skylar-slideshows/Digilog_Capstone/Hardware_Documentation/HW_design_stuff/sim/4 Design - Fader Pan/Volume Control and Digital Fader Design.docx

Volume Control and Digital Fader Design

We want a device that allows the volume of channels to be controlled with a slide potentiometer (Fader). Instead of a traditional analog design with the audio signal running through the fader’s resistance strip itself, we use a microcontroller to read the position of the fader through its resistance. That microcontroller then addresses the VCA with a control voltage that produces the specified gain/atten.

This has the benefit of being instantly recallable and able to be saved and automated digitally.

Microcontroller for each bucket of 8 faders = RP2040. $1 per bucket

The ALPS RSA0N11M9 fader was chosen. It is motorized, touch sensitive, 10kOhm linear taper. 100mm long throw length. $26x8 = $208 per bucket

THAT 2181 is chosen for VCA. $6.5*16 = $104 per bucket

For line input receiver – TI INA2134 (stereo). $6x8 = $48 per bucket

Separate analog and [digital+controllers(pots,faders)] boards. They sit on top of each other (analog bottom)

PINS: (3+32+16)

Analog GND

+18V Power

-18V Power

VCA C1L

VCA C1R

VCA C2L

…

VCA C8R

Fader1 Voltage

Fader2 Voltage

…

Fader8 Voltage

Pan1 Voltage

Pan2Voltage

…

Pan8Voltage
