skylar-slideshows/Digilog_Capstone/REPORT/report.pdf

# Analog Mixing Console with Digital Control

# and Automated Signal Path Configuration

# Capstone Project Report

## Skylar Denno

## Darya Petrova

## Evan Forcucci

## Xinhao Chen

## Luke Garrity

## Daniel Salas

Advisor: Milad Siami [Team #2]

## Northeastern University

Department of Electrical and Computer Engineering

October 9, 2026

DIGITALLY CONTROLLED ANALOG MIXER | 1

## Contents

1 Introduction | 3
2 Analog Design | 4
3 Digital Systems | 10
4 Testing and Results | 11

5 Financials | 12

## 1 Introduction

### 1.1 Background

### 1.2 Problem Statement

### 1.3 Scope and Design Goals

## 2 Analog Design

### 2.1 Analog Systems Overview

### 2.2 Voltage Controlled Amplifiers

The most fundamental part of an audio mixer is control of each individual channels’ gain before summing to the final stereo signal. To implement gain control that can be remote controlled by a voltage, voltage controlled amplifiers (VCAs) were used. Two VCAs were actually used on every channel. Since we aim to build a stereo mixer, the two VCAs feed the left and right summing channel of the mix bus, respectively. Each channel’s two VCAs may be given different gain control voltages (CVs) to pan the channel’s audio in the stereo field. For example, if a channel’s left VCA had a CV to attenuate by -90dB (basically muted) and the right VCA had the CV to add 6dB of gain, that channel’s audio would sound like it was coming from the right speaker after summing. To implement the regular fader behavior, which changes the gain of the left and right side together, both the left and right control voltages would be scaled together to change gain equally in both channels.

The specific VCA we picked for this purpose was the THAT 2180 from the Massachusetts-based THAT Corporation. It is the industry standard VCA for high fidelity audio performance. This is due to its total harmonic distortion (THD) of just 0.005% (for the ’A’ grade 2180s), which is extremely low for a VCA. Additionally, it uses a Blackmer gain cell, which has a logarithmic gain curve, allowing control voltage and decibel gain to coincide linearly. Unfortunately, in September 2026, halfway through the design of the project, THAT Corporation announced it was discontinuing its legendary 2180 series, sending shockwaves through the audio electronics community. Frantically, we bought 32 of the ’A’ grade THAT 2180s to use for this purpose, but the rest of the analog systems use clones of the THAT 2180 (Alfa RPAR AS2180, which from our tests, seems to have nearly as good performance as the genuine ’A’ grade 2180s) or the SSI2164 VCA.

Placeholder: one VCA channel — Cin, Rin, THAT2180A, I/V converter (Rf Cf ), control-port snubber, RSET

Figure 1: One channel of the pan/fader VCA stage.

Current-mode operation.

Iin = Vin

Rin

, | Iout = AI Iin, | Vout = Rf Iout | =⇒

Vout

Vin

= Rf

Rin

AI | (1)

Exponential gain control.

AI = exp

q (EC+ − EC−)

2kT

=⇒ GdB = 20 log10 AI = EC+ − EC− κ(T) ,

κ(T) = ln 10
10

kT
q

≈ 6.1 mV/dB

(2)

Temperature sensitivity.

GdB(T) = GdB(T0)

T0
T =⇒

∆GdB

GdB

≈ −∆T
T0
≈ −0.33 %/K | (3)

Operating point.

ISET = Vpin5 − VEE

RSET

= −2.85 V + 15 V
5.1 kΩ | = 2.38 mA ≥ ˆIin + ˆIout + 570 µA = 1.97 mA | (4)
Component | Value | Purpose
Rin, Rf | 20 kΩ | unity gain at 0 dB; datasheet noise/THD point
Cin | 10 µF bipolar | fc = 1/(2πRinCin) = 0.8 Hz; blocks DC
Cf | 22 pF | cancels 15 pF at pin 8 (I/V stability)
RSET | 5.1 kΩ | ISET = 2.38 mA, Eq. (4)
Port snubber 100 Ω + 2.2 nF to ground damps inductive op-amp output
Sym (pin 4) | open | keeps factory THD trim

Table 1: THAT2180A operating point.

Pan and fader law.

gL = G cos

πθ

2

, gR = G sin

πθ

2

, g²

L + g²

R = G², | θ ∈ [0, 1] | (5)

GdB,L = 20 log10 G + 20 log10 cos

πθ

2

, GdB,R = 20 log10 G + 20 log10 sin

πθ

2

| | (6)

### 2.3 Control Voltage Buffering and Temperature Drift Compensation

Placeholder: CV buffer — DAC input, Rcv + trim, Roff to −2.5 V, Rp RNTC, MFB (R2, R3, C1, C2), OPA2197, snubber at EC+

Figure 2: Control voltage buffer for one VCA.

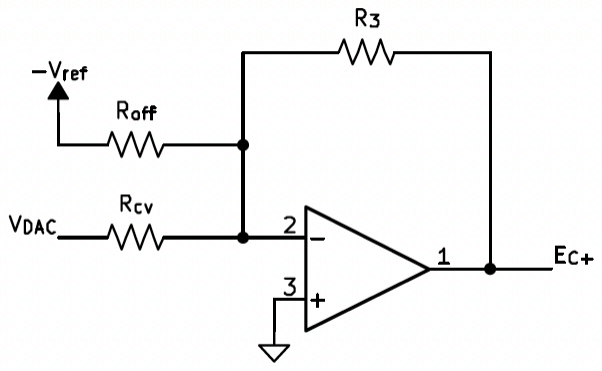
[picture p44: figure]

Figure 3: TEST

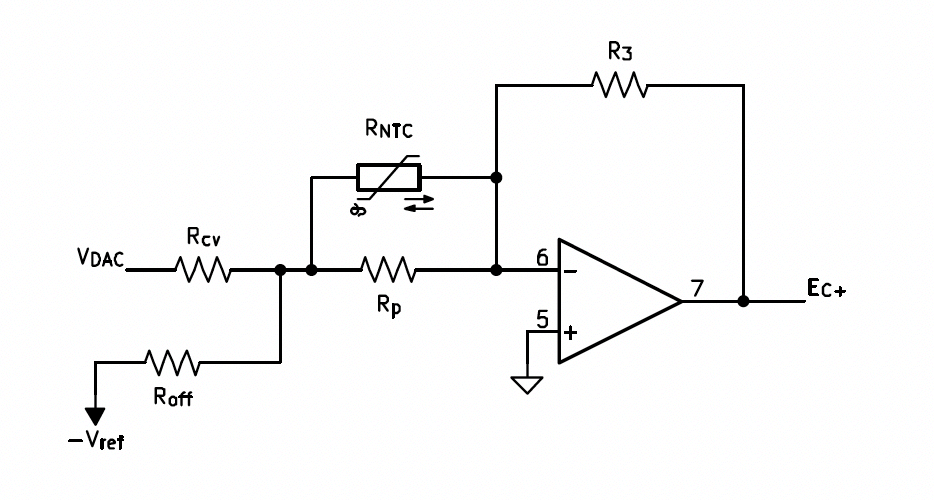
[picture p45: figure]

Figure 4: TEST

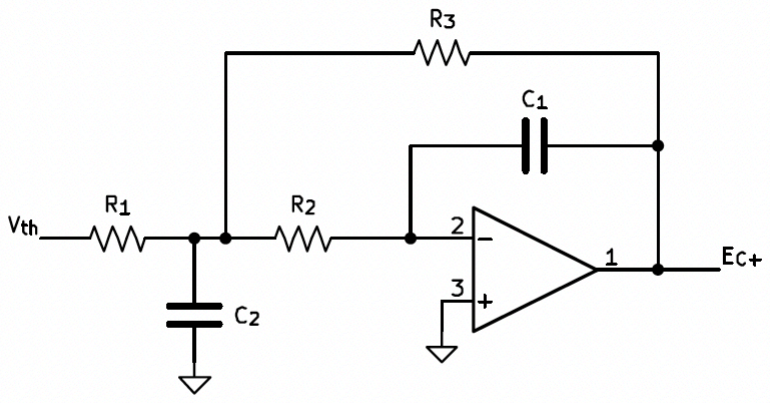
[picture p46: figure]

Figure 5: TEST

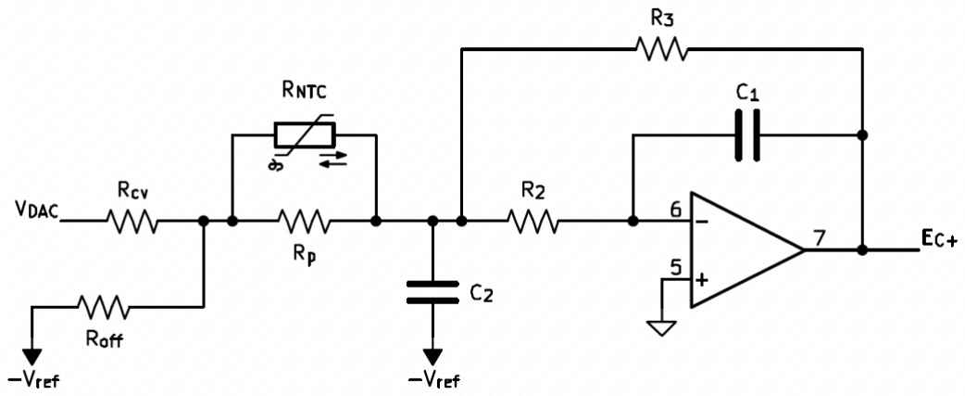
[picture p47: figure]

Figure 6: TEST

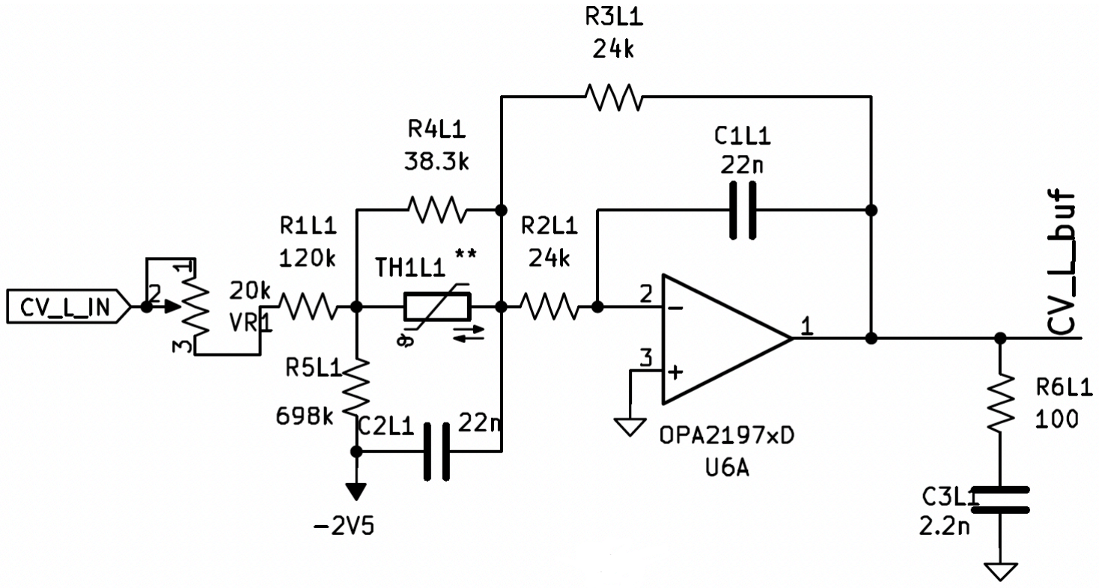
[picture p48: figure]

Figure 7: The trim potentiometer on the left is ONLY to calibrate temperature scaling during assembly, and it is not accessible to the end user.

Component Value | Role
Rcv | 120 kΩ + 20 kΩ trim (133 kΩ nom.) | DAC voltage to current; span trim
Roff | 698 kΩ | offset current
Rp RNTC | 38.3 kΩ 47 kΩ (B = 4090 K) | temperature compensation
R2 = R3 | 24 kΩ | filter and DC gain
C1 = C2 | 22 nF film | filter
Vref | 2.5 V (ADR5041 at −2.5 V, 222 µA bias) offset reference
Op-amp | OPA2197 | low offset and noise

Table 2: CV buffer component values (one channel).

DAC.
VDAC = 2VREF
4096
n = n × 1 mV, | VREF = 2.048 V, n ∈ {0, . . . , 4095} | (7)

DC transfer.

Rth = Rcv Roff, Vth = Rth

VDAC

Rcv

− Vref

Roff

, | Zt = Rp RNTC(T), | R1 = Rth + Zt

(8)
EC+ = −R3
R1

Vth = −R3 D

VDAC

Rcv

− Vref

Roff

, | D = | Rth
Rth + Zt

(9)

EC+ = 72.3 mV − 0.1518 VDAC | =⇒ GdB = 11.9 dB − 24.9 dB
V VDAC | (10)

Code mapping.
n = 72.3 mV − κ GdB
0.1518 × 1 mV | (11)
GdB | +11.9 | +6 | 0 | −3.01 | −20 | −70 | −90
n | 0 | 235 476 | 597 | 1280 3290 4095

Table 3: Example codes from Eq. (11) (nominal, before calibration).

Filtering.

EC+(s)

Vth(s) = −R3
R1

1
1 + sC1
R2 + R3 + R2R3
R1
+ s²R2R3C1C2

(12)

f0 = | 1
2π

√R2R3C1C2
= 301 Hz, Q =

√R2R3C1C2
C1 (R2 + R3 + R2R3/R1) = 0.46 | (13)

Temperature compensation.

EC+(T) = EC+(T0) T
T0

=⇒

1

EC+

dEC+

dT = 1
T0
≈ 0.33 %/K | (14)

1
D

dD

dT = −(1 − D) 1
Zt

dZt
dT | (15)

RNTC(T) = R25 e

B

1
T − 1
T25
, | dRNTC
dT | = − B
T² RNTC, | dZt
dT =

Rp

Rp + RNTC

2 dRNTC
dT (16)

(1 − D)

1
Zt

dZt
dT
T0

= 1
T0

(17)

dRNTC
dT
T0
= −2.16 kΩ/K, | 1
Zt

dZt

dT = −436 Ω/K
21.1 kΩ = −2.07 %/K,
1 − D = 0.159, | 1
D

dD
dT = 0.159 × 2.07 %/K = 0.33 %/K (18)

Calibration.
n(GdB) = na + (GdB − Ga) nb − na Gb − Ga

(19)

### 2.4 Channel Routing and Auxiliary Buses

### 2.5 Voltage Controlled State Variable Filters and EQ Circuit

### 2.6 Input Circuitry and Preamplifier

### 2.7 Hybrid Digital/Analog Dynamic Range Compressor

### 2.8 Mix Bus and Master Section

### 2.9 Channel Insert Routing Matrix

### 2.10 PCB Design Notes

## 3 Digital Systems

### 3.1 Digital Systems Overview

### 3.2 I2C Buses

### 3.2.1 I2C Communication Timings

### 3.2.2 Frames

### 3.2.3 Superframes

### 3.3 Control Panel Integration and Control Feedback

### 3.3.1 EC11 Rotary Encoders and Two-Bit Quadrature

### 3.3.2 Push-buttons and Debounce

### 3.3.3 MCP23017 GPIO Expanders

### 3.3.4 Shift-Register Based LED Scheme

### 3.4 LCD Displays

### 3.5 Saving of Console States

### 3.6 Communication Between Buckets and the Master Controller

### 3.7 USB Remote Control Computer Software

### 3.8 PCB Design Notes

## 4 Testing and Results

### 4.1 Analog Performance Metrics

### 4.1.1 Linearity / Distortion

### 4.1.2 Noise

### 4.1.3 Temperature Drift Compensation

### 4.2 Digital System Bug Testing

## 5 Financials

### 5.1 This Project’s Budget and Bill of Materials

### 5.2 Exploration of Cost Reduction for Making a Commercial Product
