skylar-slideshows/Digilog_Capstone/Written/Proposal Presentation.pdf

# Digitally Controlled Analog Music Mixing Console

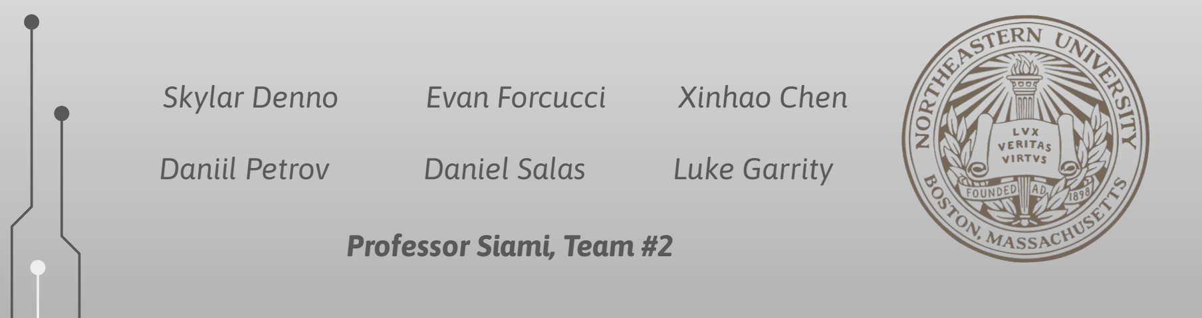
[picture p49: figure]
Skylar Denno; Evan Forcucci; Xinhao Chen; Daniil Petrov; Daniel Salas; Luke Garrity; Professor Siami, Team #2

# Mixing?

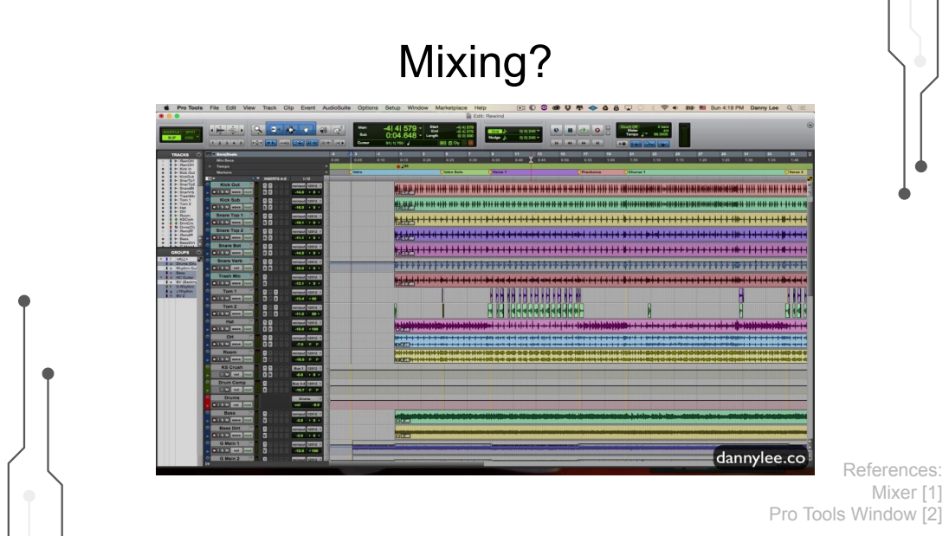
[picture p50: page 2]
References: Mixer [1]

Pro Tools Window [2]

# Traditional

x16-64

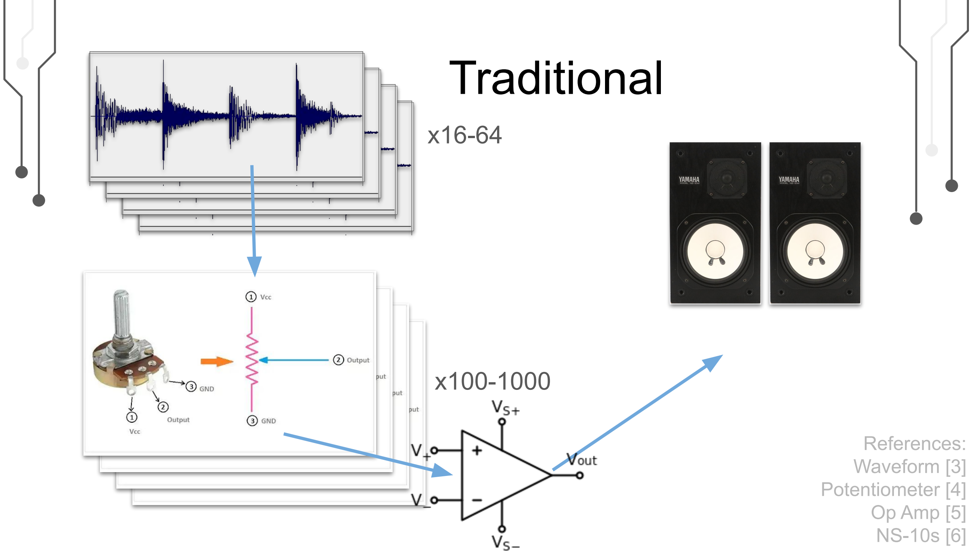
[picture p51: page 3]

x100-1000

## References: Waveform [3] Potentiometer [4] Op Amp [5] NS-10s [6]

# RECALL

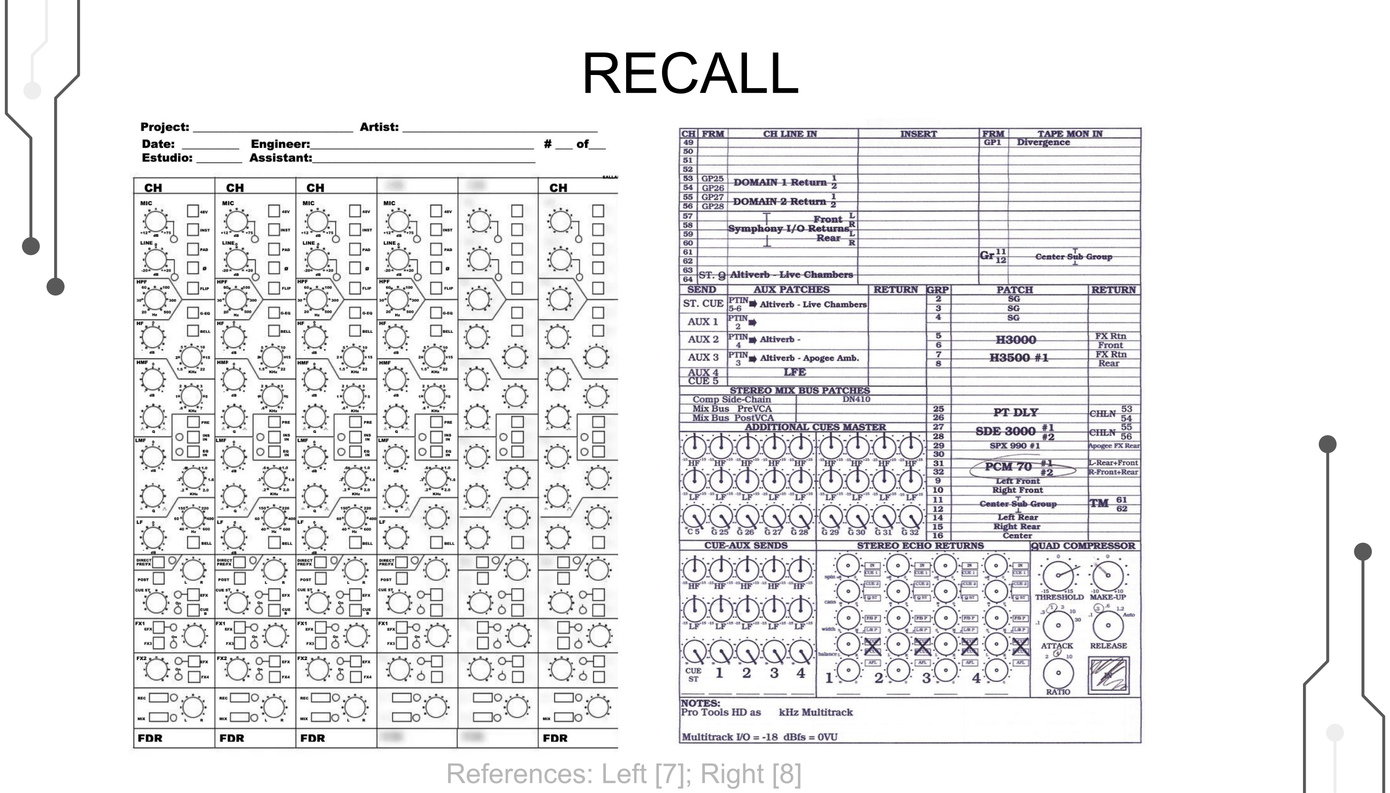
[picture p52: page 4]

## References: Left [7]; Right [8]

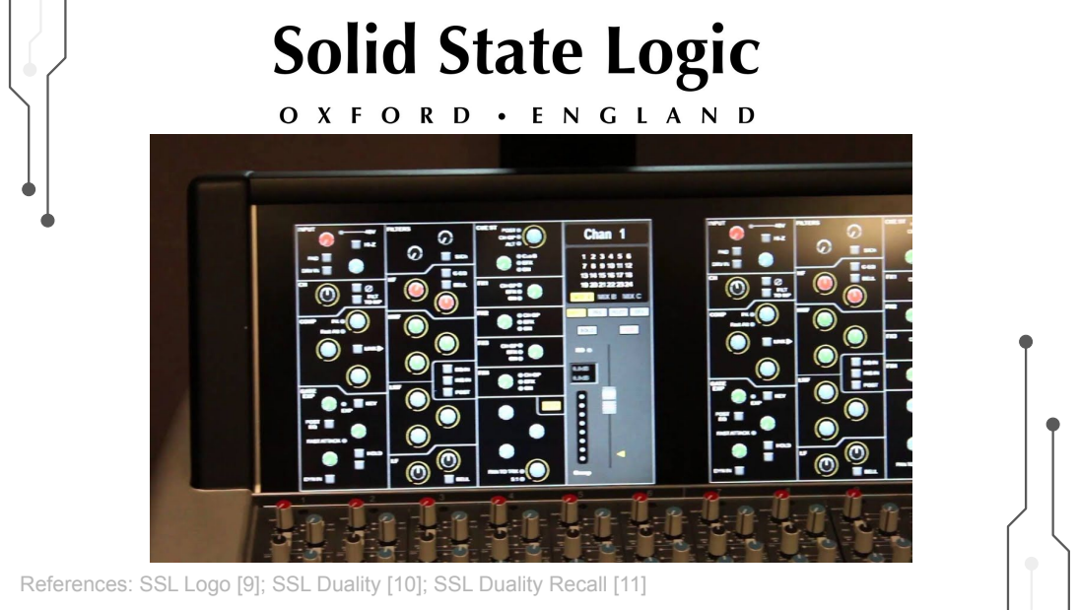
[picture p53: page 5]

References: SSL Logo [9]; SSL Duality [10]; SSL Duality Recall [11]

# OURS

## Potentiometer =

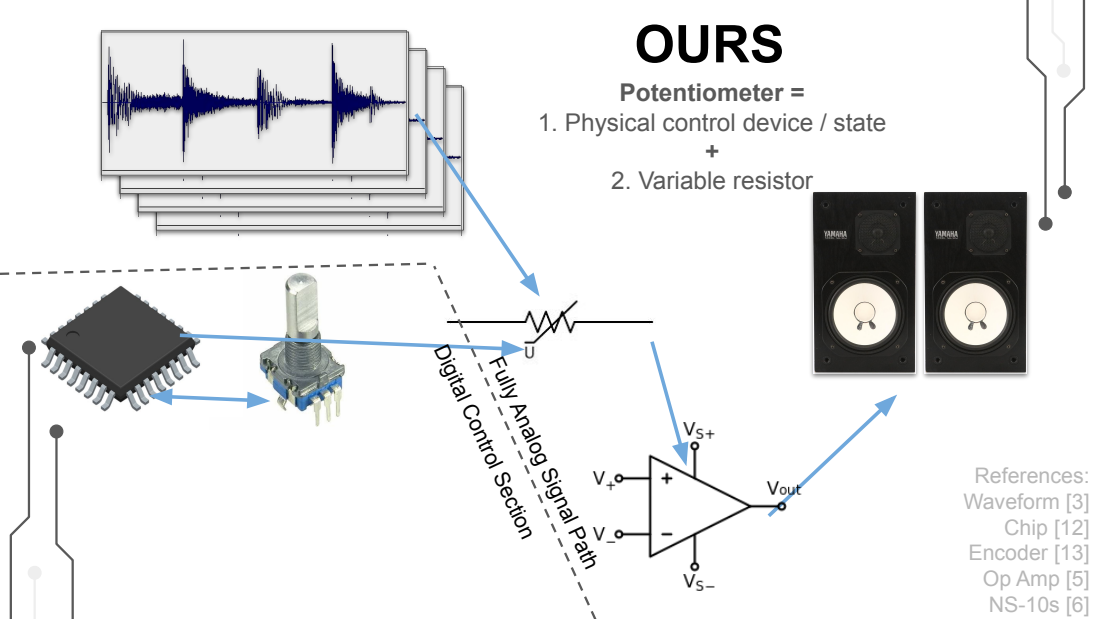
[picture p54: page 6]
+ 2. Variable resistor; References: Waveform [3] Chip [12] Encoder [13] Op Amp [5] NS-10s [6]

1. Physical control device / state

Digital Control Section

Fully Analog Signal Path

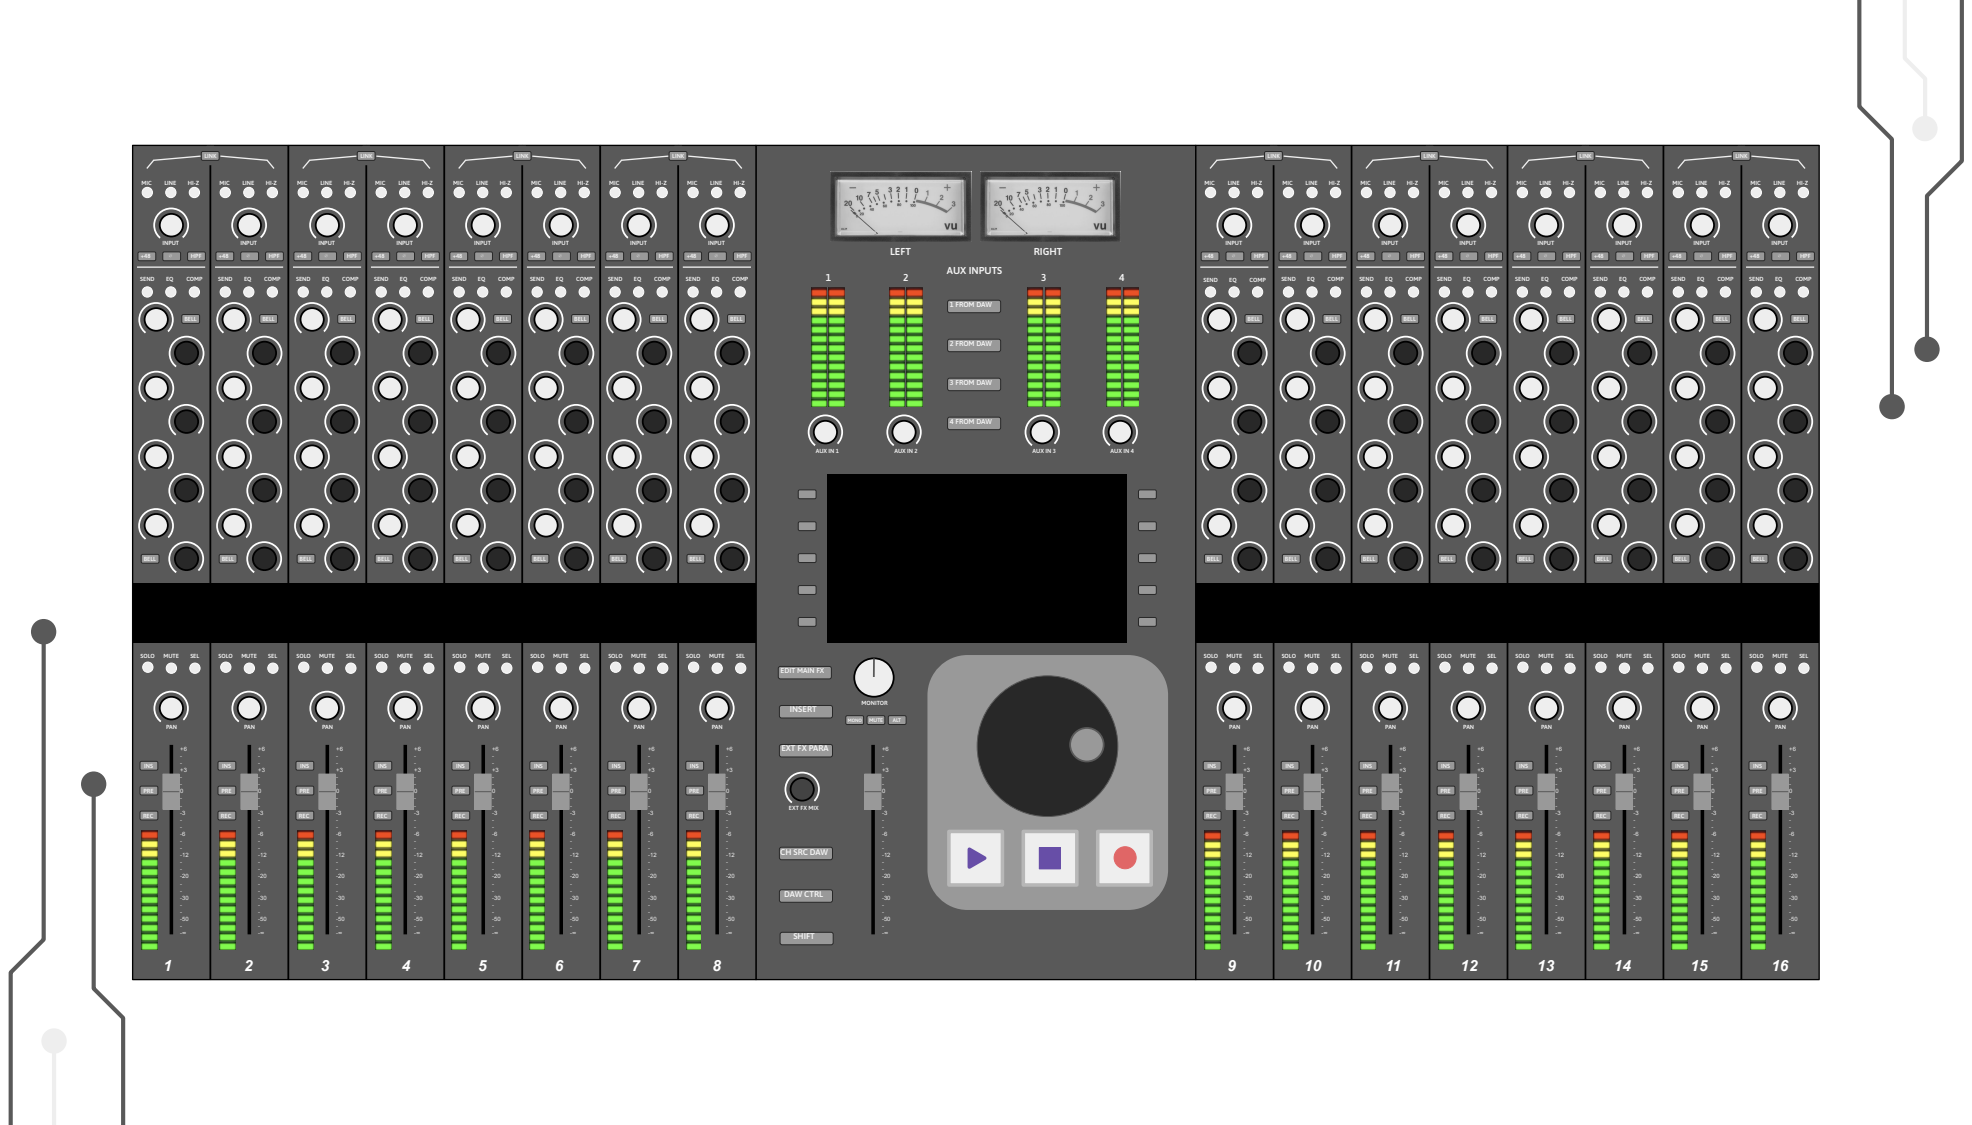
[picture p55: page 7]
SOLO; MUTE; SEL; PAN; SEND; COMP; MIC; LINE; BELL; HPF; INS; PRE; REC; LINK; INPUT; AUX IN 1; AUX IN 2; DAW CTRL; SHIFT; AUX INPUTS; 1 FROM DAW; 2 FROM DAW; 3 FROM DAW; 4 FROM DAW; AUX IN 3; AUX IN 4; LEFT; RIGHT; INSERT; MONITOR; MONO; ALT

EDIT MAIN FX

EXT FX PARA

EXT FX MIX

CH SRC DAW

# VCA

# System Diagram

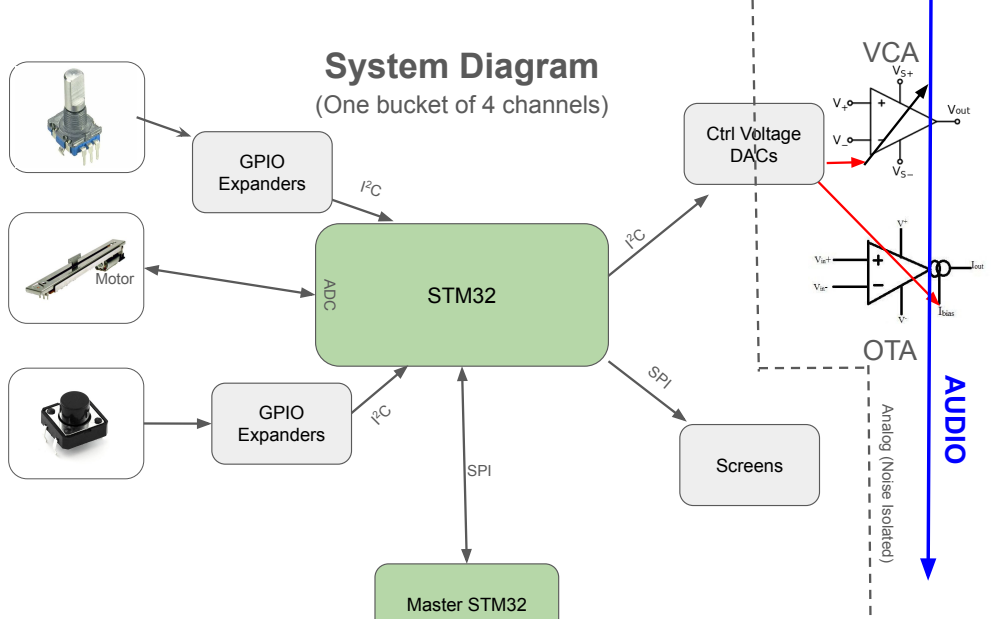
[picture p56: page 8]
STM32; GPIO Expanders; GPIO; ExpandersADC; Screens; Ctrl Voltage DACs; OTA; Master STM32; SPI; Motor; AUDIO

(One bucket of 4 channels)

Analog (Noise Isolated)

# Control Hardware Integration

### Goal: Make console easy and intuitive to use while keeping the actual

### audio path analog

### - Start with software control, then integrate physical controls

### - GPIO expansion using MCP23017 over I²C to handle a large

### number of the buttons and rotary encoders

### - Rotary encoders with LED rings for position feedback

### - Buttons, motorized faders for tactile control

### - When a saved console state is recalled, the faders can

automatically move back to the correct position.

### Overall: This part focuses on giving the user physical, tactile control

### while still allowing digital recall and automation

STM32

MCP23017 | ADC/PWM | Shift Register

Encoder
Buttons

Motorized
Faders

LED Rings

# Subteam: Xinhao & Evan

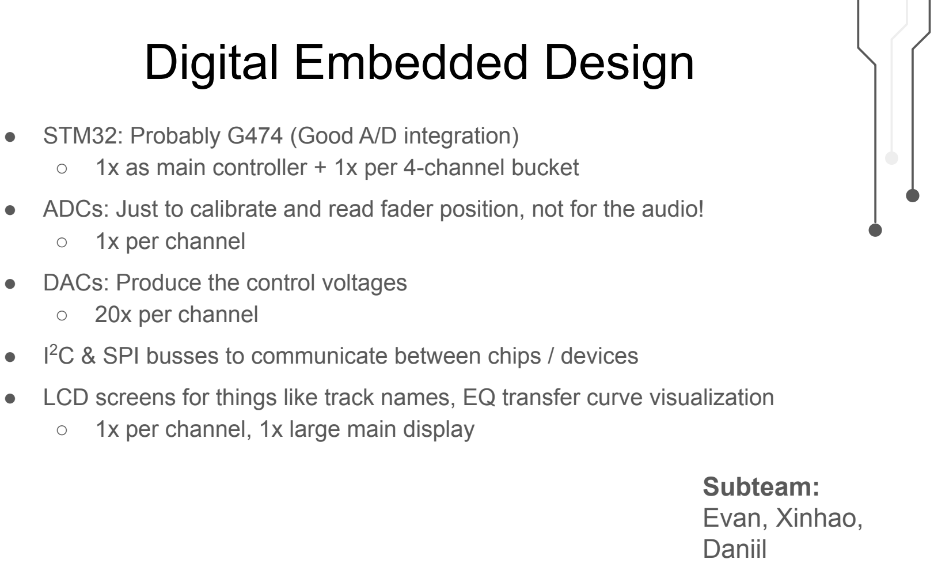
[picture p57: figure]
Digital Embedded Design; ○ 1x per channel; ● DACs: Produce the control voltages ○ 20x per channel; ○ 1x per channel, 1x large main display; Subteam: Evan, Xinhao, Daniil

## - STM32: Probably G474 (Good A/D integration) - 1x as main controller + 1x per 4-channel bucket

## - ADCs: Just to calibrate and read fader position, not for the audio!

## 2C & SPI busses to communicate between chips / devices

## - LCD screens for things like track names, EQ transfer curve visualization

# Challenge: Coordinate physical controls, analog control states, and

# user-interface feedback across the console with low latency while

# supporting state recall

# Approach: A STM32 controller manages a four-channel bucket of

# physical inputs and analog control voltage states. Another STM32 in the

# center console collects and distributes recall states. FreeRTOS is used

# to divide firmware roles into independent tasks

# Firmware

# Goals:

# - Responsive interrupt- and refresh-based interface IO

# - Full-console synchronization and instant setting recall

# Subteam: Daniil & Skylar

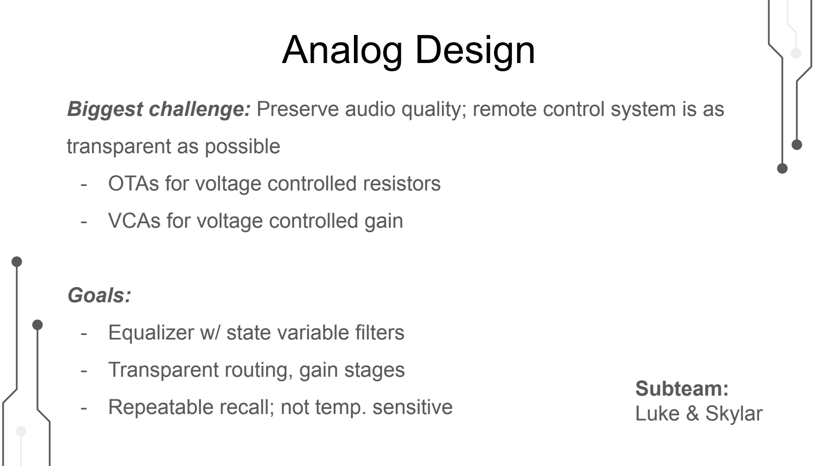
[picture p58: figure]
Analog Design; transparent as possible; - OTAs for voltage controlled resistors; - VCAs for voltage controlled gain; Goals:; - Equalizer w/ state variable filters; - Transparent routing, gain stages; Subteam: Luke & Skylar

# Biggest challenge: Preserve audio quality; remote control system is as

# - Repeatable recall; not temp. sensitive

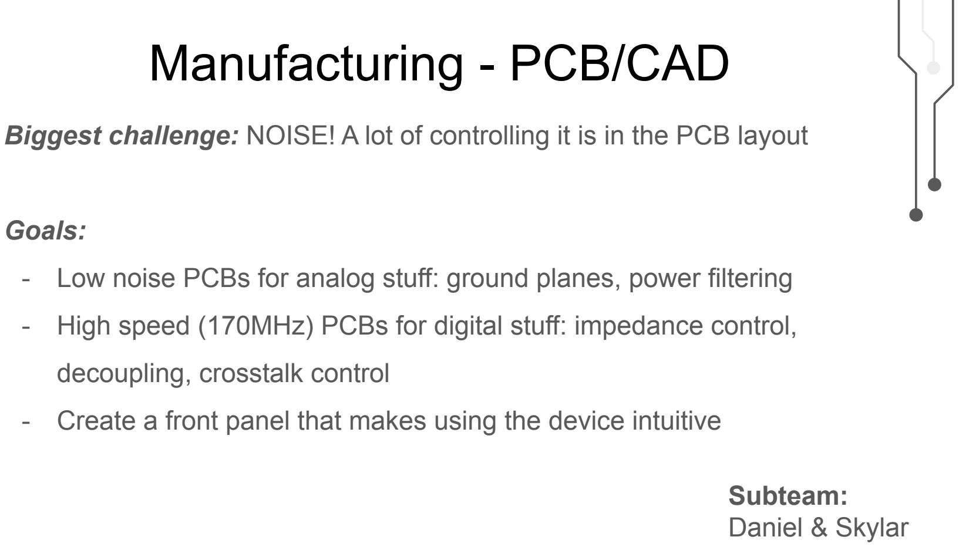
[picture p59: figure]
Manufacturing - PCB/CAD; Goals:; decoupling, crosstalk control; Subteam: Daniel & Skylar

# Biggest challenge: NOISE! A lot of controlling it is in the PCB layout

# - Low noise PCBs for analog stuff: ground planes, power filtering

- High speed (170MHz) PCBs for digital stuff: impedance control,

# - Create a front panel that makes using the device intuitive

# Timeline

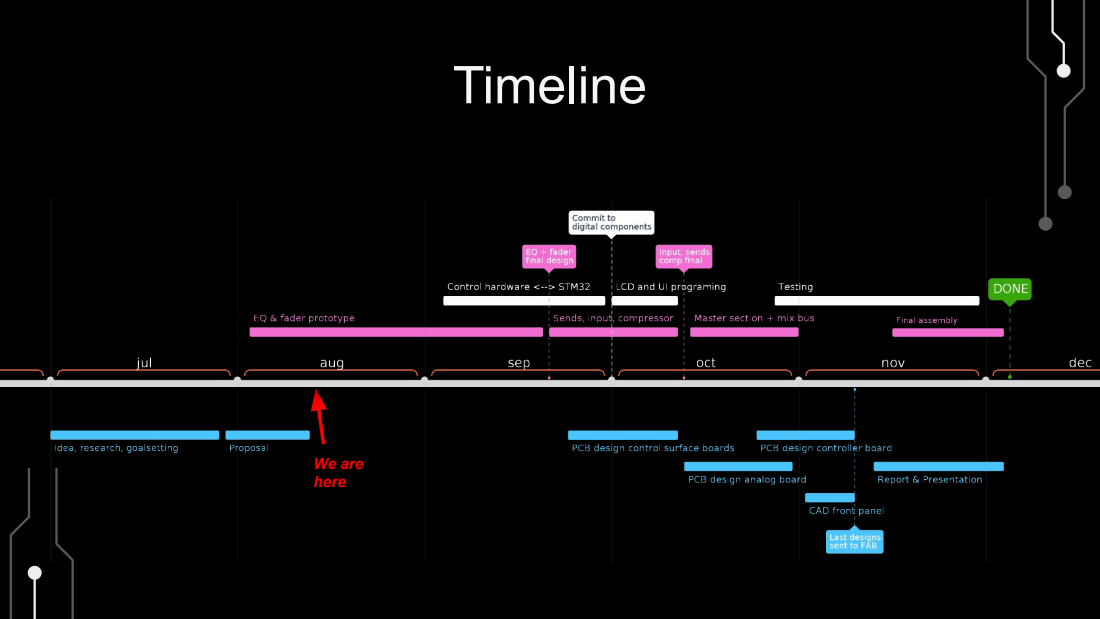
[picture p60: page 14]
We are here

# Budget - Bill of Materials

Part | Function | Qty | Unit | Total

Digital control

STM32G474 | Bucket/master MCU | 5 | $11.00 | $55.00
MCP23017 | GPIO expander | 48 | $1.71 | $82.08
MCP4728 | Control voltage DAC | 80 | $2.07 | $165.60
74HC139 | Display CS decoder | 4 | $0.21 | $0.84

User interface

05A20L22P | FFC connector | 16 | $0.07 | $1.12
TTP223-BA6 | Fader touch sensor | 17 | $0.17 | $2.89
DRV8871 | Fader H bridge | 17 | $2.15 | $36.55
74HCT595 | LED shift register | 32 | $0.14 | $4.48
AFY800480B1 | Master display | 1 | $40.86 | $40.86
Part | Function | Qty | Unit | Total

Analog signal path

NE5532 | Audio op-amp | 128 | $0.18 | $23.04
LM13700 | Transconductance | 64 | $0.75 | $48.00
OPA2134 | Summing amp | 2 | $1.74 | $3.48
SSI2164 | Quad VCA | 112 | $0.39 | $43.68
TL074 | CV amplifier | 64 | $0.21 | $13.44
INA2137 | Line receiver | 16 | $2.69 | $43.04
DG409 | Routing mux | 42 | $1.06 | $44.52
THAT1646 | Line driver | 2 | $6.02 | $12.04

Microphone input

PGA2500 | Mic preamp | 16 | $12.83 | $205.28

Fabrication

— | Front panel | 1 | $100.00 | $100.00
— | PCB fabrication | 1 | $150.00 | $150.00
— | Passives, diodes | 1 | $30.00 | $30.00
Total | | | | $1,105.94

Held by the team, not budgeted: 17 motorized faders,
160 rotary encoders, 256 illuminated buttons,
16 channel displays, LED ring boards, knob and fader caps.

Unit prices are quantity-break prices at the quantities shown. Excludes shipping, tariff, and sales tax.

# Budget - Full Build

Subsystem | Cost
Digital control | $303.52
User interface | $85.90
Analog signal path | $231.24
Microphone input stage | $205.28
PCB, panel, and passives | $280.00
Total | $1,105.94

### The microphone input stage is 16 PGA2500 preamplifiers — the single

largest line, at 19% of the build.

Excludes shipping, tariff, and sales tax.

# Budget - Scaling Down

Subsystem | 16 ch | 16 ch no mic in | 8 ch no mic in
Digital control | $303.52 | $303.52 | $151.50
User interface | $85.90 | $85.90 | $67.76
Analog signal path | $231.24 | $231.24 | $131.66
Microphone input stage | $205.28 | — | —
PCB, panel, and passives | $280.00 | $280.00 | $280.00
Total | $1,105.94 | $900.66 | $630.92
With 10% contingency | $1,216.53 | $990.73 | $694.01

Cost does not scale linearly due to bulk component pricing. PCB and panel costs are uncertain.
We will continue to explore alternatives to decrease component costs.

Excludes shipping, tariff, and sales tax.

# References

[1] "KitchenAid 3 Speed Hand Mixer, Empire Red, KHM312," Walmart. Accessed: Aug. 13, 2026. [Online image]. Available: https://www.walmart.com/ip/KitchenAid-3-Speed-Hand-Mixer-Empire-Red-KHM312/367339369
[2] Danny Danymal Lee, " Creating A Timeline Selection Marker in ProTools," YouTube, Feb. 20, 2017. Accessed: Aug. 13, 2026. [Online image]. Available: https://www.youtube.com/watch?v=GcEqr9A02ac
[3] "PIC MCU: reliably capture and measure drum transients with ADC," Electronics Stack Exchange. Accessed: Aug. 13, 2026. [Online]. Available: https://electronics.stackexchange.com/questions/506704/pic-mcu-reliably-capture-and-measure-drum-transients-with-adc
[4] "Different types of potentiometer," Onzuu. Accessed: Aug. 13, 2026. [Online]. Available: https://www.onzuu.com/blog/different-types-of-potentiometer
[5] "Operational amplifiers," Electronics-Course.com. Accessed: Aug. 13, 2026. [Online]. Available: https://electronics-course.com/opamp
[6] "A history of Yamaha studio reference monitors," Yamaha Music Hub. Accessed: Aug. 13, 2026. [Online]. Available: https://hub.yamaha.com/proaudio/recording/a-history-of-yamaha-studio-reference-monitors/
[7] "SSL AWS 900 channel strip recall sheet," Course Hero. Accessed: Aug. 13, 2026. [Online]. Available: https://www.coursehero.com/file/119674766/SSL-AWS-900-Channel-Strip-Recall-Sheet-3pdf/
[8] "Recall sheets," Wolff Audio. Accessed: Aug. 13, 2026. [Online]. Available: https://www.wolffaudio.com/support/recall-sheets
[9] Solid State Logic, "Solid State Logic company logo," Solid State Logic. Accessed: Aug. 13, 2026. [Online image]. Available: https://solidstatelogic.com/
[10] "SSL Duality Delta 24 channel studio mixing console with DAW control," Studiocare. Accessed: Aug. 13, 2026. [Online image]. Available: https://studiocare.com/products/ssl-duality-delta-24-channel-studio-mixing-console-with-daw-control-poa
[11] Joe Gill, " SSL Duality Total Recall - Tutorial," YouTube, Dec. 12, 2013. Accessed: Aug. 13, 2026. [Online video]. Available: https://www.youtube.com/watch?v=Bu9bETpqT60
[12] E. Odunlade, "Top 10 popular microcontrollers among makers," Electronics-Lab, June 19, 2020. Accessed: Aug. 13, 2026. [Online]. Available: https://www.electronics-lab.com/top-10-popular-microcontrollers-among-makers/
[13] "Rotary encoder on a single MCU pin," Elektor Magazine. Accessed: Aug. 13, 2026. [Online]. Available: https://www.elektormagazine.com/labs/rotary-encoder-on-a-single-mcu-pin

# What are your questions?

# Github Repository

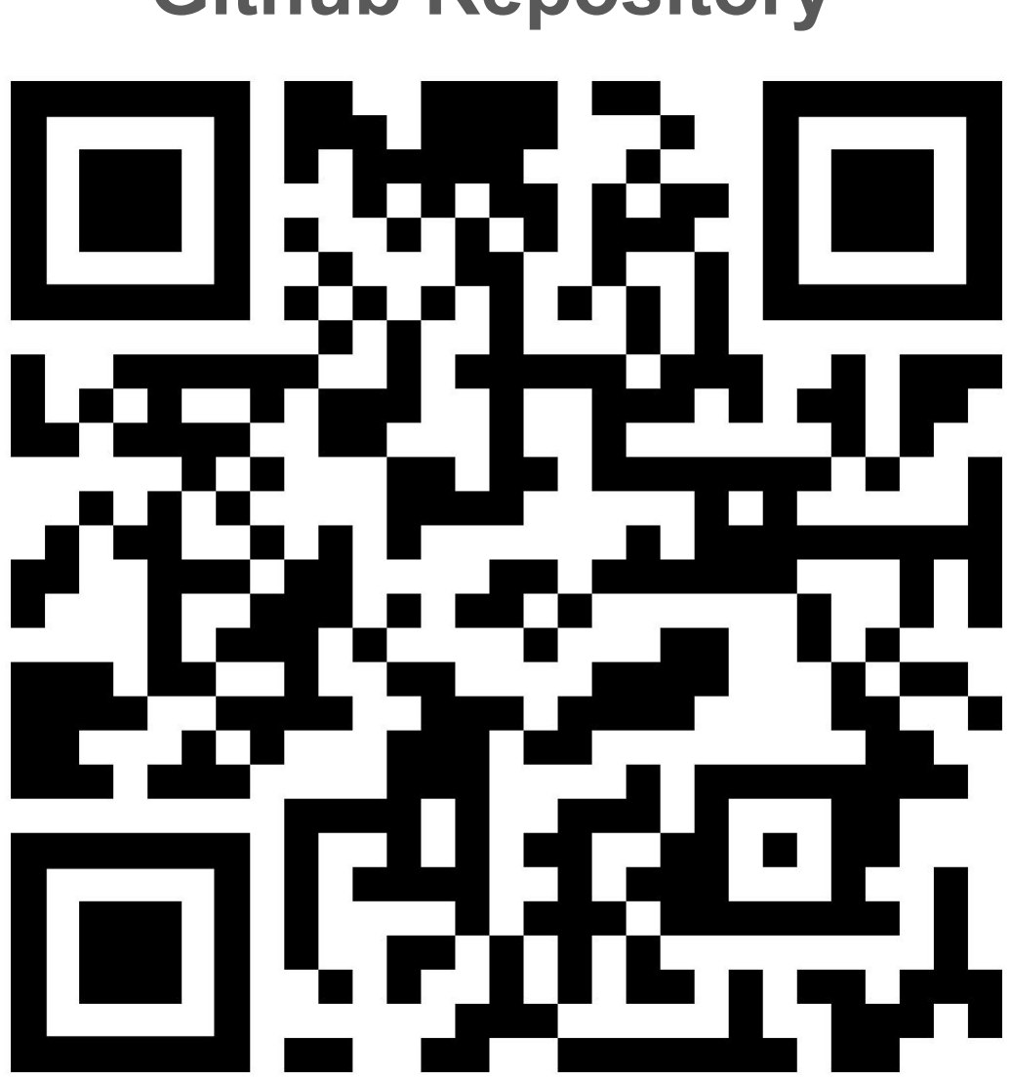
[picture p61: figure]

# https://github.com/skylar-slideshows/Digilog_Capstone
