skylar-slideshows/Digilog_Capstone/Hardware_Documentation/Reference_Schematics/DEVBOARD_MCP4728.pdf

# Schematic

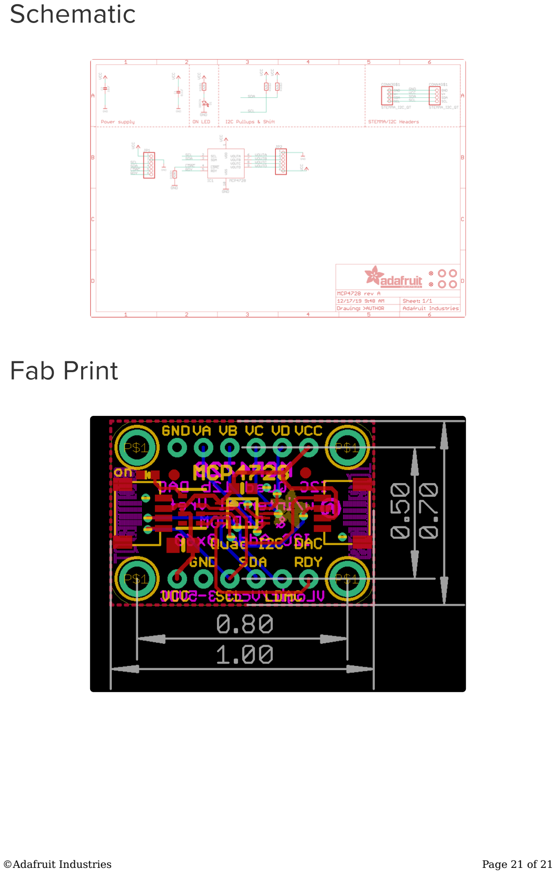
[picture p62: page 1]

# Fab Print

©Adafruit Industries | Page 21 of 21
