skylar-slideshows/Digilog_Capstone/Written/pitch deck.pdf

# Digitally Controlled Analog Mixing Console

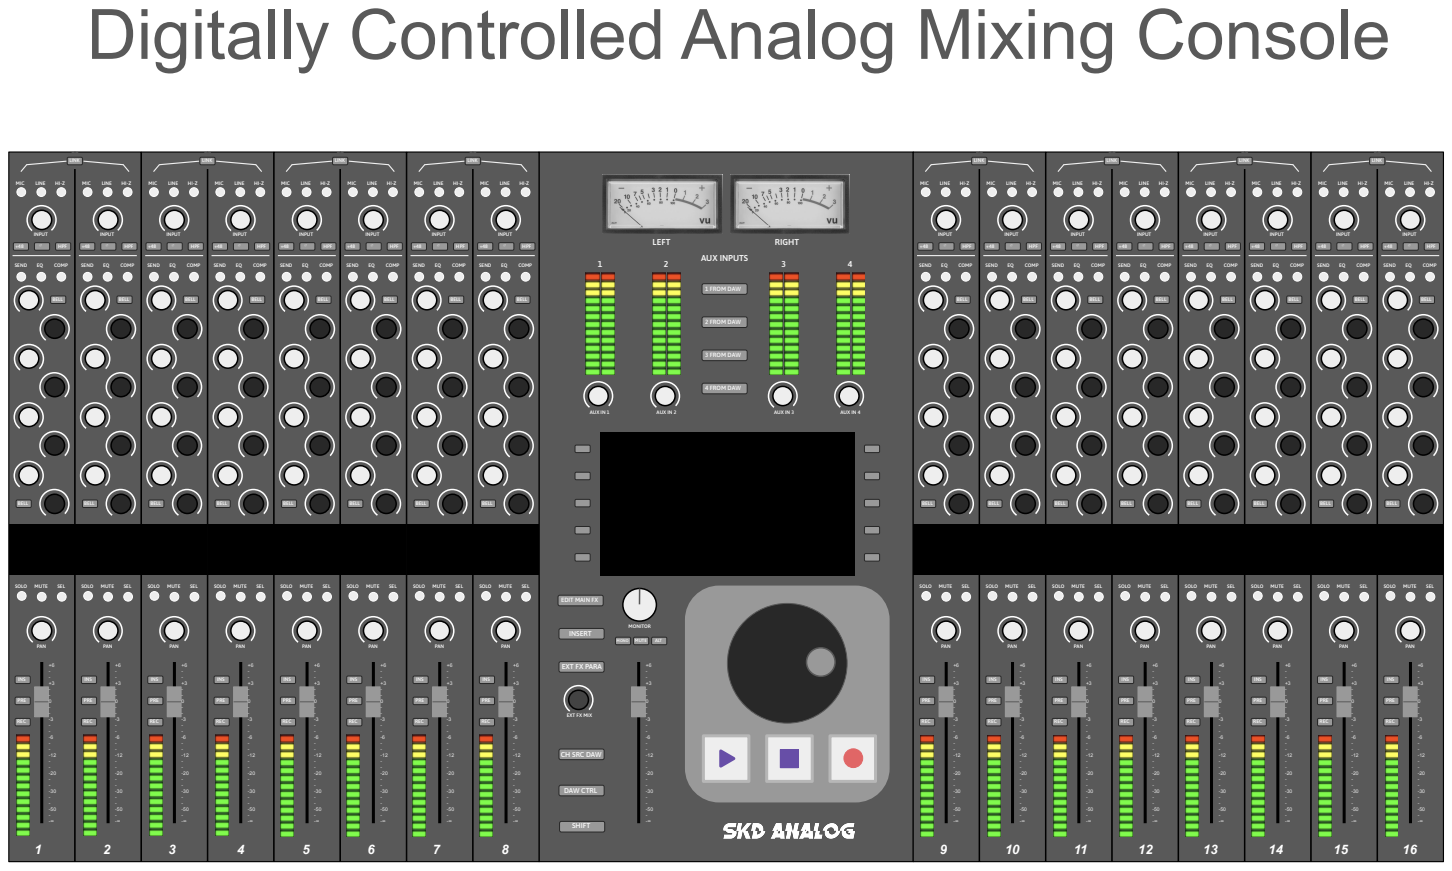
[picture p63: page 1]
SOLO; MUTE; SEL; PAN; SEND; COMP; MIC; LINE; BELL; HPF; INS; PRE; REC; LINK; INPUT; AUX IN 1; AUX IN 2; DAW CTRL; SHIFT; AUX INPUTS; 1 FROM DAW; 2 FROM DAW; 3 FROM DAW; 4 FROM DAW; AUX IN 3; AUX IN 4; LEFT; RIGHT; INSERT; MONITOR; MONO; ALT

EDIT MAIN FX

EXT FX PARA

EXT FX MIX

CH SRC DAW

# Mixing?

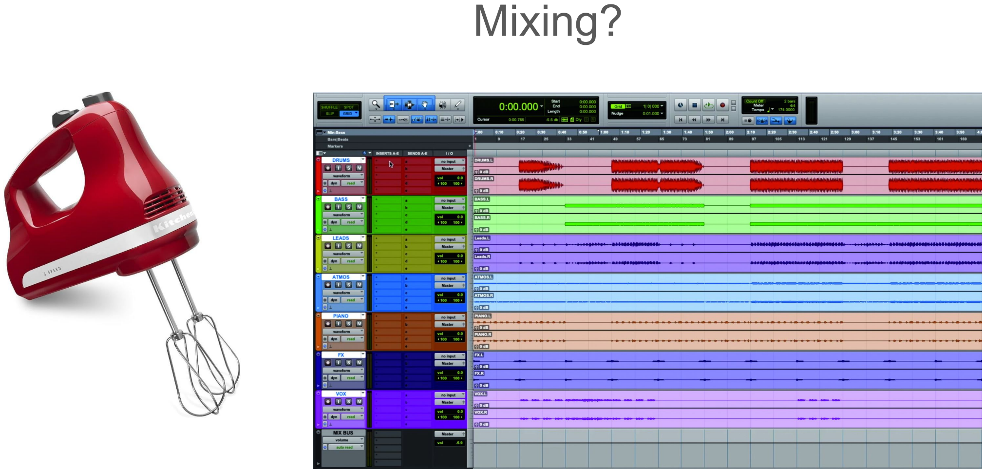
[picture p64: page 2]

# Traditional

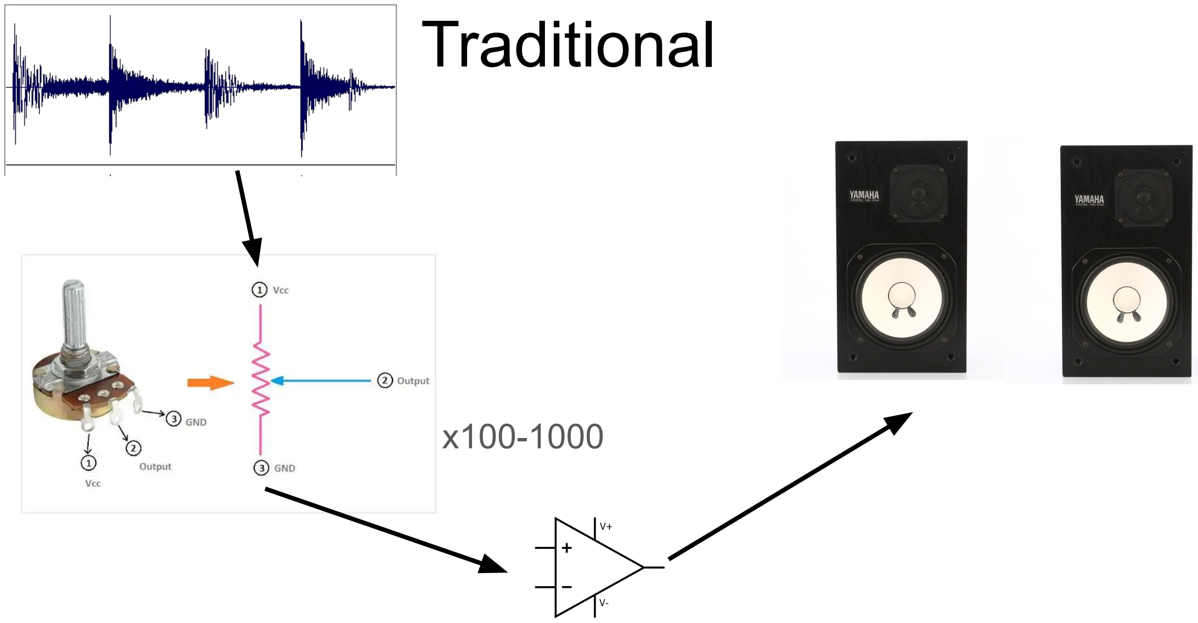
[picture p65: page 3]

x100-1000

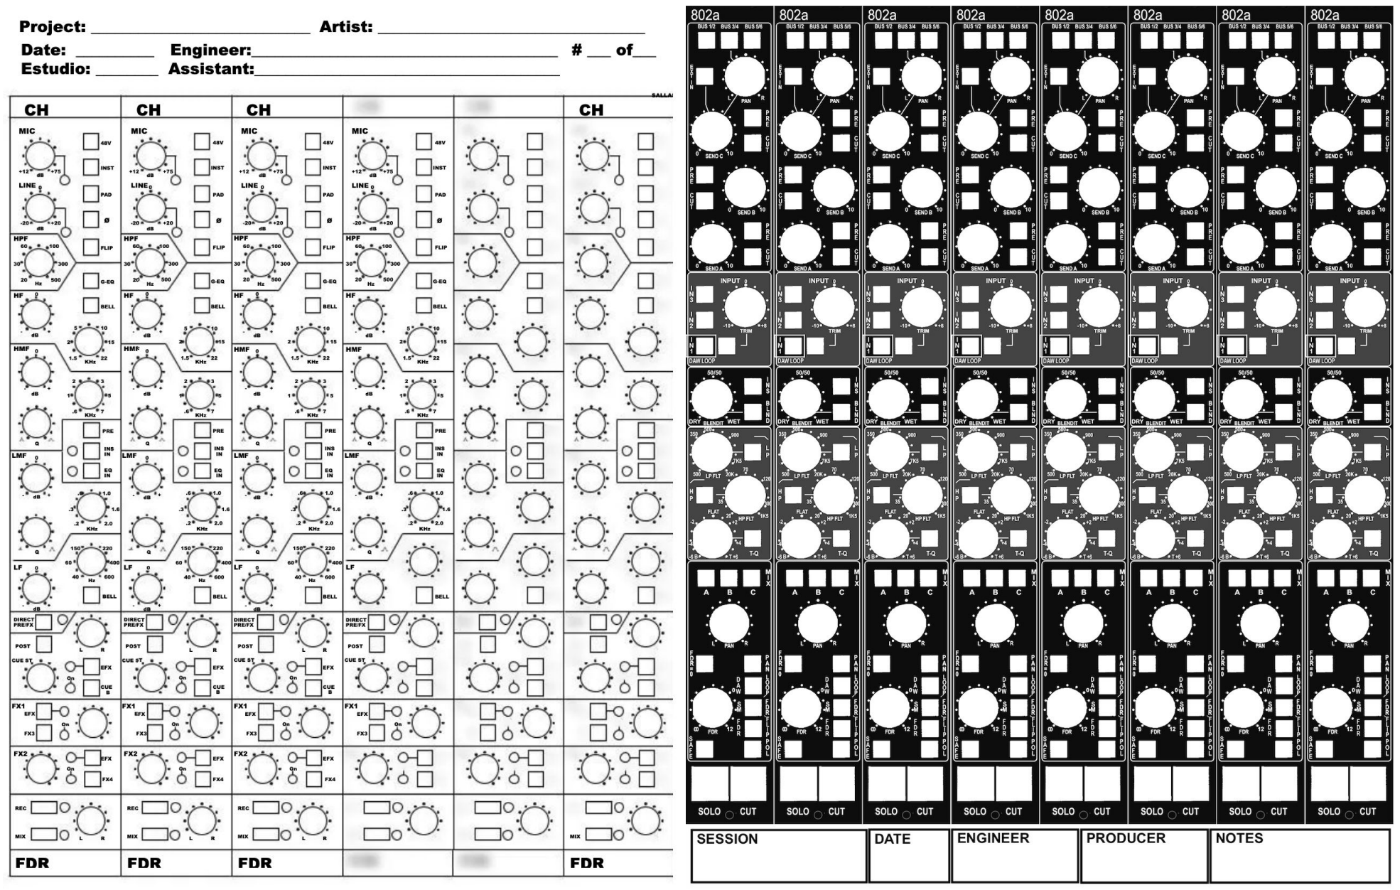
[picture p66: page 4]

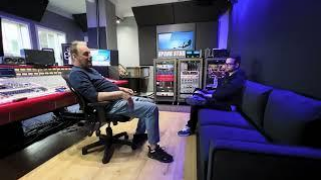
[picture p67: figure]

# SSL “Total Recall”

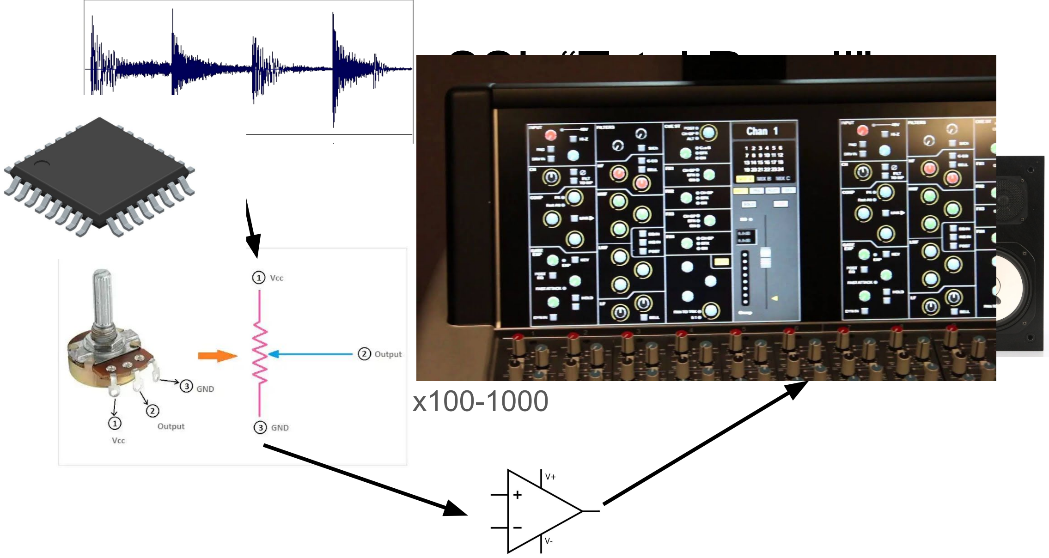
[picture p68: page 6]

x100-1000

# OURS

# Potentiometer =

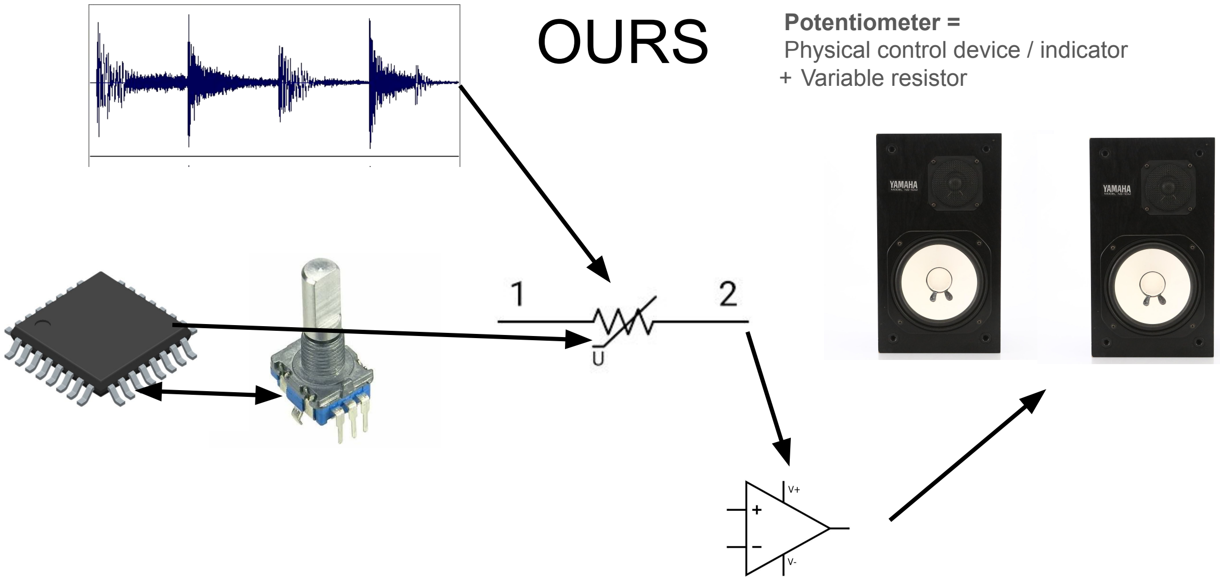
[picture p69: page 7]

# Physical control device / indicator + Variable resistor

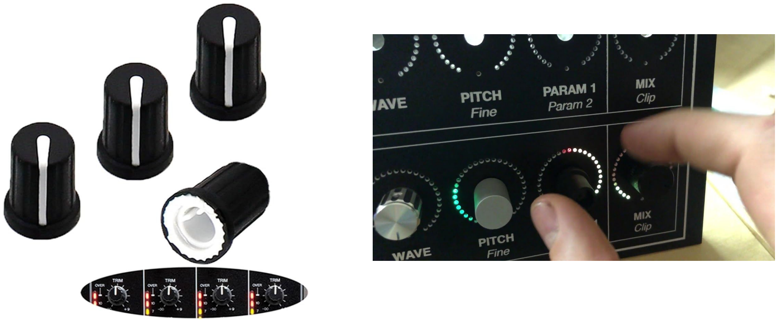
[picture p70: page 8]
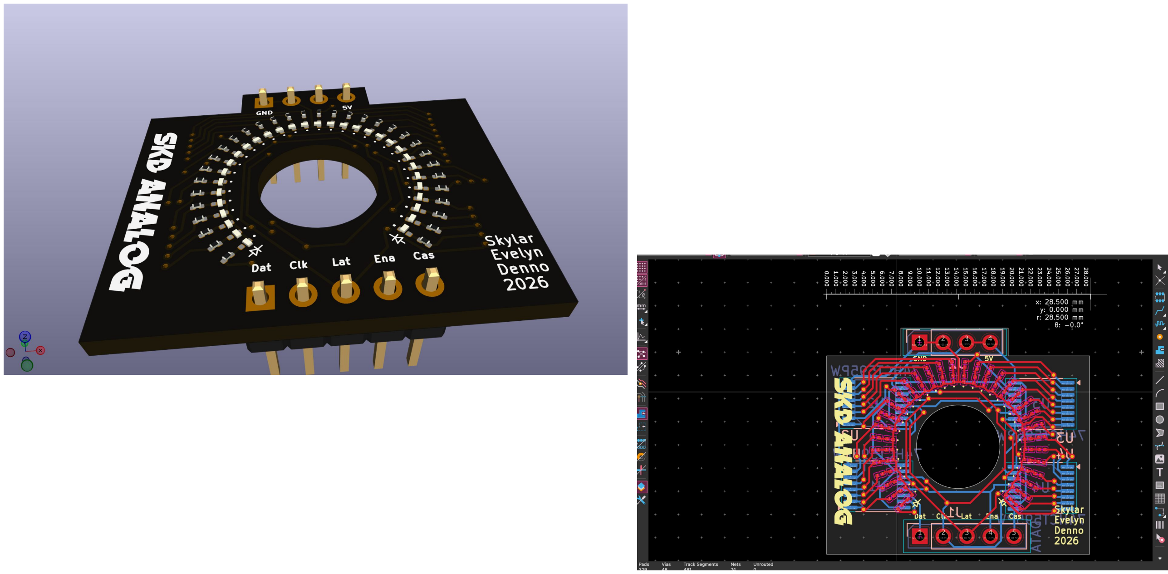
[picture p71: page 9]

# Voltage Controlled Resistors??

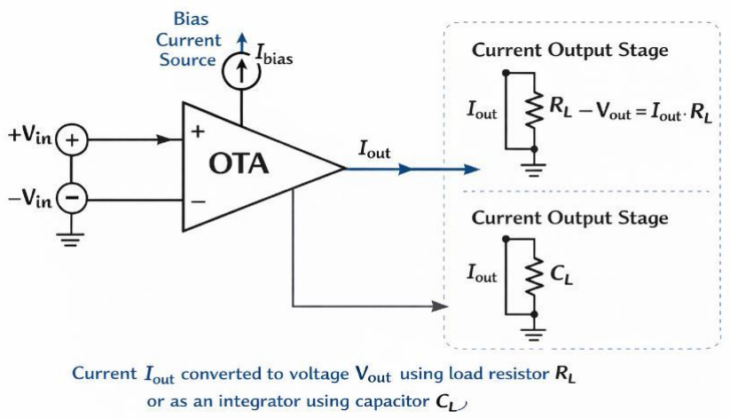
[picture p72: figure]

# Voltage Controlled Amplifiers

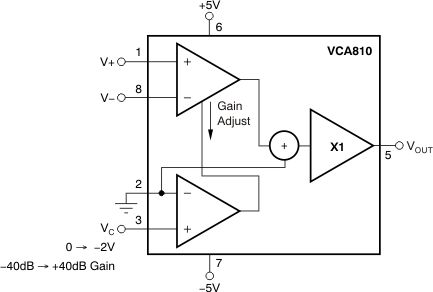
[picture p73: figure]

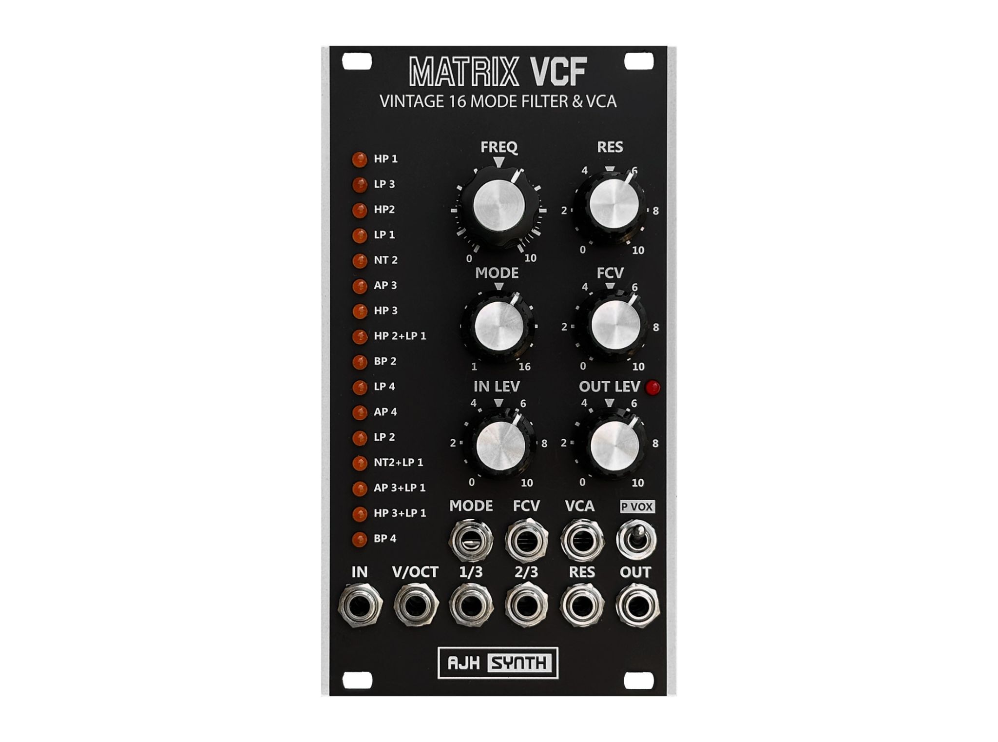
[picture p74: figure]

# Benefits

# - Instant recall and saving of progress

# - High recall consistency / accuracy

# - Multiple versions of mixes

# - Easy automation of multiple parameters

# - Smaller (one knob control be multiple things

# LTSPICE

## AUX INPUTS

1 2

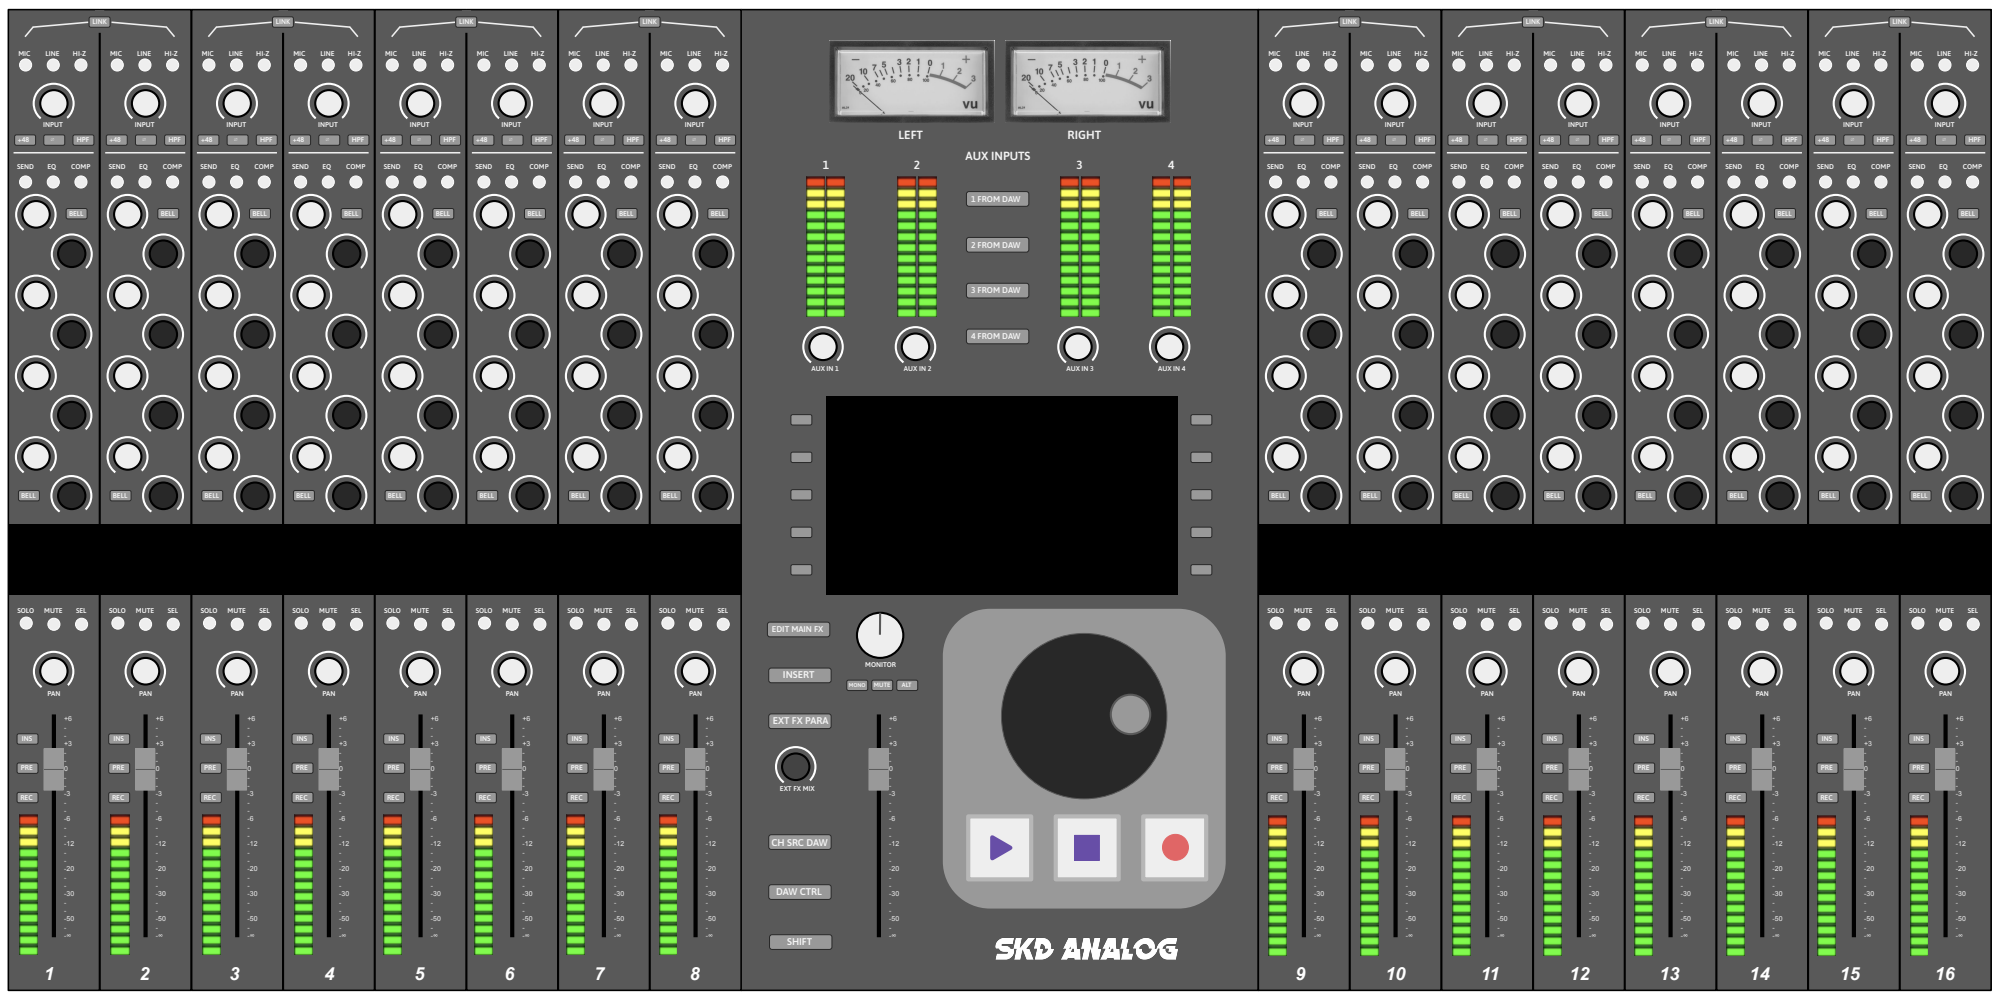
[picture p75: page 15]
SOLO; MUTE; SEL; PAN; SEND; COMP; MIC; LINE; BELL; HPF; INS; PRE; REC; LINK; INPUT; AUX IN 1; AUX IN 2; DAW CTRL; SHIFT; 1 FROM DAW; 2 FROM DAW; 3 FROM DAW; 4 FROM DAW; AUX IN 3; AUX IN 4; LEFT; RIGHT; INSERT; MONITOR; MONO; ALT

EDIT MAIN FX

EXT FX PARA

EXT FX MIX

CH SRC DAW

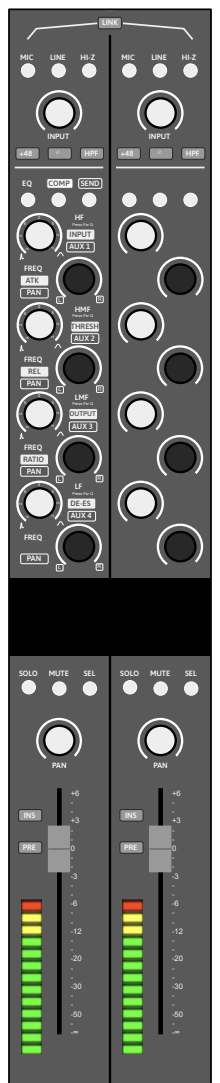
[picture p76: page 16]
SOLO; MUTE; SEL; PAN; COMP; SEND; MIC; LINE; HPF; INS; PRE; LINK; INPUT; FREQ; Press For Q; HMF; LMF; ATK; THRESH; REL; OUTPUT; RATIO; AUX 1; AUX 2; AUX 3; AUX 4

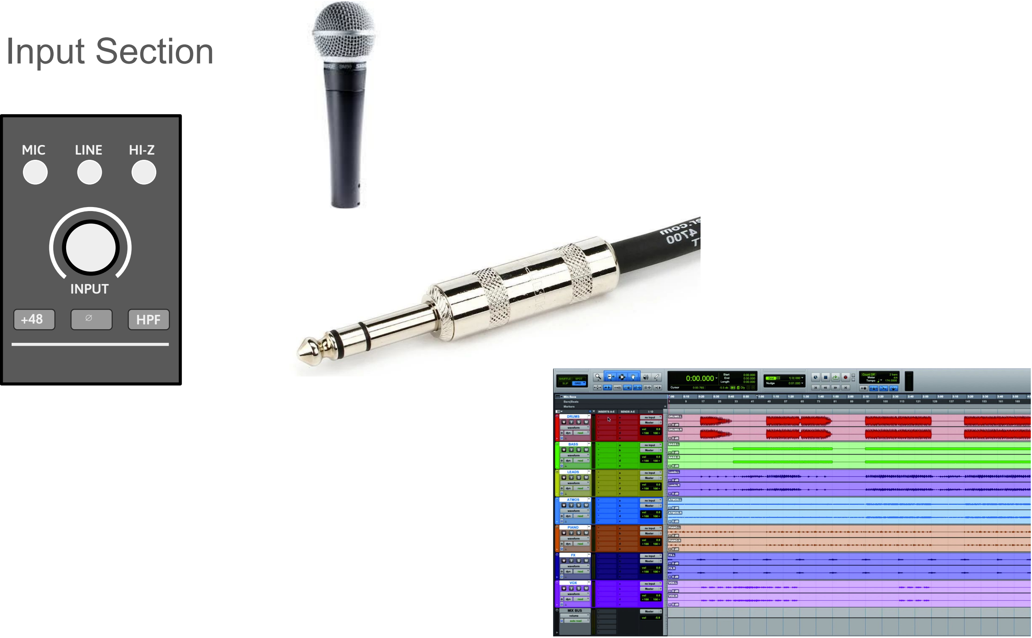
[picture p77: figure]
MIC; LINE; INPUT; HPF; Input Section

EQ | COMP | SEND

HF

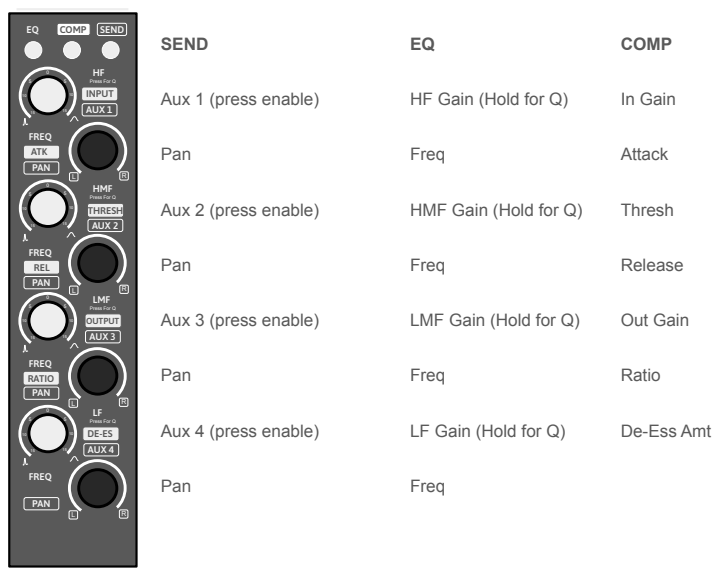
[picture p78: page 18]
FREQ; Press For Q; HMF; LMF; INPUT; ATK; THRESH; REL; OUTPUT; RATIO; AUX 1; PAN; AUX 2; AUX 3; AUX 4; SEND; Pan; Freq; COMP; In Gain; Attack; Thresh; Release; Out Gain; Ratio

Aux 1 (press enable)

HF Gain (Hold for Q)

Aux 2 (press enable)

HMF Gain (Hold for Q)

Aux 3 (press enable)

LMF Gain (Hold for Q)

Aux 4 (press enable)

LF Gain (Hold for Q)

De-Ess Amt

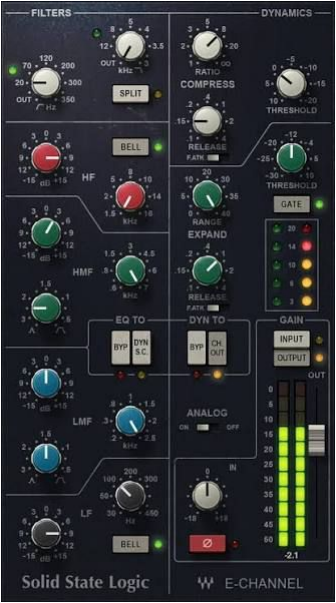
[picture p79: figure]

EQ | COMP | SEND

HF

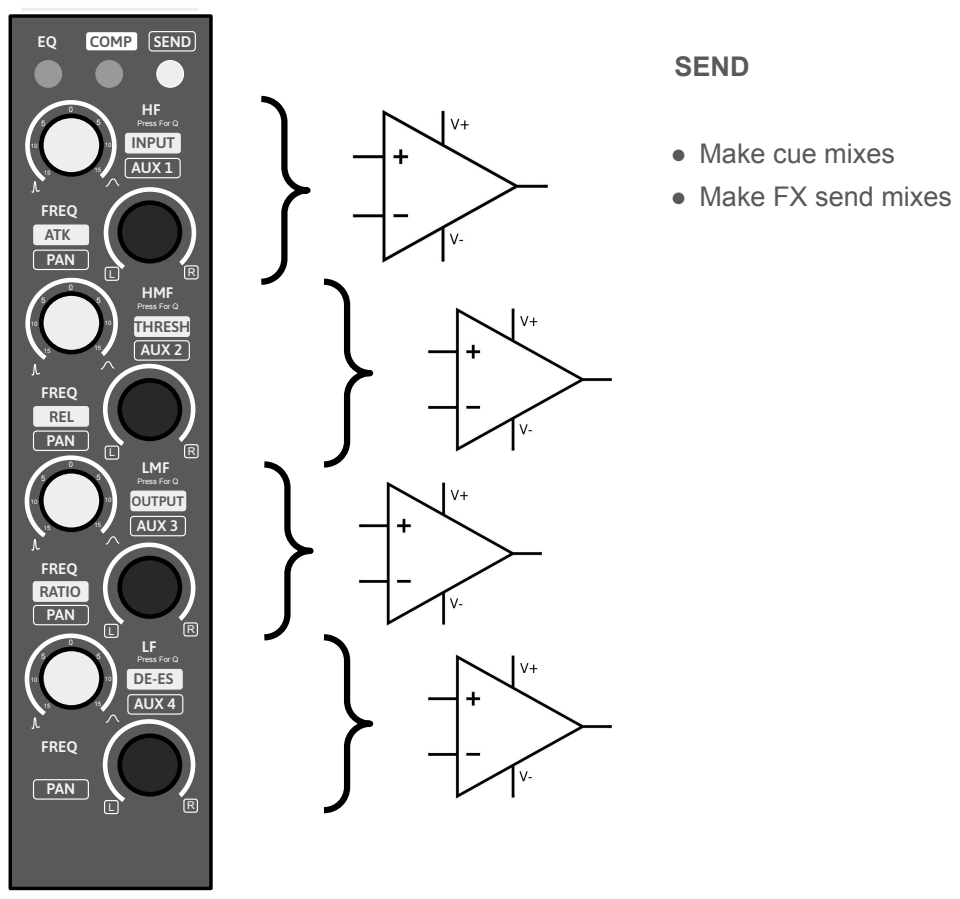
[picture p80: page 20]
FREQ; Press For Q; HMF; LMF; INPUT; ATK; THRESH; REL; OUTPUT; RATIO; AUX 1; PAN; AUX 2; AUX 3; AUX 4

SEND ● Make cue mixes ● Make FX send mixes

SOLO | MUTE | SEL

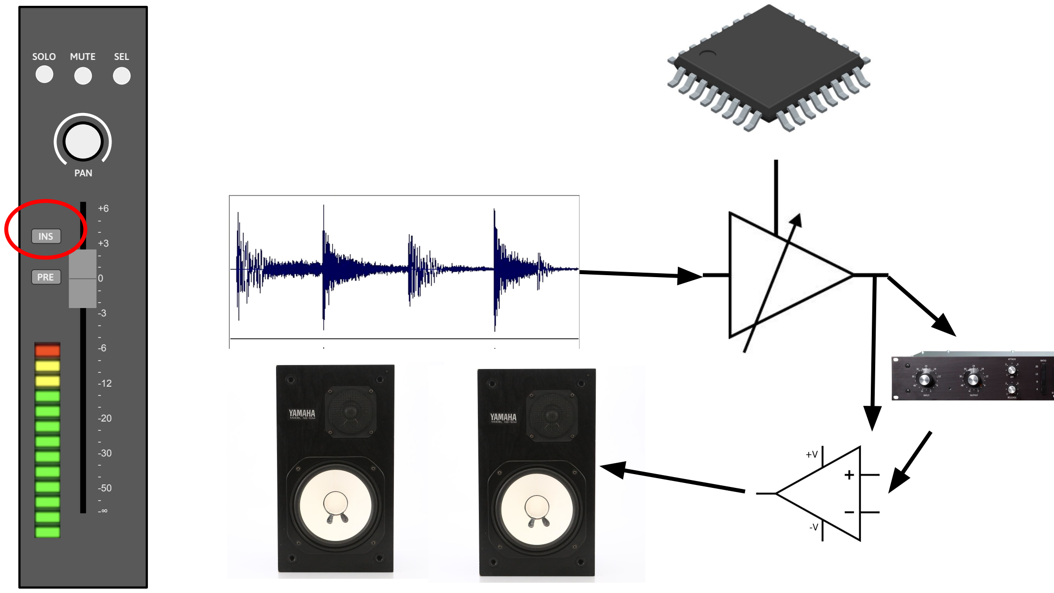
[picture p81: page 21]

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
# PAN

# INS

# PRE
