skylar-slideshows/Digilog_Capstone/Firmware_Documentation/images/diagram2.png

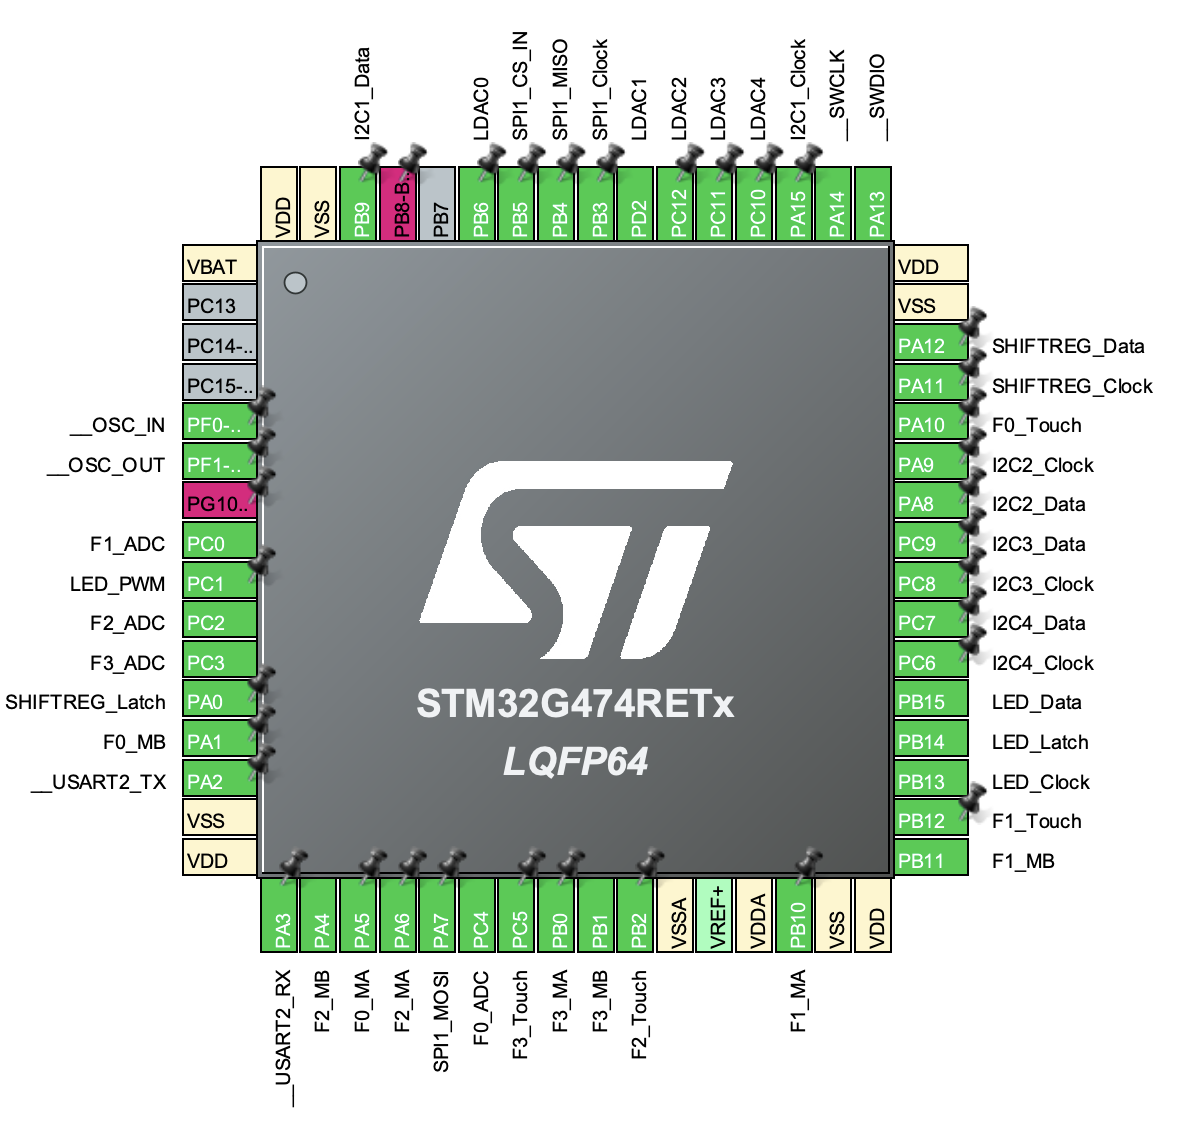
Firmware_Documentation/images/diagram2.png
