skylar-slideshows/Digilog_Capstone/PCB_CAD/05 PSU/3d.png

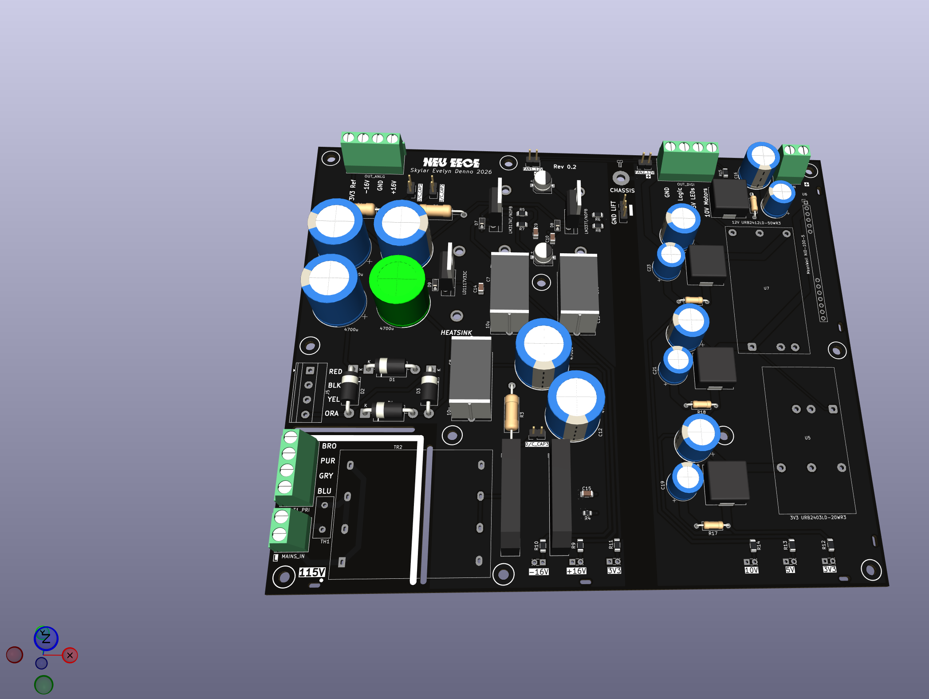
PCB_CAD/05 PSU/3d.png
