skylar-slideshows/Digilog_Capstone/Written/WRITTEN_PROPOSAL/budget1.png

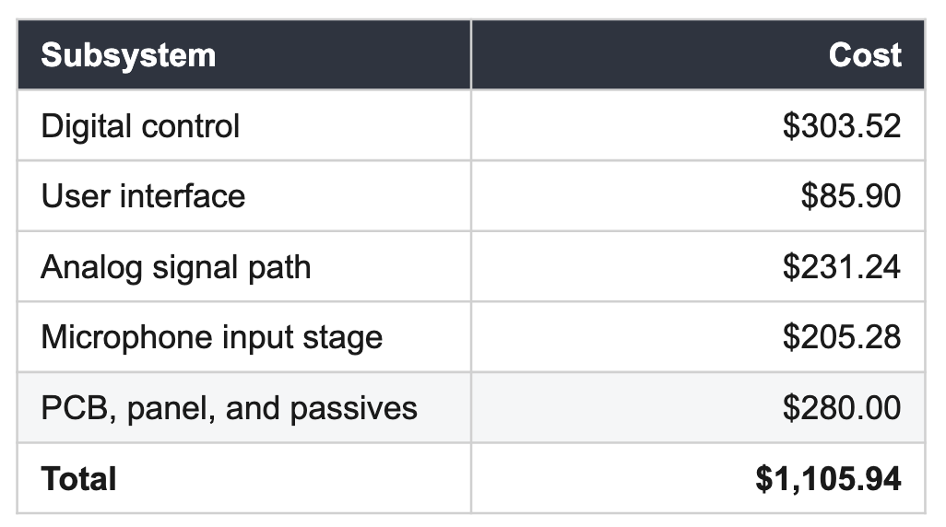
Written/WRITTEN_PROPOSAL/budget1.png
