skylar-slideshows/Digilog_Capstone/Written/WRITTEN_PROPOSAL/budget2.png

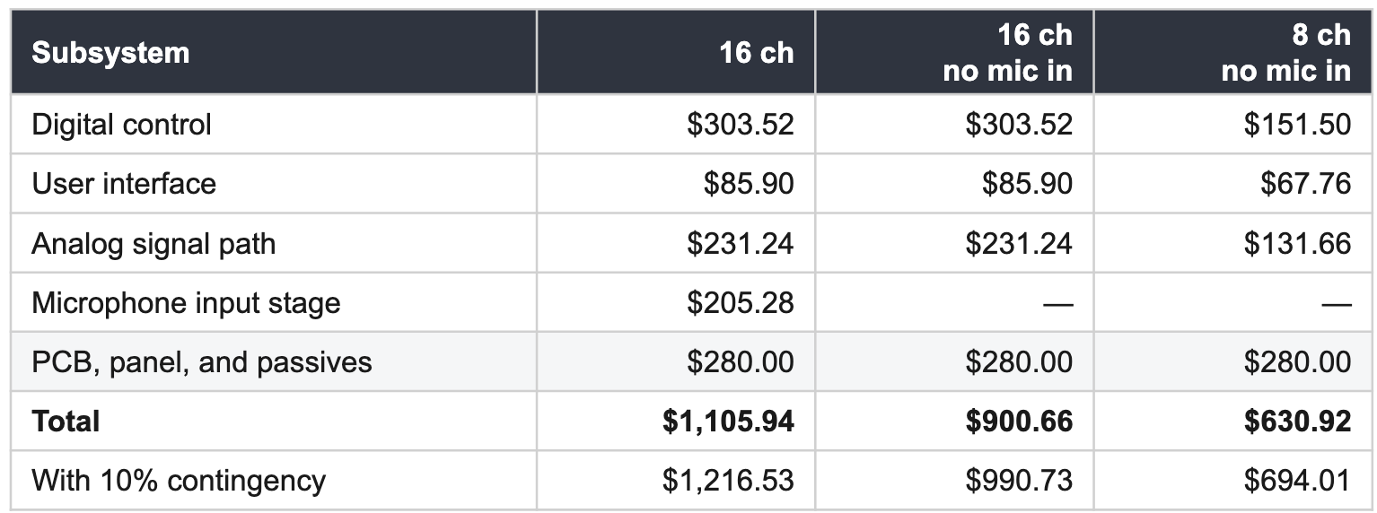
Written/WRITTEN_PROPOSAL/budget2.png
