skylar-slideshows/Digilog_Capstone/PCB_CAD/Development Boards/_DEV_EC11_button_breakout/production/bom.csv

Designator | Footprint | Quantity | Value | LCSC Part #
C1 | 0603 | 1 | 1u | C15849
C2, C3, C4 | 0603 | 3 | 10n | C57112
D1 | D_SOD-323 | 1 | 1N4148 | C2128
J1, J2 | PinHeader_1x04_P2.54mm_Vertical | 2 | Conn_01x04_Pin | dnp
R1 | 0603 | 1 | 47k | C25819
R2 | 0603 | 1 | 15k | C22809
R3, R4, R5 | 0603 | 3 | 10k | C25804
R6, R7, R8 | 0603 | 3 | 1k | C21190
R9 | 0603 | 1 | 330 | C23138
SW1 | EC11J0924411 | 1 | EC11_Rotary_Encoder | dnp
SW2 | CFPB-1CC-4W6 | 1 | SW_Push_LED | dnp
U1 | SOIC-14_3.9x8.7mm_P1.27mm | 1 | 74HC14 | C5605
