skylar-slideshows/Digilog_Capstone/PCB_CAD/05 PSU/pcb_sheet_editor.pdf

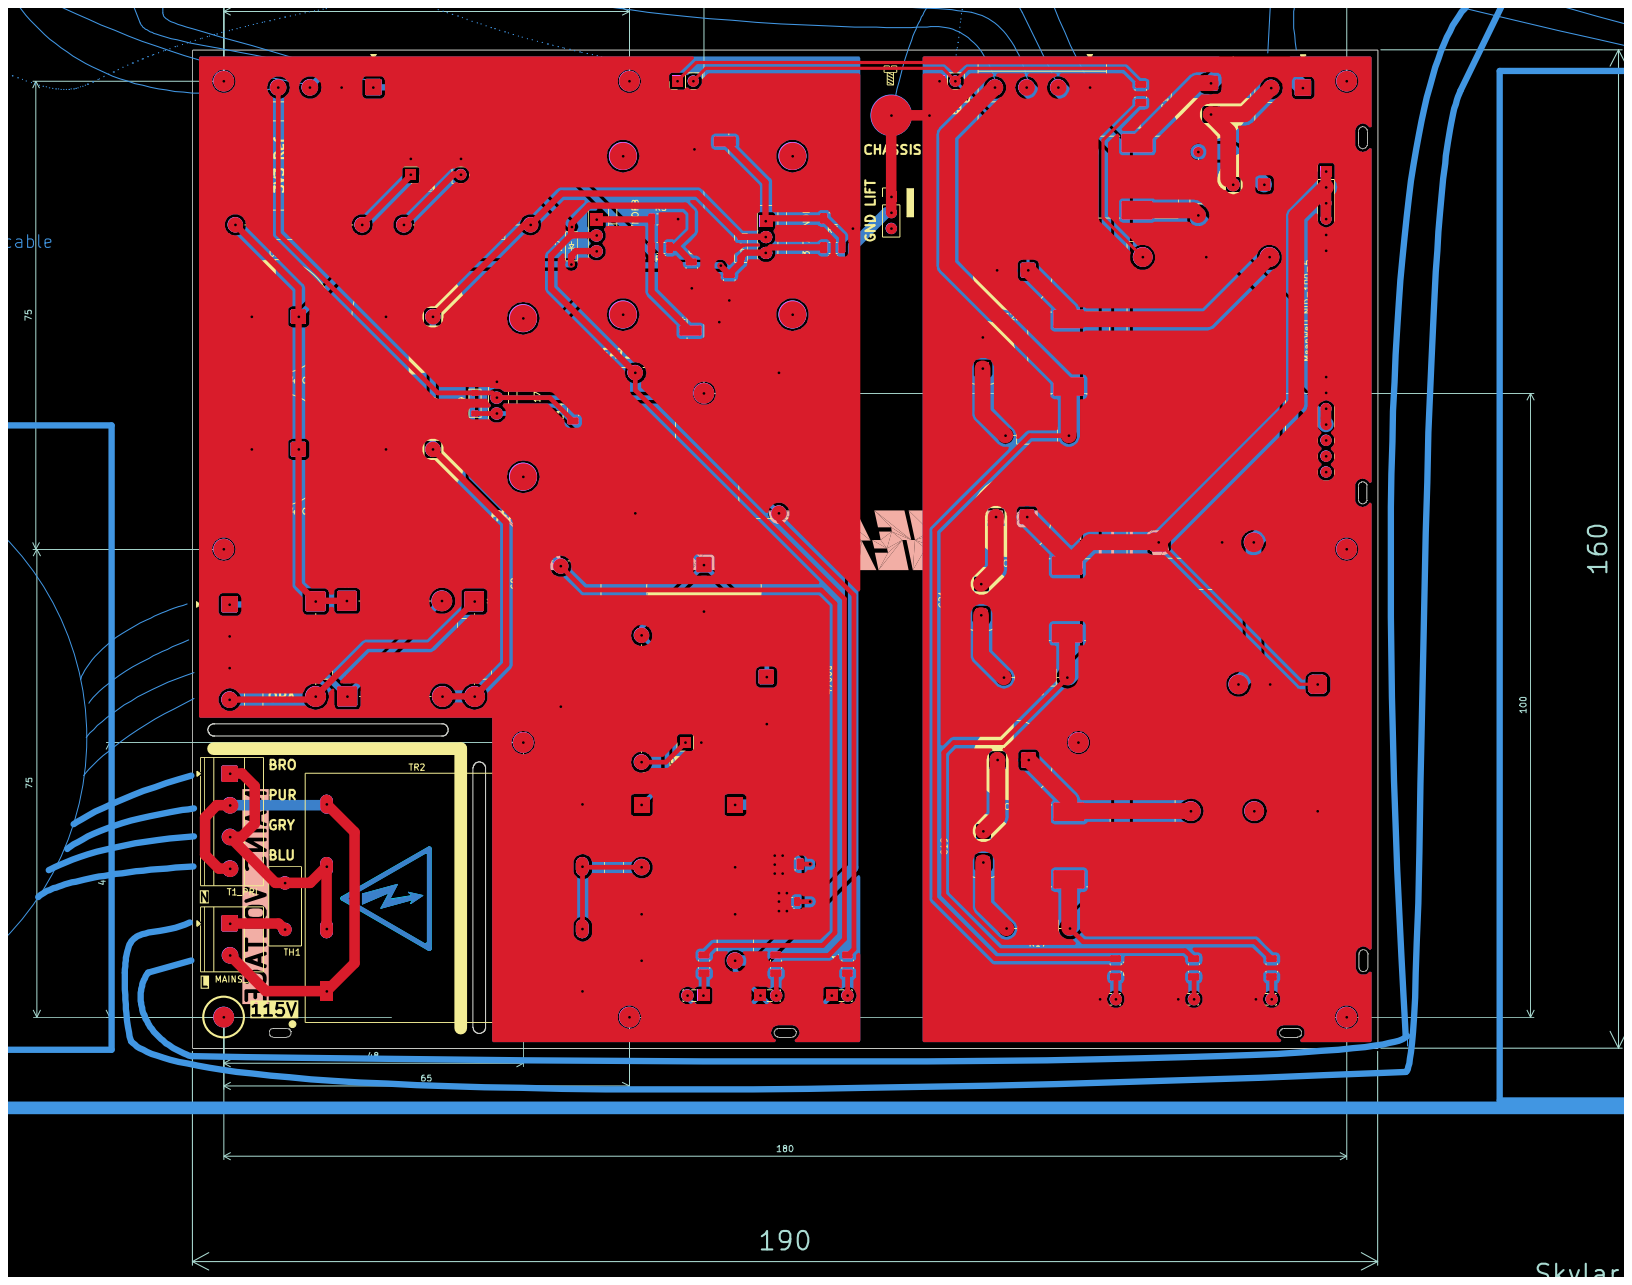
[picture p96: page 1]
