skylar-slideshows/Digilog_Capstone/PCB_CAD/led_ring/pcb_sheet_editor.pdf

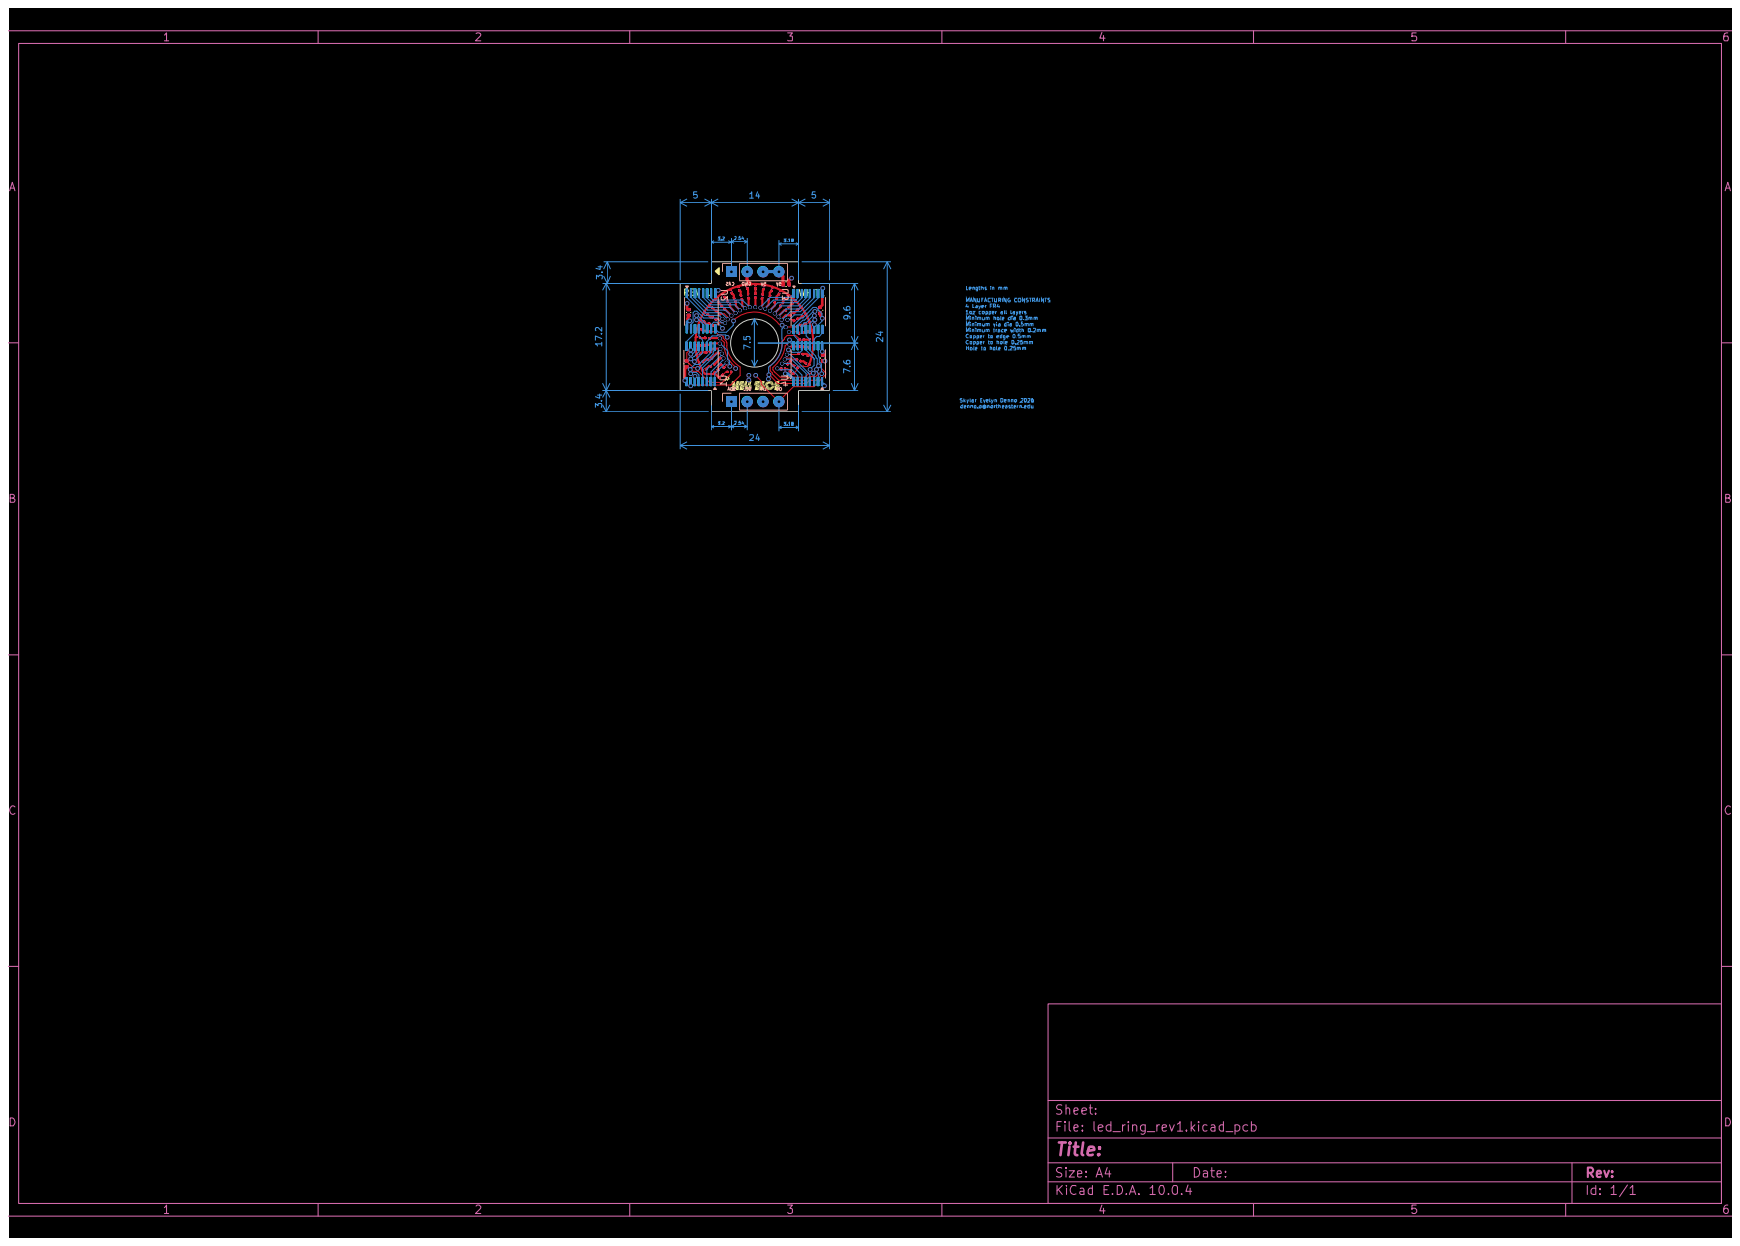
[picture p97: page 1]
