skylar-slideshows/Digilog_Capstone/Hardware_Documentation/HW_design_stuff/sim/2 Design - EQ/2 VCF/vcf.asc

C1: cap; 3.2n
C2: cap; 3.2n
R1: res; 100k
R2: res; 10k
R3: res; 10k
R4: res; 10k
R5: res; 10k
R5_divider: res; 100
R6: res; 10k
R6_divider: res; 100
R7: res; 100k
R8: res; 10k
R9: res; 1
R10: res; 1
R11: res; 20k
U1: opamp2; NE5532
U2: opamp2; NE5532
U3: opamp2; NE5532
U4: opamp2; NE5532
U5: LM13700
U6: LM13700
V1: voltage; 15
Vcc: voltage; 18
Vee: voltage; -18
Vin: voltage; 0; AC 1 0
Named nets: 0, IN, HP, LP, BP
.include NE5532.sub
Summing
Integrator 1
Integrator 2
R1 = 1/k
R7 = Q
.ac dec 100 10 100k
In reality, add bias compensation resistors to In+
.include LM13700.sub
Freq control: Replace R5,R6 (integrator input resistors) with OTAs
small signal dac -> gain
