skylar-slideshows/Digilog_Capstone/Hardware_Documentation/HW_design_stuff/sim/2 Design - EQ/FINAL 4 BAND EQ/FINALSPICE.asc

C1: cap; 10n
C2: cap; 10n
C3: cap; 3.3n
C4: cap; 3.3n
OTA1_HMF: LM13700
OTA2_HMF: LM13700
OTA3_HMF: LM13700
OTA4_HMF: LM13700
R1: res; 100k
R2: res; 10k
R3: res; 0
R4: res; 10k
R5: res; 10k
R5_divider: res; 100
R6: res; 10k
R6_divider: res; 100
R7: res; 100
R8: res; 10k
R9: res; 1
R10: res; 1
R11: res; 20k
R12: res; 100k
R13: res; 10k
R14: res; 10k
R15: res
R16: res
R17: res
R18: res
R19: res; 13k
R20: res; 13k
R21: res; 30k
R22: res; 30k
U1: opamp2; NE5532
U1_HMF: opamp2; NE5532
U2: opamp2; NE5532
U2_HMF: opamp2; NE5532
U3: opamp2; NE5532
U3_HMF: opamp2; NE5532
U4: LM13700
U4_HMF: opamp2; NE5532
U5: LM13700
U6: LM13700
V1: voltage; {CV}
V2: voltage; 0
Vcc: voltage; 18
Vee: voltage; -18
Vin: voltage; 0; AC 1 0
Named nets: 0, IN, HP, LP, BP
.include NE5532.sub
Summing
Integrator 1
Integrator 2
R1 = 1/k
R7 = Q
.ac dec 100 10 24k
.include LM13700.sub
small signal dac -> gain
.step param CV -14 14 1
.include OPAx134.SUB
