skylar-slideshows/Digilog_Capstone/PCB_CAD/Development Boards/Controls Mini Test Board/ctrl_mini.kicad_pcb

## KiCad design PCB_CAD/Development Boards/Controls Mini Test Board/ctrl_mini.kicad_pcb (2026-09-11)

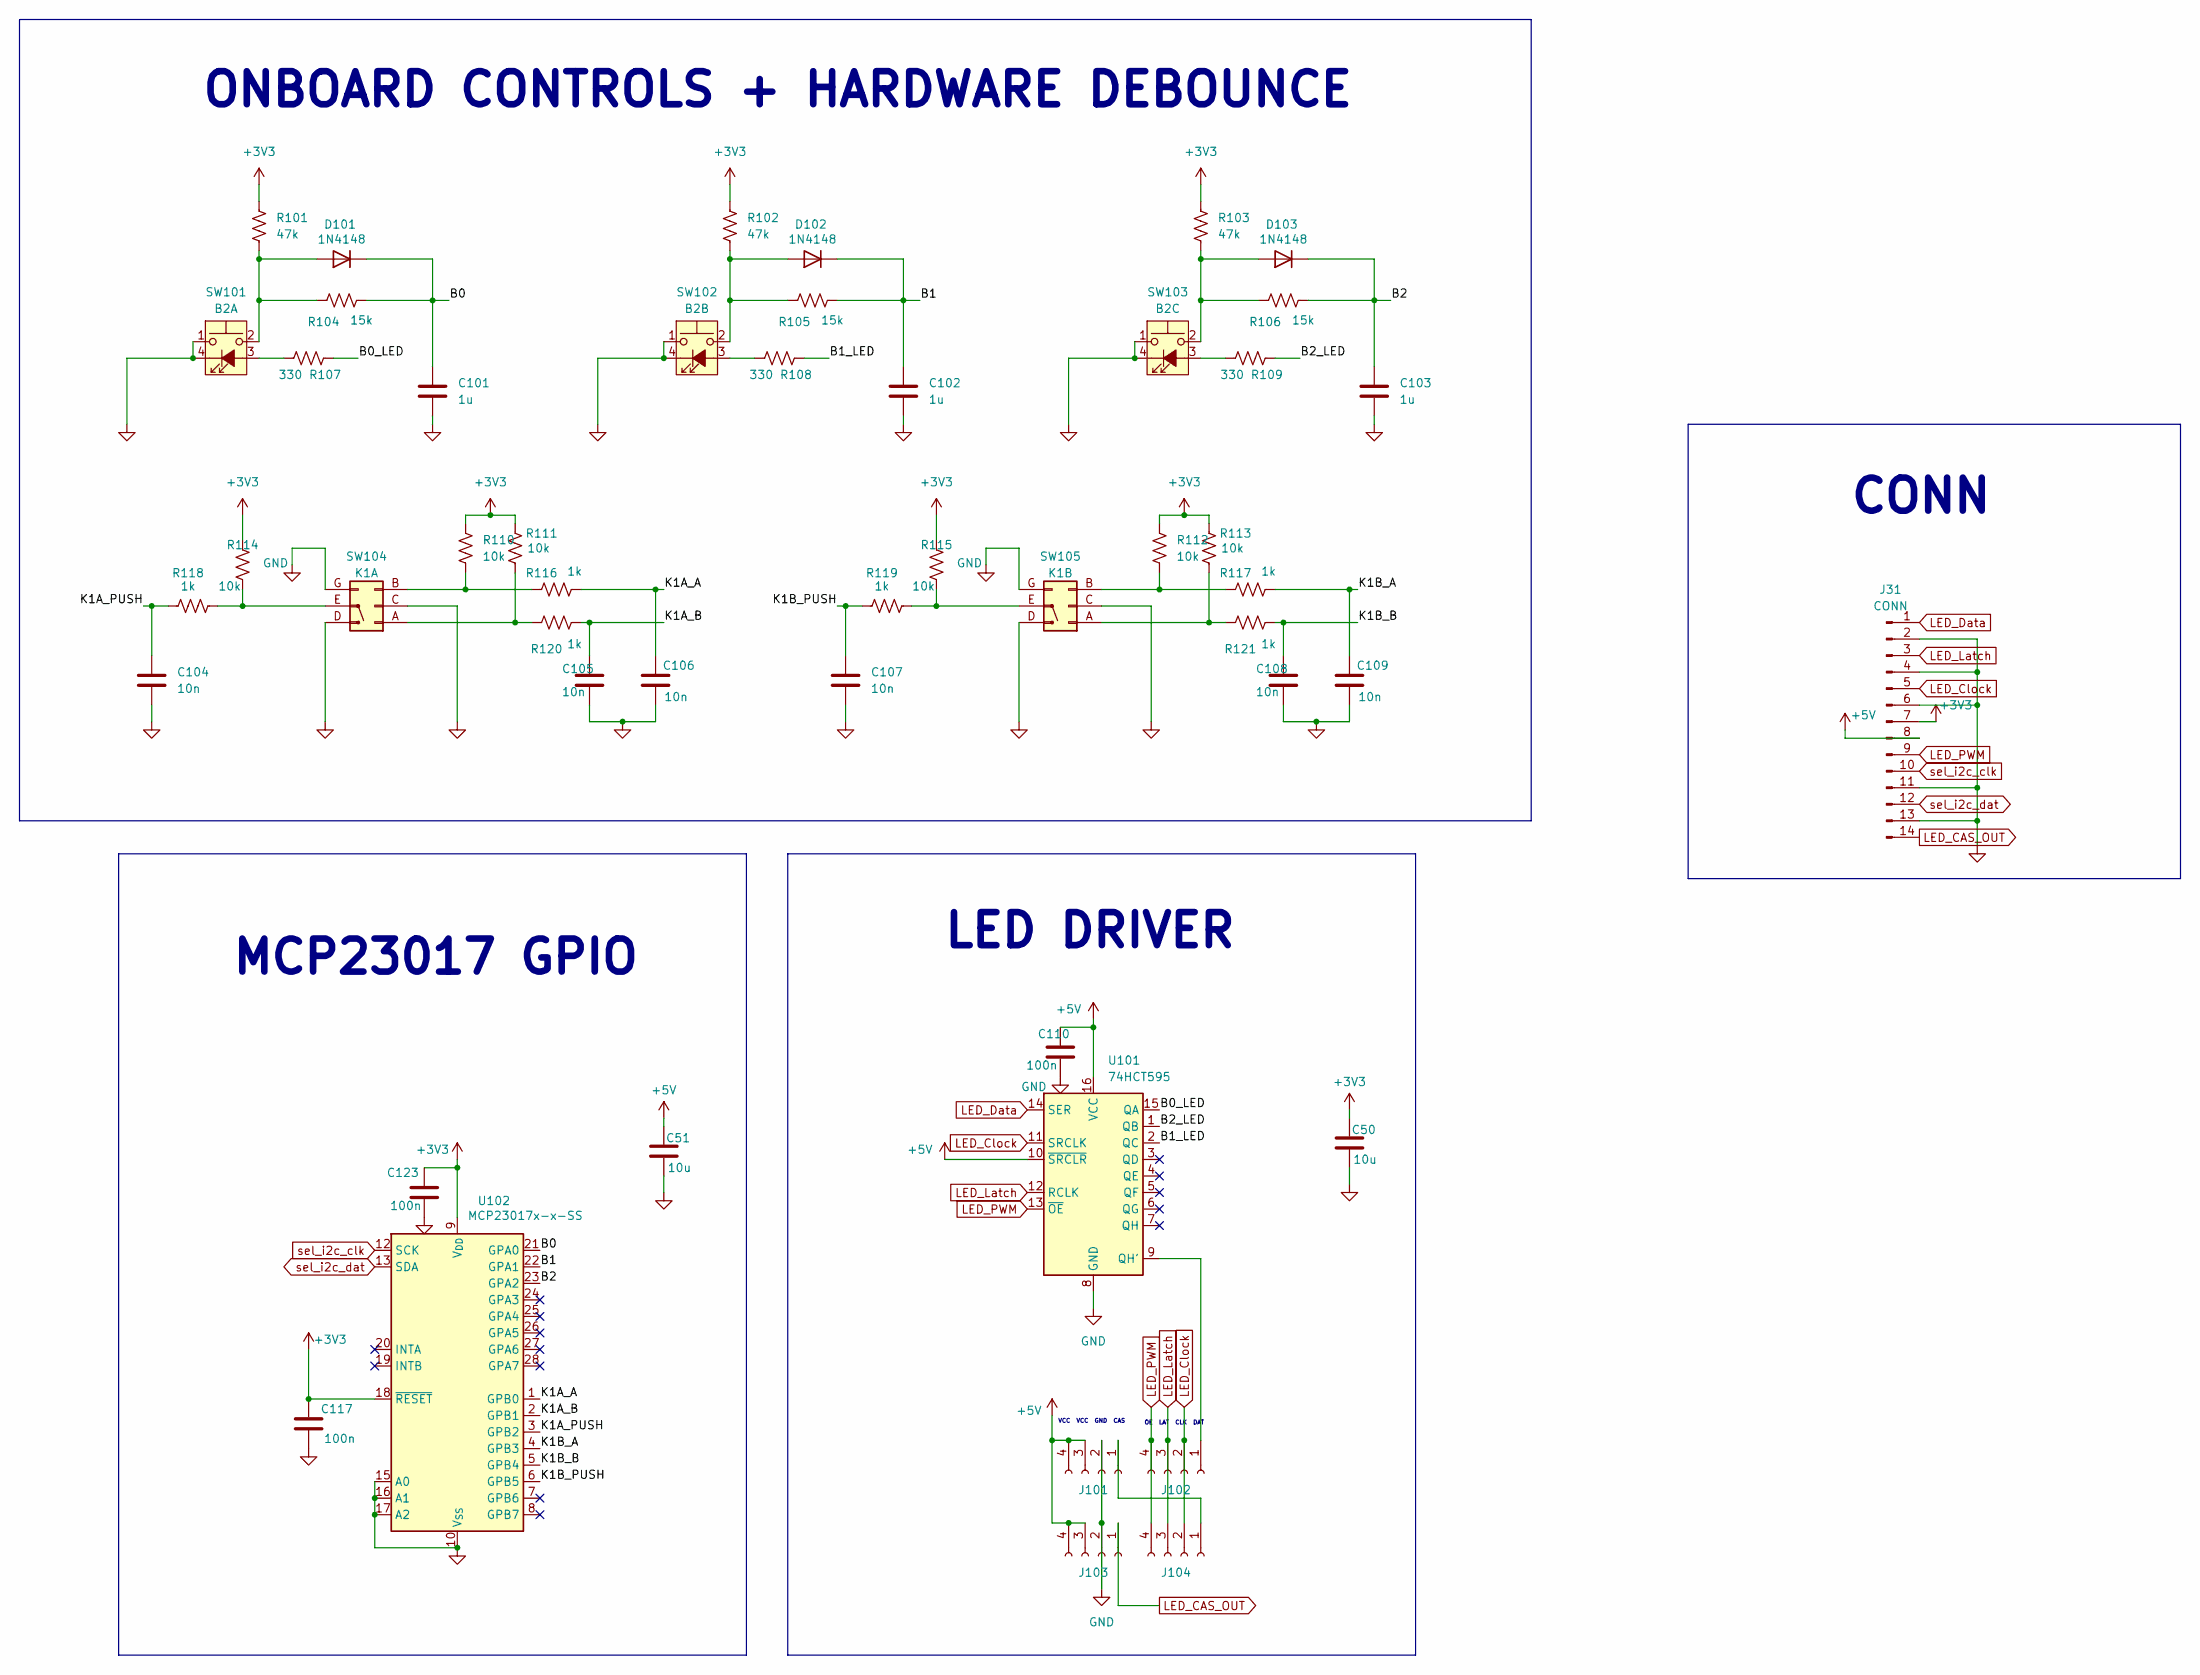
[picture p116: schematic ctrl_mini.kicad_sch, MINI CONTROLS BOARD]

Parts:
C50, C51: 10u; C_1206_3216Metric; LCSC C1849
C101, C102, C103: 1u; C_0603_1608Metric; LCSC C1592
C104, C105, C106, C107, C108, C109: 10n; C_0603_1608Metric; LCSC C57112
C110, C117, C123: 100n; C_0603_1608Metric; LCSC C1590
D101, D102, D103: 1N4148; D_SOD-323; LCSC C2128
J31: CONN; PinHeader_1x14_P2.54mm_Vertical
J101, J102, J103, J104: Conn_01x04_Socket; PinSocket_1x04_P2.54mm_Vertical
R101, R102, R103: 47k; R_0603_1608Metric; LCSC C25819
R104, R105, R106: 15k; R_0603_1608Metric; LCSC C22809
R107, R108, R109: 330; R_0603_1608Metric; LCSC C23138
R110, R111, R112, R113, R114, R115: 10k; R_0603_1608Metric; LCSC C25804
R116, R117, R118, R119, R120, R121: 1k; R_0603_1608Metric; LCSC C21190
SW101: B2A; CFPB-1CC-4W6
SW102: B2B; CFPB-1CC-4W6
SW103: B2C; CFPB-1CC-4W6
SW104: K1A; EC11J0924411
SW105: K1B; EC11J0924411
U101: 74HCT595; SOIC-16_3.9x9.9mm_P1.27mm; LCSC C282339
U102: MCP23017x-x-SS; SSOP-28_5.3x10.2mm_P0.65mm; LCSC C506653

Connections:
+3V3: C50.1, C117.1, C123.1, J31.7, R101.1, R102.1, R103.1, R110.1, R111.1, R112.1, R113.1, R114.1, R115.1, U102.9 (V_{DD}), U102.18 (~RESET)
+5V: C51.1, C110.1, J31.8, J101.3, J101.4, J103.3, J103.4, U101.10 (~SRCLR), U101.16 (VCC)
/B0: C101.1, D101.1 (K), R104.2, U102.21 (GPA0)
/B0_LED: R107.2, U101.15 (QA)
/B1: C102.1, D102.1 (K), R105.2, U102.22 (GPA1)
/B1_LED: R108.2, U101.2 (QC)
/B2: C103.1, D103.1 (K), R106.2, U102.23 (GPA2)
/B2_LED: R109.2, U101.1 (QB)
/K1A_A: C106.1, R116.2, U102.1 (GPB0)
/K1A_B: C105.1, R120.2, U102.2 (GPB1)
/K1A_PUSH: C104.1, R118.1, U102.3 (GPB2)
/K1B_A: C109.1, R117.2, U102.4 (GPB3)
/K1B_B: C108.1, R121.2, U102.5 (GPB4)
/K1B_PUSH: C107.1, R119.1, U102.6 (GPB5)
GND: C50.2, C51.2, C101.2, C102.2, C103.2, C104.2, C105.2, C106.2, C107.2, C108.2, C109.2, C110.2, C117.2, C123.2, J31.2, J31.4, J31.6, J31.11, J31.13, J101.2, J103.2, SW101.1, SW101.4 (K), SW102.1, SW102.4 (K), SW103.1, SW103.4 (K), SW104.C (Pin_2), SW104.D (Pin_4), SW104.G (Pin_6), SW105.C (Pin_2), SW105.D (Pin_4), SW105.G (Pin_6), U101.8 (GND), U102.10 (V_{SS}), U102.15 (A0), U102.16 (A1), U102.17 (A2)
LED_CAS_OUT: J31.14, J103.1
LED_Clock: J31.5, J102.2, J104.2, U101.11 (SRCLK)
LED_Data: J31.1, U101.14 (SER)
LED_Latch: J31.3, J102.3, J104.3, U101.12 (RCLK)
LED_PWM: J31.9, J102.4, J104.4, U101.13 (~OE)
unnamed: D101.2 (A), R101.2, R104.1, SW101.2
unnamed: D102.2 (A), R102.2, R105.1, SW102.2
unnamed: D103.2 (A), R103.2, R106.1, SW103.2
unnamed: J101.1, J104.1
unnamed: J102.1, U101.9 (QH')
unnamed: R107.1, SW101.3 (A)
unnamed: R108.1, SW102.3 (A)
unnamed: R109.1, SW103.3 (A)
unnamed: R111.2, R120.1, SW104.A (Pin_1)
unnamed: R110.2, R116.1, SW104.B (Pin_3)
unnamed: R114.2, R118.2, SW104.E (Pin_5)
unnamed: R113.2, R121.1, SW105.A (Pin_1)
unnamed: R112.2, R117.1, SW105.B (Pin_3)
unnamed: R115.2, R119.2, SW105.E (Pin_5)
sel_i2c_clk: J31.10, U102.12 (SCK)
sel_i2c_dat: J31.12, U102.13 (SDA)

Notes on the sheet:
ONBOARD CONTROLS + HARDWARE DEBOUNCE
VCC VCC GND CAS
OE LAT CLK DAT
CONN
LED DRIVER
MCP23017 GPIO

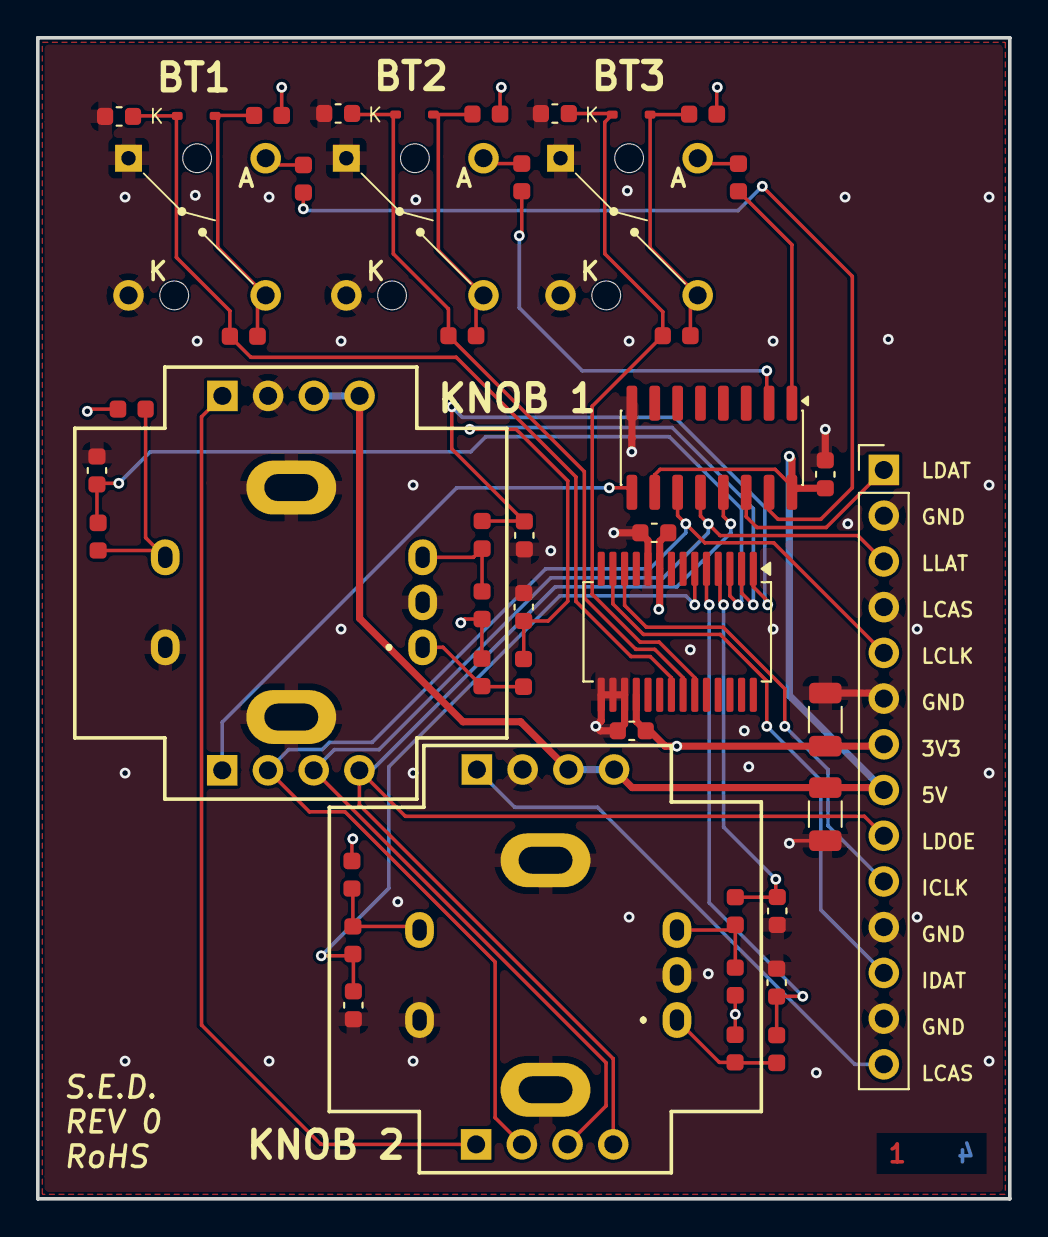
[picture p117: board ctrl_mini.kicad_pcb from above]

Board: 4 copper layers, 54.0 x 64.5 mm, 50 parts (0 on the bottom side), 36 nets.
