skylar-slideshows/Digilog_Capstone/PCB_CAD/PSU/PSU_KICAD/PSU.kicad_pcb

## KiCad design PCB_CAD/PSU/PSU_KICAD/PSU.kicad_pcb (2026-08-18)

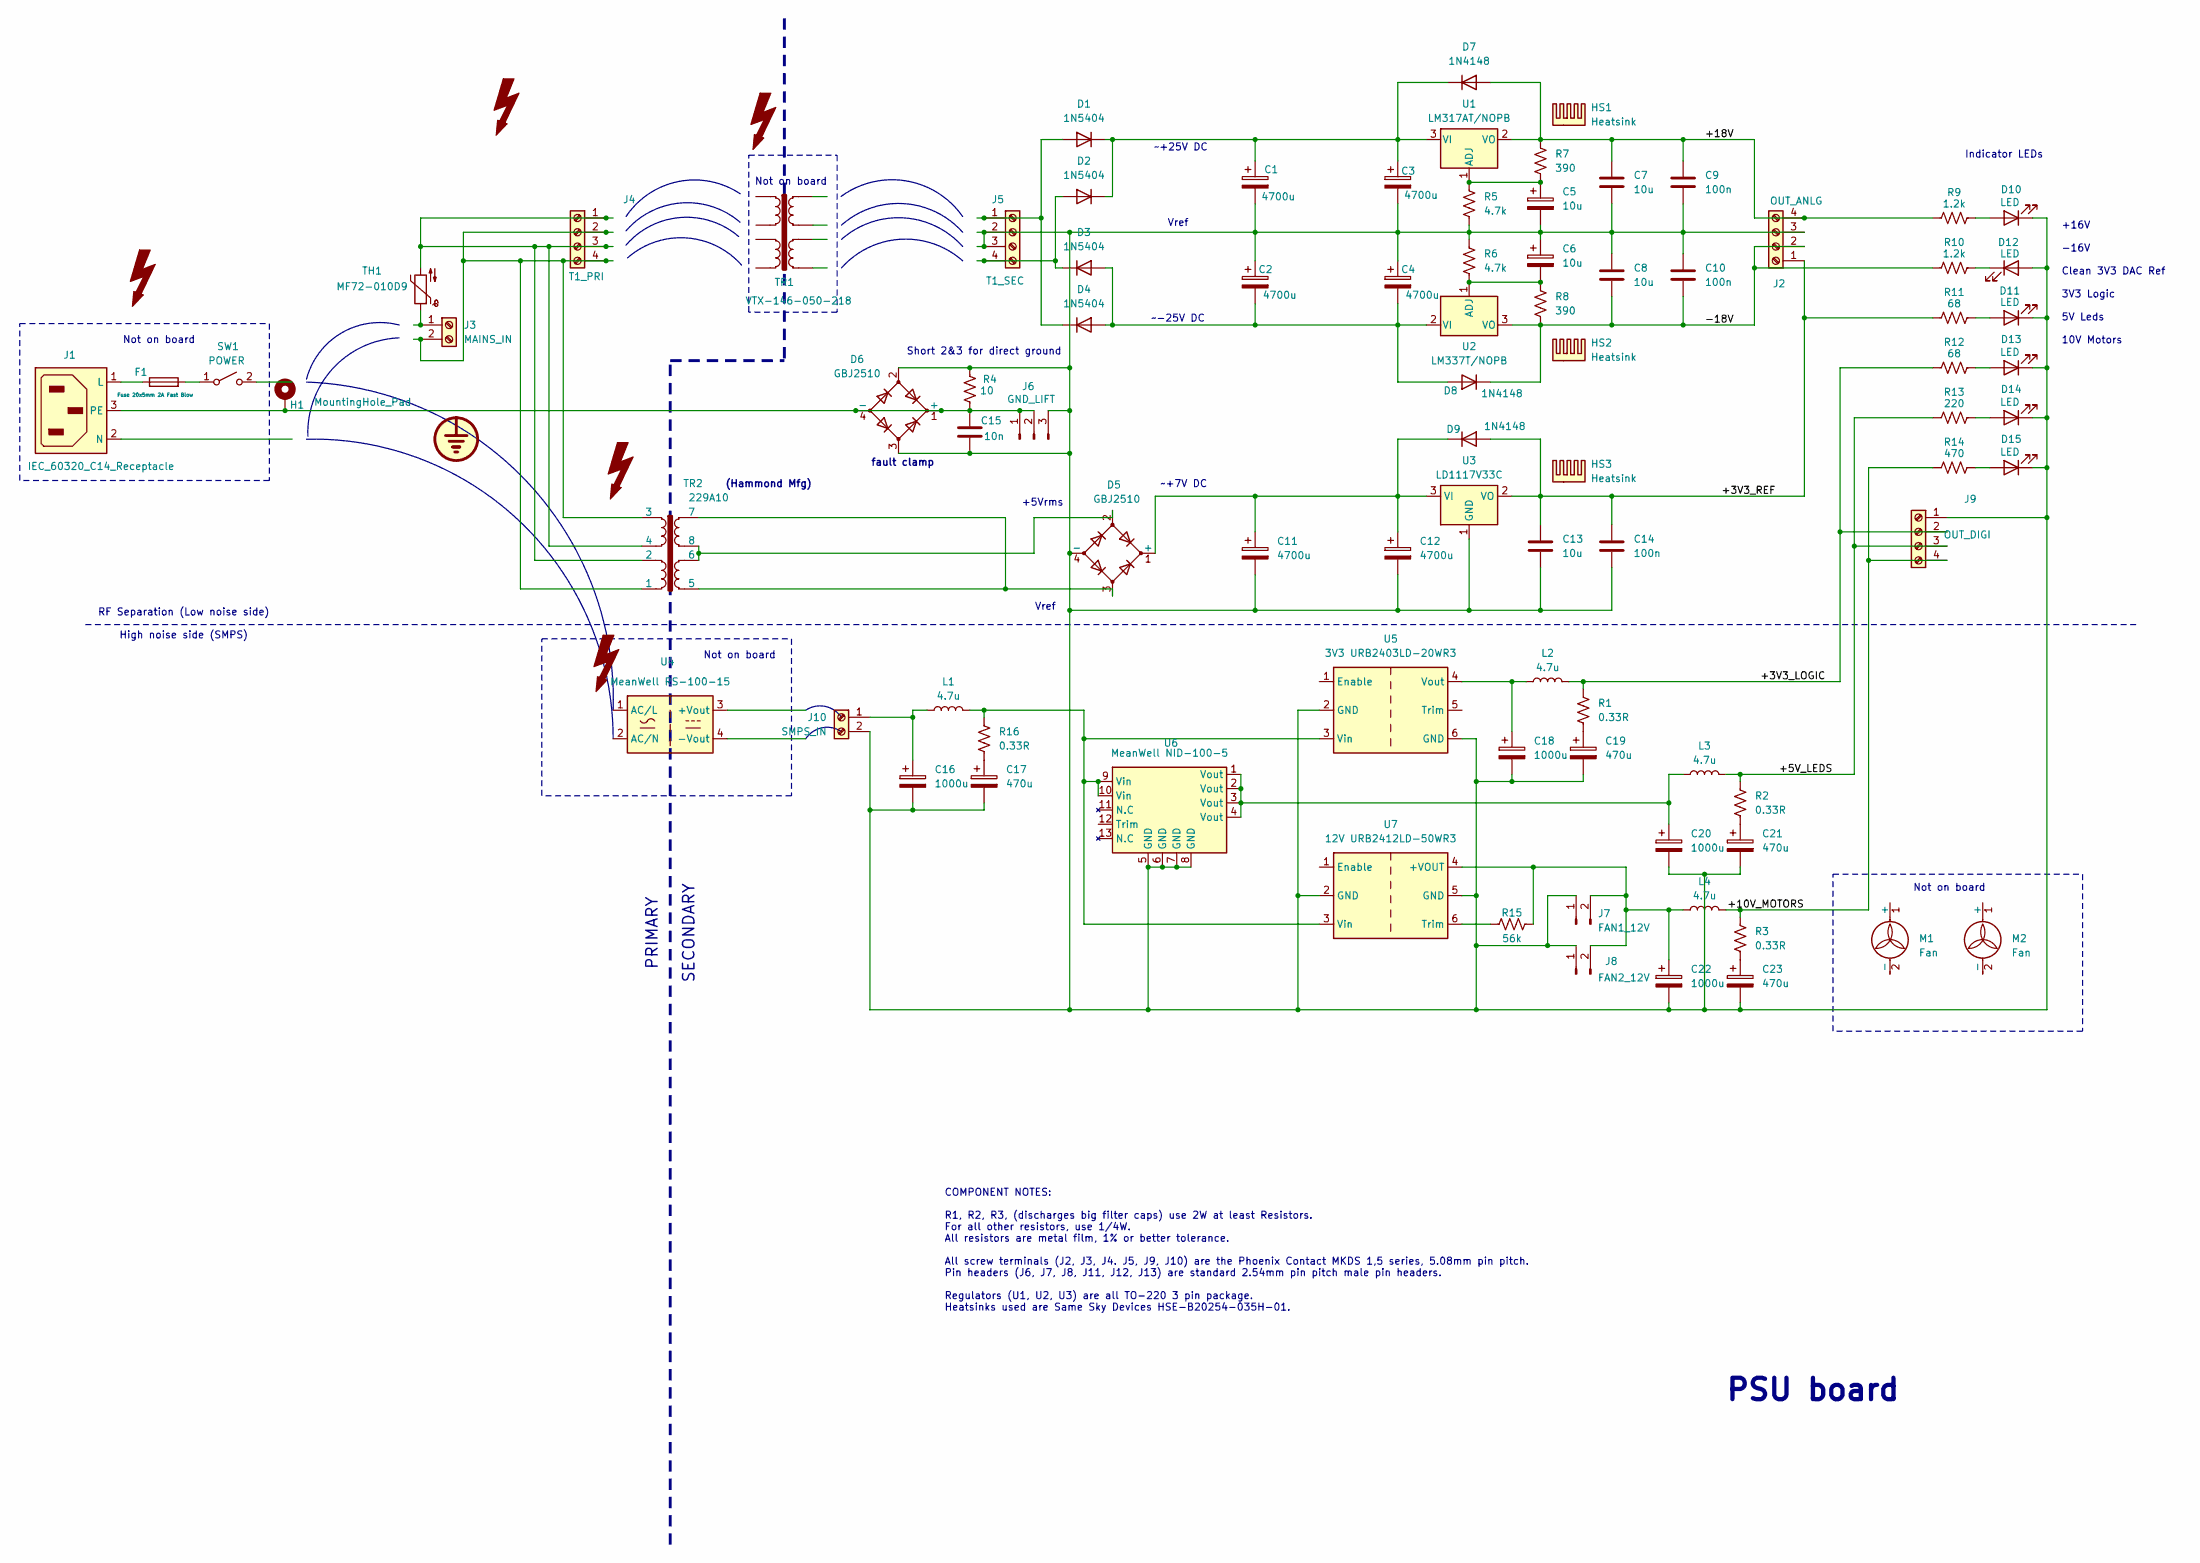
[picture p118: schematic PSU.kicad_sch, PSU board (+/-18V, 3V3 VREF, 3V3, 5V, 10V DC)]

Parts:
C1, C2, C3, C4, C11, C12: 4700u; CP_Radial_D18.0mm_P7.50mm; LCSC C443892
C5, C6: 10u; CP_Elec_6.3x5.4; LCSC C14162
C7, C8, C13: 10u; C_Rect_L24.0mm_W12.6mm_P22.50mm_MKT; LCSC C328801
C9, C10, C14: 100n; C_1206_3216Metric; LCSC C1945
C15: 10n; C_1206_3216Metric; LCSC C55077
C16, C18, C20, C22: 1000u; CP_Radial_D12.5mm_P5.00mm; LCSC C122661
C17, C19, C21, C23: 470u; CP_Radial_D10.0mm_P5.00mm; LCSC C116237
D1, D2, D3, D4: 1N5404; D_DO-201AD_P15.24mm_Horizontal; LCSC C222547
D5, D6: GBJ2510; Diode_Bridge_32.0x5.6x17.0mm_P10.0mm_P7.5mm; LCSC C27523
D7, D8, D9: 1N4148; D_SOD-123; LCSC C2099
D10, D11, D12, D13, D14, D15: LED; LED_Rectangular_W3.9mm_H1.8mm
F1: Fuse 20x5mm 2A Fast Blow
H1: MountingHole_Pad; MountingHole_3.2mm_M3_Pad_TopBottom
HS1, HS2, HS3: Heatsink; HSINK_HSE-B20380-040H
J1: IEC_60320_C14_Receptacle
J2: OUT_ANLG; TerminalBlock_Phoenix_MKDS-1,5-4-5.08_1x04_P5.08mm_Horizont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; LCSC C5443561
J3: MAINS_IN; TerminalBlock_Phoenix_MKDS-1,5-2-5.08_1x02_P5.08mm_Horizont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; LCSC C5443539
J4: T1_PRI; TerminalBlock_Phoenix_MKDS-1,5-4-5.08_1x04_P5.08mm_Horizont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; LCSC C5443561
J5: T1_SEC; TerminalBlock_Phoenix_MKDS-1,5-4-5.08_1x04_P5.08mm_Horizont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; LCSC C5443561
J6: GND_LIFT; PinHeader_1x03_P2.54mm_Vertical; LCSC C5360899
J7: FAN1_12V; PinHeader_1x02_P2.54mm_Vertical; LCSC C5360898
J8: FAN2_12V; PinHeader_1x02_P2.54mm_Vertical; LCSC C5360898
J9: OUT_DIGI; TerminalBlock_Phoenix_MKDS-1,5-4-5.08_1x04_P5.08mm_Horizont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; LCSC C5443561
J10: SMPS_IN; TerminalBlock_Phoenix_MKDS-1,5-2-5.08_1x02_P5.08mm_Horizont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; LCSC C5443539
L1, L2, L3, L4: 4.7u; L_Vishay_IHLP-5050; LCSC C845092
M1, M2: Fan
R1, R2, R3, R16: 0.33R; R_Axial_DIN0207_L6.3mm_D2.5mm_P10.16mm_Horizontal; LCSC C119970
R4: 10; R_0805_2012Metric; LCSC C340448
R5, R6: 4.7k; R_1206_3216Metric; LCSC C702850
R7, R8: 390; R_1206_3216Metric; LCSC C497314
R9, R10: 1.2k; R_1206_3216Metric; LCSC C17891
R11, R12: 68; R_1206_3216Metric; LCSC C294793
R13: 220; R_1206_3216Metric; LCSC C25363
R14: 470; R_1206_3216Metric; LCSC C25383
R15: 56k; R_1206_3216Metric; LCSC C4513
SW1: POWER
TH1: MF72-010D9; C_Disc_D12.5mm_W5.0mm_P7.50mm
TR1: VTX-146-050-218
TR2: 229A10
U1: LM317AT/NOPB; TO-220-3_Vertical; LCSC C94659
U2: LM337T/NOPB; TO-220-3_Vertical; LCSC C2869423
U3: LD1117V33C; TO-220-3_Vertical; LCSC C672117
U4: MeanWell RS-100-15
U5: 3V3 URB2403LD-20WR3; Converter_DCDC_XP_POWER_JTDxxxxxxx_THT
U6: MeanWell NID-100-5; MeanWell NID100
U7: 12V URB2412LD-50WR3; urb 50w dc-dc

Connections:
/+3V3_LOGIC: J9.2, L2.2, R1.1, R12.1
/+3V3_REF: C13.1, C14.1, D9.2 (A), J2.1, R11.1, U3.2 (VO)
/+5V_LEDS: J9.3, L3.2, R2.1, R13.1
/+10V_MOTORS: J9.4, L4.2, R3.1, R14.1
/+18V: C7.1, C9.1, D7.2 (A), J2.4, R7.1, R9.1, U1.2 (VO)
/-18V: C8.2, C10.2, D8.1 (K), J2.2, R8.2, R10.1, U2.3 (VO)
unnamed: C17.1, R16.2
unnamed: C19.1, R1.2
unnamed: C20.1, L3.1, U6.1 (Vout), U6.2 (Vout), U6.3 (Vout), U6.4 (Vout)
unnamed: C21.1, R2.2
unnamed: C23.1, R3.2
unnamed: D1.2 (A), D4.1 (K), J5.1
unnamed: C1.1, C3.1, D1.1 (K), D2.1 (K), D7.1 (K), U1.3 (VI)
unnamed: D2.2 (A), D3.1 (K), J5.4
unnamed: C2.2, C4.2, D3.2 (A), D4.2 (A), D8.2 (A), U2.2 (VI)
unnamed: C11.1, C12.1, D5.1 (+), D9.1 (K), U3.3 (VI)
unnamed: D5.2, TR2.6, TR2.8
unnamed: D5.3, TR2.5, TR2.7
unnamed: C15.2, D6.1 (+), D6.4 (-), H1.1 (1_1), J1.3 (PE), J6.1, J6.2, R4.1
unnamed: D10.2 (A), R9.2
unnamed: C1.2, C2.1, C3.2, C4.1, C5.2, C6.1, C7.2, C8.1, C9.2, C10.1, C11.2, C12.2, C13.2, C14.2, C15.1, C16.2, C17.2, C18.2, C19.2, C20.2, C21.2, C22.2, C23.2, D5.4 (-), D6.2, D6.3, D10.1 (K), D11.2 (A), D12.1 (K), D13.1 (K), D14.1 (K), D15.1 (K), J2.3, J5.2, J5.3, J6.3, J7.1, J8.1, J9.1, J10.2, R4.2, R5.2, R6.1, U3.1 (GND), U5.2 (GND), U5.6 (GND), U6.5 (GND), U6.6 (GND), U6.7 (GND), U6.8 (GND), U7.2 (GND), U7.5 (GND)
unnamed: D11.1 (K), R10.2
unnamed: D12.2 (A), R11.2
unnamed: D13.2 (A), R12.2
unnamed: D14.2 (A), R13.2
unnamed: D15.2 (A), R14.2
unnamed: F1.1, J1.1 (L)
unnamed: F1.2, SW1.1 (A)
unnamed: J3.1, TH1.1
unnamed: J3.2, J4.2, J4.4, TR2.1, TR2.3
unnamed: J4.1, J4.3, TH1.2, TR2.2, TR2.4
unnamed: C22.1, J7.2, J8.2, L4.1, R15.2, U7.4 (+VOUT)
unnamed: C16.1, J10.1, L1.1
unnamed: C5.1, R5.1, R7.2, U1.1 (ADJ)
unnamed: C6.2, R6.2, R8.1, U2.1 (ADJ)
unnamed: L1.2, R16.1, U5.3 (Vin), U6.9 (Vin), U6.10 (Vin), U7.3 (Vin)
unnamed: C18.1, L2.1, U5.4 (Vout)
unnamed: R15.1, U7.6 (Trim)

Notes on the sheet:
Indicator LEDs
COMPONENT NOTES: R1, R2, R3, (discharges big filter caps) use 2W at least Resistors. For all other resistors, use 1/4W. All resistors are metal film, 1% or better tolerance. All screw terminals (J2, J3, J4. J5, J9, J10) are the Phoenix Contact MKDS 1,5 series, 5.08mm pin pitch. Pin headers (J6, J7,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
Vref
fault clamp
Short 2&3 for direct ground
+5Vrms
~-25V DC
Not on board
~+7V DC
~+25V DC
+16V -16V Clean 3V3 DAC Ref 3V3 Logic 5V Leds 10V Motors
PSU board
(Hammond Mfg)
PRIMARY SECONDARY
RF Separation (Low noise side) High noise side (SMPS)

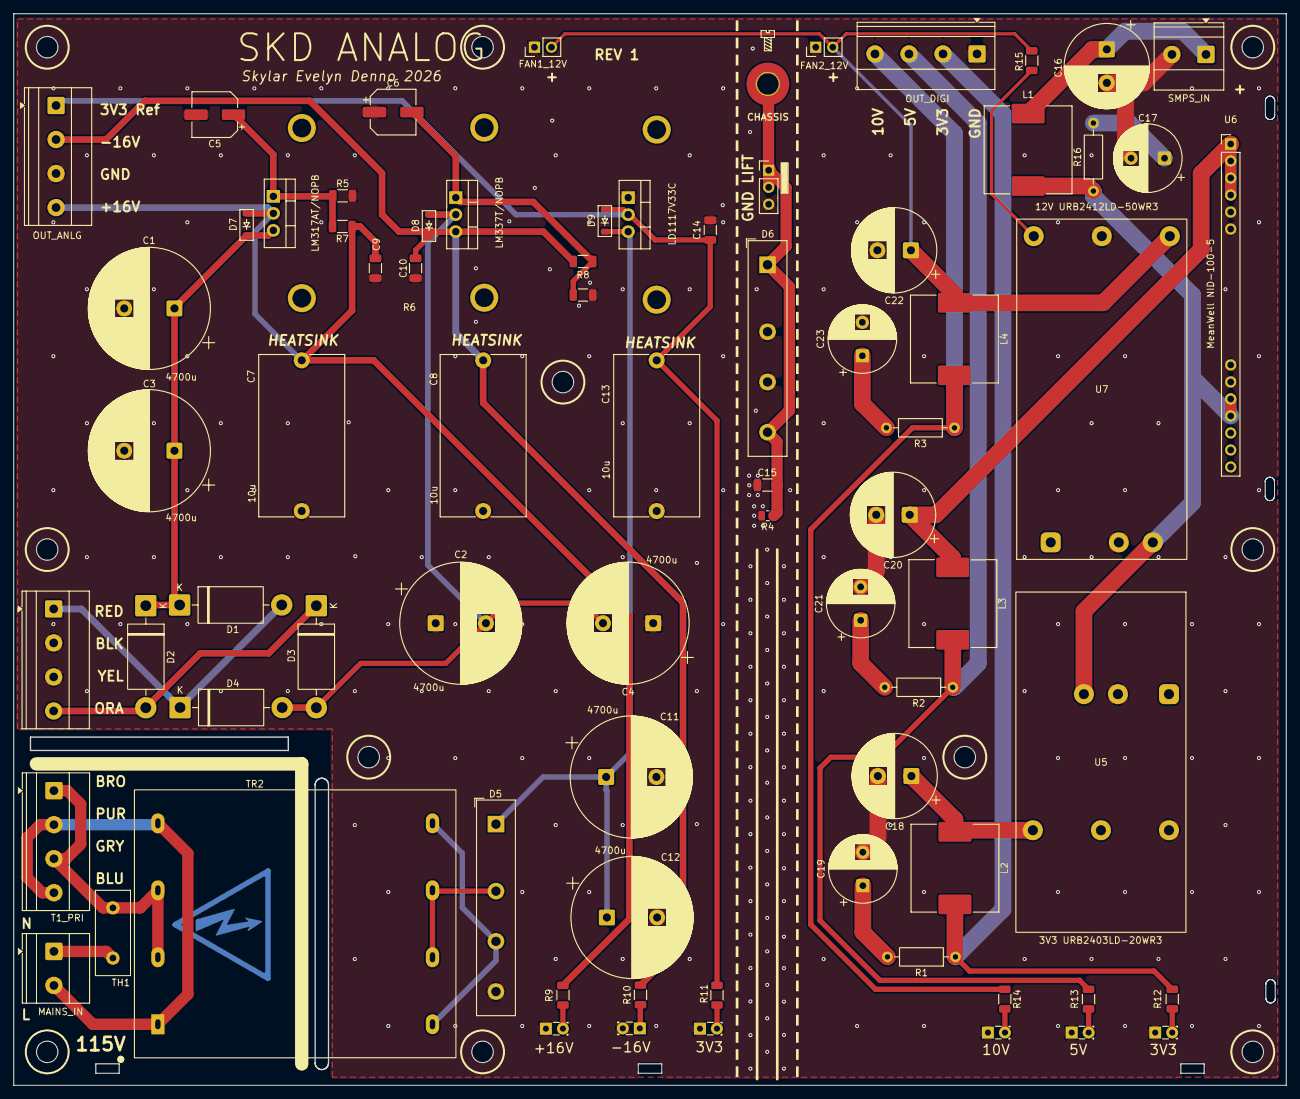
[picture p119: board PSU.kicad_pcb from above]

Board: 4 copper layers, 190.0 x 160.0 mm, 79 parts (0 on the bottom side), 36 nets.
