skylar-slideshows/Digilog_Capstone/PCB_CAD/Development Boards/_DEV_EC11_button_breakout/_restore_backup_2026-08-24T17-16-47-379/EC11BREAKOUT.kicad_pcb

## KiCad design PCB_CAD/Development Boards/_DEV_EC11_button_breakout/_restore_backup_2026-08-24T17-16-47-379/EC11BREAKOUT.kicad_pcb (2026-08-05)

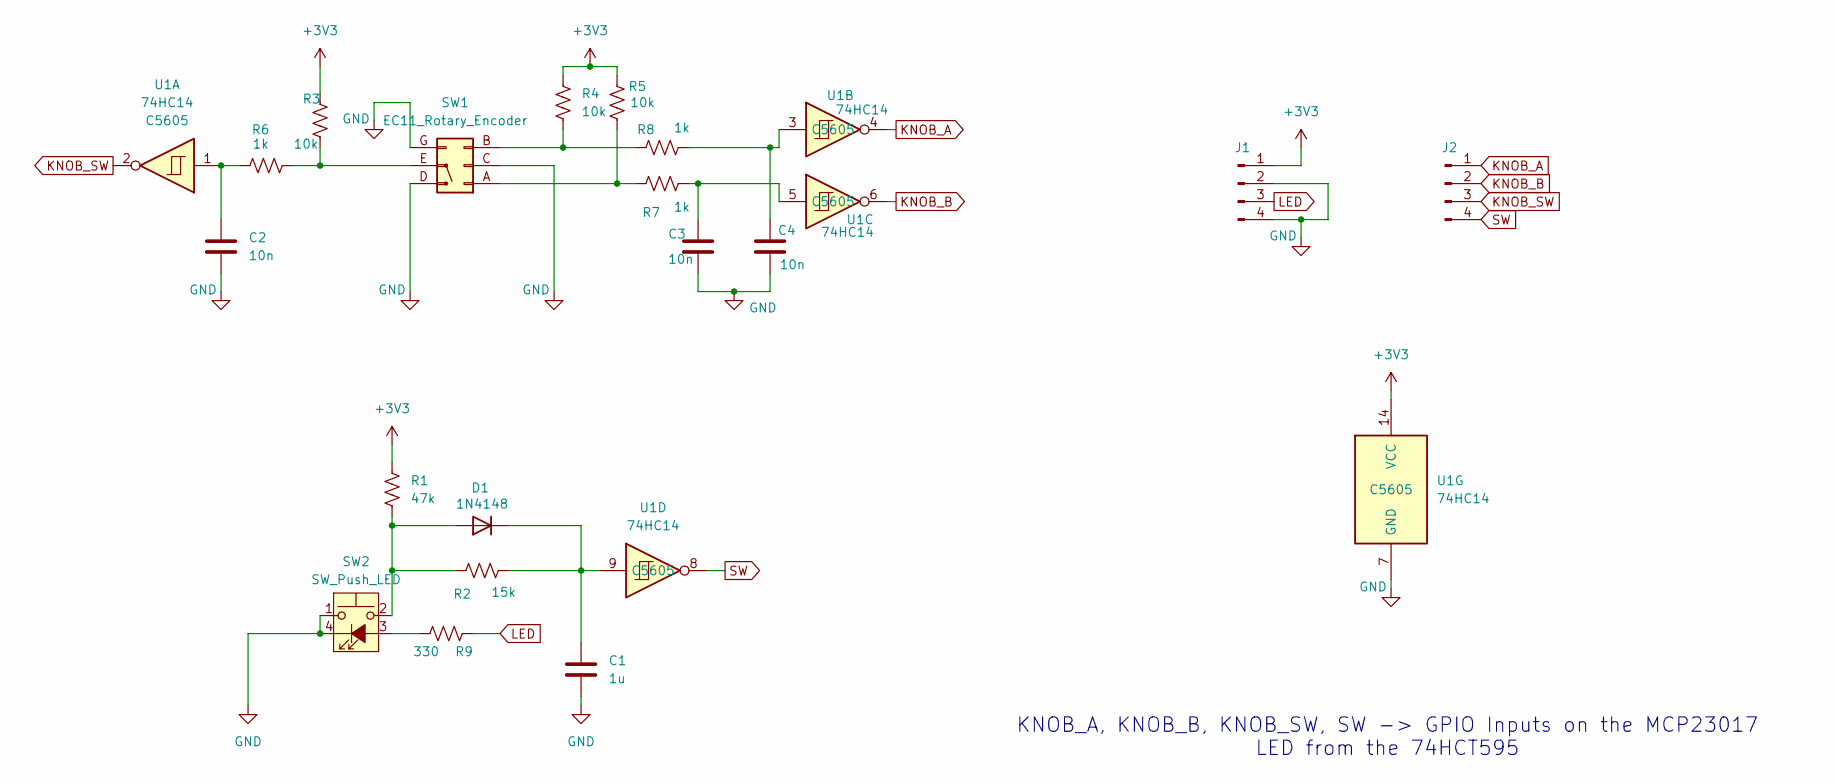
[picture p120: schematic EC11BREAKOUT.kicad_sch, EC11 and pushbutton hardware debounce]

Parts:
C1: 1u; C_0603_1608Metric; LCSC C15849
C2, C3, C4: 10n; C_0603_1608Metric; LCSC C57112
D1: 1N4148; D_SOD-323; LCSC C2128
J1, J2: Conn_01x04_Pin; PinHeader_1x04_P2.54mm_Vertical; LCSC dnp
R1: 47k; R_0603_1608Metric; LCSC C25819
R2: 15k; R_0603_1608Metric; LCSC C22809
R3, R4, R5: 10k; R_0603_1608Metric; LCSC C25804
R6, R7, R8: 1k; R_0603_1608Metric; LCSC C21190
R9: 330; R_0603_1608Metric; LCSC C23138
SW1: EC11_Rotary_Encoder; EC11J0924411; LCSC dnp
SW2: SW_Push_LED; CFPB-1CC-4W6; LCSC dnp
U1: 74HC14; SOIC-14_3.9x8.7mm_P1.27mm; LCSC C5605

Connections:
+3V3: J1.1, R1.1, R3.1, R4.1, R5.1, U1.14 (VCC)
GND: C1.2, C2.2, C3.2, C4.2, J1.2, J1.4, SW1.C (Pin_2), SW1.D (Pin_4), SW1.G (Pin_6), SW2.1, SW2.4 (K), U1.7 (GND)
KNOB_A: J2.1, U1.4
KNOB_B: J2.2, U1.6
KNOB_SW: J2.3, U1.2
LED: J1.3, R9.2
unnamed: C2.1, R6.1, U1.1
unnamed: C3.1, R7.2, U1.5
unnamed: C4.1, R8.2, U1.3
unnamed: D1.2 (A), R1.2, R2.1, SW2.2
unnamed: C1.1, D1.1 (K), R2.2, U1.9
unnamed: R5.2, R7.1, SW1.A (Pin_1)
unnamed: R4.2, R8.1, SW1.B (Pin_3)
unnamed: R3.2, R6.2, SW1.E (Pin_5)
unnamed: R9.1, SW2.3 (A)
SW: J2.4, U1.8

Notes on the sheet:
KNOB_A, KNOB_B, KNOB_SW, SW -> GPIO Inputs on the MCP23017 LED from the 74HCT595

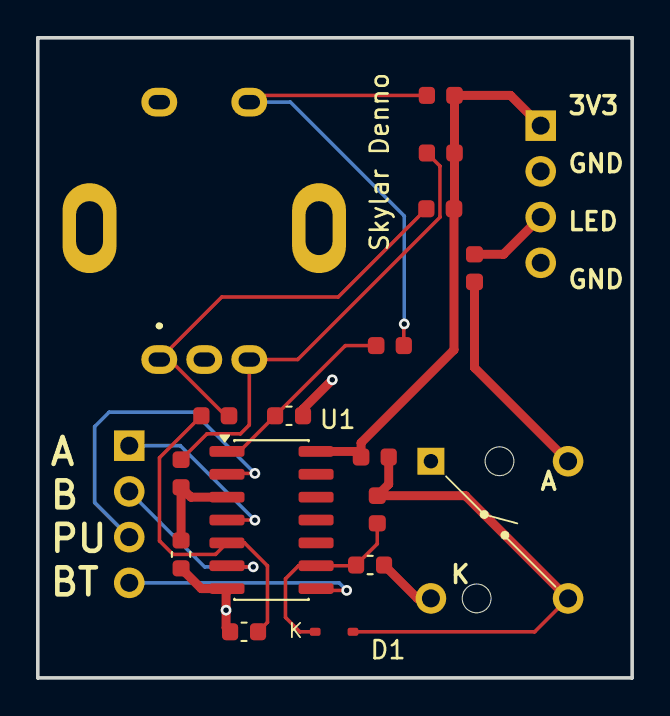
[picture p121: board EC11BREAKOUT.kicad_pcb from above]

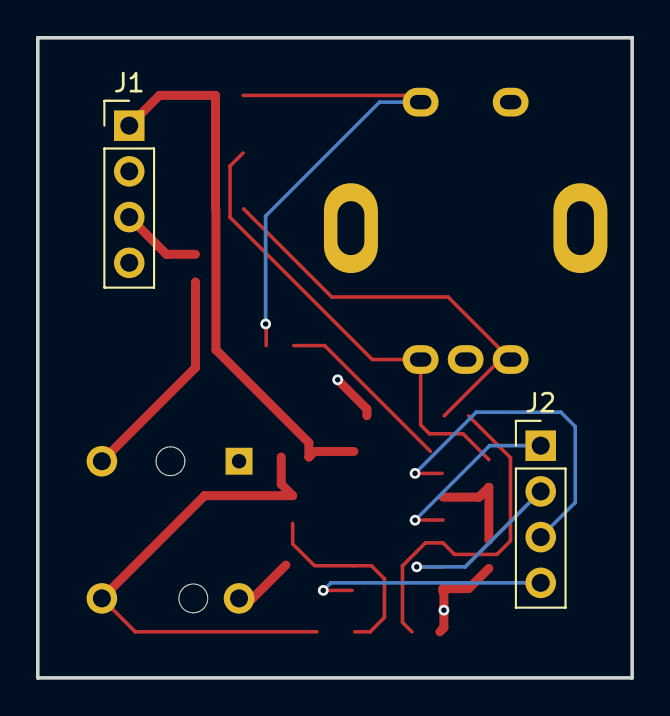
[picture p122: board EC11BREAKOUT.kicad_pcb from below]

Board: 4 copper layers, 33.0 x 35.6 mm, 19 parts (2 on the bottom side), 16 nets.
