skylar-slideshows/Digilog_Capstone/Hardware_Documentation/HW_design_stuff/ch_output_design/ch_output_design.kicad_sch

## KiCad design Hardware_Documentation/HW_design_stuff/ch_output_design/ch_output_design.kicad_sch (2026-08-28)

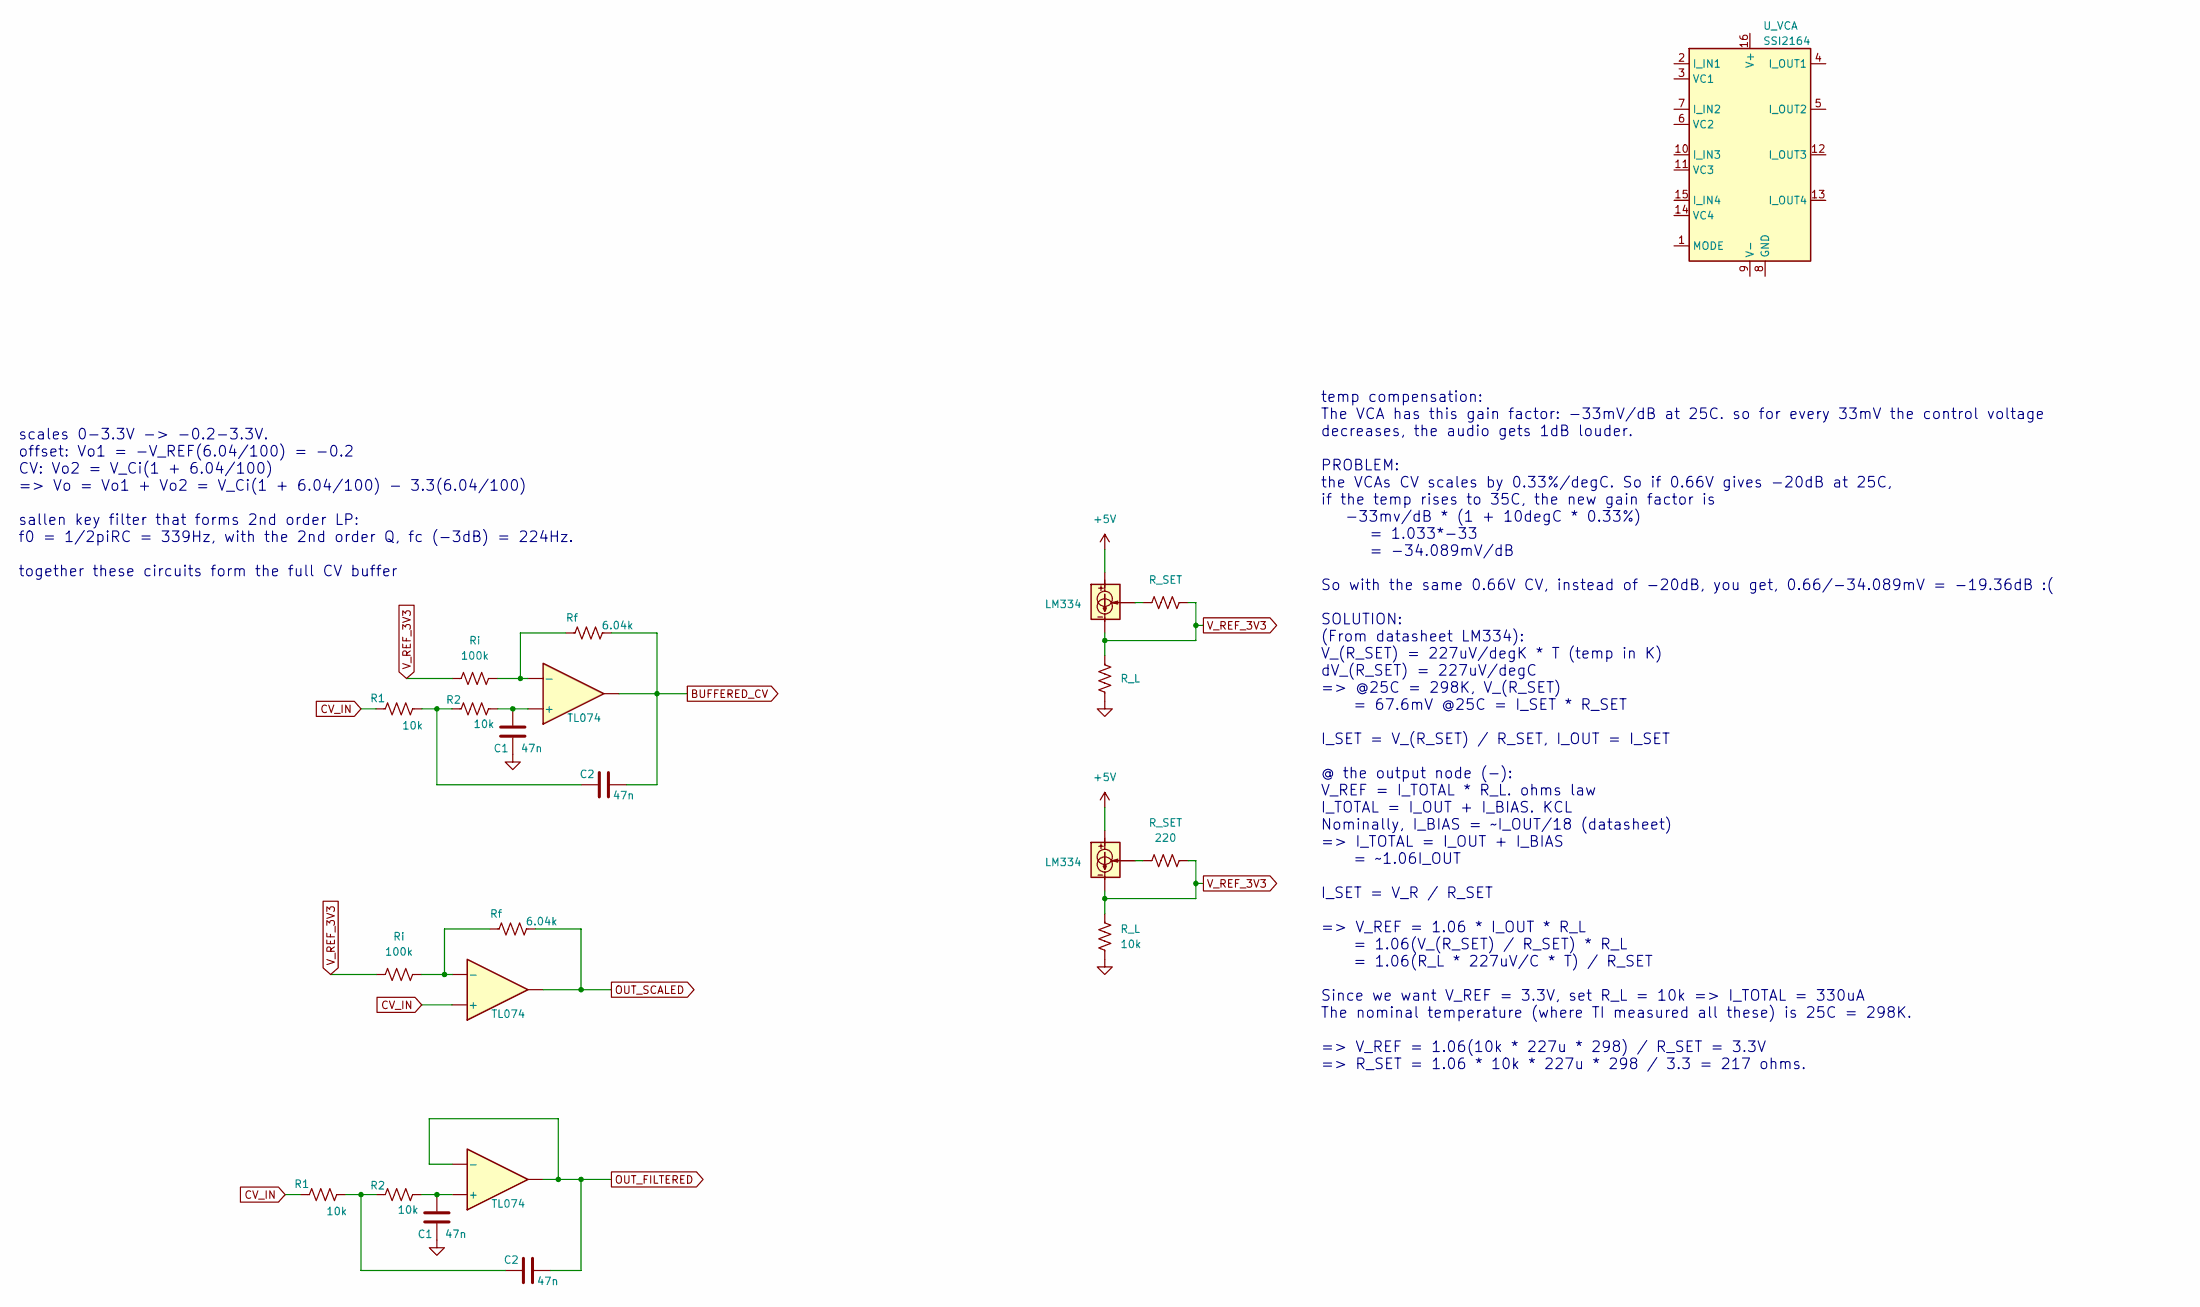
[picture p123: schematic ch_output_design.kicad_sch]

Parts:
C1, C2: 47n
R1, R2: 10k
R_L: 10k
R_SET: 240
Rf: 6.04k
Ri: 100k
U1, U4, U5: TL074
U2, U3: LM334; SOIC-8_3.9x4.9mm_P1.27mm
U_VCA: SSI2164; SOIC-16_3.9x9.9mm_P1.27mm

Connections:
+5V: U2.4, U3.4
BUFFERED_CV: C2.2, Rf.2, U1.1
CV_IN: R1.1, U4.3 (+)
GND: C1.2, R_L.2
unnamed: C1.1, R2.2, U1.3 (+), U5.3 (+)
unnamed: C2.1, R1.2, R2.1
unnamed: R_SET.1, U2.1, U3.1
unnamed: Rf.1, Ri.2, U1.2 (-), U4.2 (-)
OUT_FILTERED: C2.2, U5.1, U5.2 (-)
OUT_SCALED: Rf.2, U4.1
V_REF_3V3: R_L.1, R_SET.2, Ri.1, U2.2, U2.3, U2.6, U2.7, U3.2, U3.3, U3.6, U3.7

Notes on the sheet:
scales 0-3.3V -> -0.2-3.3V. offset: Vo1 = -V_REF(6.04/100) = -0.2 CV: Vo2 = V_Ci(1 + 6.04/100) => Vo = Vo1 + Vo2 = V_Ci(1 + 6.04/100) - 3.3(6.04/100) sallen key filter that forms 2nd order LP: f0 = 1/2piRC = 339Hz, with the 2nd order Q, fc (-3dB) = 224Hz. together these circuits form the full CV bu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
temp compensation: The VCA has this gain factor: -33mV/dB at 25C. so for every 33mV the control voltage decreases, the audio gets 1dB louder. PROBLEM: the VCAs CV scales by 0.33%/degC. So if 0.66V gives -20dB at 25C, if the temp rises to 35C, the new gain factor is -33mv/dB * (1 + 10degC * 0.33%) =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
