skylar-slideshows/Digilog_Capstone/Digilog_Remote/Source/config/CONFIG.yaml

# Knob layout configuration.
# pos is [x, y] in pixels, relative to the primary window's content area.
# min/max/default define the knob's range (negative ranges are allowed).
# color / indicator_color are optional [r, g, b] or [r, g, b, a] (0-255) lists -
# color tints the knob face/track, indicator_color tints the pointer/grab handle.
# Omit either field to use the default theme.
font: "assets/EnterCommand.ttf"
app_version: "1.0"
num_channels: 16
num_inserts: 16
insert_dropdown_pos: [45, 450]
group_label_size: 30
knob_label_size: 12
button_label_size: 14
state_file_extension: ".dgl"
# How long to wait for a "$ack ..." reply from the STM32 before resending, in milliseconds.
# Only used while a .dgl save file is being loaded and its commands are streamed to the device.
ack_timeout_ms: 100
# Debug aid for testing without a real STM32 attached: prints every sent message to the
# console in green, uses a 200ms/5-retry ack check that logs "no ack" in red on timeout,
# and (unlike normal operation) keeps sending the rest of the .dgl load sequence afterward
# instead of stopping and showing the no-connection popup.
debug_no_serial_timeout: false
logo_text: "DIGILOG REMOTE"
logo_pos: [230, 630]
logo_size: 50

# Theme colors (Dark and Light modes)
selected_window_top_bar_color: [130, 80, 220, 255]
selected_window_top_bar_light_color: [255, 155, 216, 255]

button_color: [70, 70, 90, 255]
button_light_color: [200, 200, 215, 255]

knob_color: [120, 120, 120, 255]
knob_light_color: [200, 200, 210, 255]

textbox_color: [30, 30, 40, 255]
textbox_light_color: [240, 240, 245, 255]

groups:
  - name: "INPUT"
    label_pos: [65, 25]
    knobs:
      - tag: input
        label: "GAIN"
        ctrl_id: 0
        pos: [75, 120]
        min: 0.0
        max: 100.0
        default: 0.0
        color: [120, 120, 120, 255]
        indicator_color: [255, 210, 90, 255]

    buttons:
      - tag: input_src
        label: ""
        sw_id: 0
        pos: [39, 70]
        size: 32
        type: "cycle"
        options: ["Line", "Mic", "Hi-Z"]
        default: 0

      - tag: phase
        label: "PHS"
        sw_id: 1
        pos: [39, 190]
        size: 32
        default: false
        on_color: [210, 200, 120, 255]

      - tag: 48v
        label: "+48V"
        sw_id: 2
        pos: [75, 190]
        size: 32
        default: false
        on_color: [220, 80, 80, 255]

      - tag: hpf
        label: "HPF"
        sw_id: 3
        pos: [111, 190]
        size: 32
        default: false
        on_color: [210, 200, 120, 255]
    
  - name: "SEND"
    label_pos: [220, 25]
    knobs:
      - tag: send_1
        label: "AUX 1"
        ctrl_id: 1
        pos: [190, 65]
        min: 0.0
        max: 100.0
        default: 0.0
        color: [120, 120, 120, 255]
        indicator_color: [255, 210, 90, 255]

      - tag: send_2
        label: "AUX 2"
        ctrl_id: 3
        pos: [190, 155]
        min: 0.0
        max: 100.0
        default: 0.0
        color: [120, 120, 120, 255]
        indicator_color: [255, 210, 90, 255]

      - tag: send_3
        label: "AUX 3"
        ctrl_id: 5
        pos: [190, 245]
        min: 0.0
        max: 100.0
        default: 0.0
        color: [120, 120, 120, 255]
        indicator_color: [255, 210, 90, 255]

      - tag: send_4
        label: "AUX 4 (Mono)"
        ctrl_id: 7
        pos: [190, 335]
        min: 0.0
        max: 100.0
        default: 0.0
        color: [120, 120, 120, 255]
        indicator_color: [255, 210, 90, 255]

      - tag: send_1_pan
        label: "PAN"
        ctrl_id: 2
        pos: [240, 95]
        min: -50.0
        max: 50.0
        default: 0
        indicator_color: [255, 210, 90, 255]

      - tag: send_2_pan
        label: "PAN"
        ctrl_id: 4
        pos: [240, 185]
        min: -50.0
        max: 50.0
        default: 0
        indicator_color: [255, 210, 90, 255]

      - tag: send_3_pan
        label: "PAN"
        ctrl_id: 6
        pos: [240, 275]
        min: -50.0
        max: 50.0
        default: 0
        indicator_color: [255, 210, 90, 255]

  - name: "EQ"
    label_pos: [360, 25]
    knobs:
      - tag: eq_1_gain
        label: "HF"
        ctrl_id: 8
        pos: [330, 65]
        min: -50.0
        max: 50.0
        default: 0
        color: [120, 120, 120, 255]
        indicator_color: [54, 10, 142, 255]

      - tag: eq_2_gain
        label: "HMF"
        ctrl_id: 10
        pos: [330, 155]
        min: -50.0
        max: 50.0
        default: 0
        color: [120, 120, 120, 255]
        indicator_color: [54, 10, 142, 255]

      - tag: eq_2_q
        label: "Q"
        ctrl_id: 12
        pos: [330, 215]
        min: -50.0
        max: 50.0
        default: 0
        indicator_color: [123, 80, 210, 255]

      - tag: eq_3_gain
        label: "LMF"
        ctrl_id: 13
        pos: [330, 295]
        min: -50.0
        max: 50.0
        default: 0
        color: [120, 120, 120, 255]
        indicator_color: [54, 10, 142, 255]

      - tag: eq_3_q
        label: "Q"
        ctrl_id: 15
        pos: [330, 355]
        min: 0.0
        max: 100.0
        default: 50.0
        indicator_color: [123, 80, 210, 255]
        
      - tag: eq_4_gain
        label: "LF"
        ctrl_id: 16
        pos: [330, 435]
        min: 0.0
        max: 100.0
        default: 50.0
        color: [120, 120, 120, 255]
        indicator_color: [54, 10, 142, 255]

      - tag: eq_1_freq
        label: "FREQ"
        ctrl_id: 9
        pos: [380, 95]
        min: 0.0
        max: 100.0
        default: 50.0
        indicator_color: [123, 80, 210, 255]

      - tag: eq_2_freq
        label: "FREQ"
        ctrl_id: 11
        pos: [380, 185]
        min: 0.0
        max: 100.0
        default: 50.0
        indicator_color: [123, 80, 210, 255]

      - tag: eq_3_freq
        label: "FREQ"
        ctrl_id: 14
        pos: [380, 325]
        min: 0.0
        max: 100.0
        default: 50.0
        indicator_color: [123, 80, 210, 255]

      - tag: eq_4_freq
        label: "FREQ"
        ctrl_id: 17
        pos: [380, 465]
        min: 0.0
        max: 100.0
        default: 50.0
        indicator_color: [123, 80, 210, 255]

  - name: "COMP"
    label_pos: [500, 25]
    knobs:
      - tag: comp_input
        label: "INPUT"
        ctrl_id: 18
        pos: [470, 65]
        min: 0.0
        max: 100.0
        default: 50.0
        color: [120, 120, 120, 255]
        indicator_color: [255, 210, 90, 255]

      - tag: comp_thresh
        label: "THRESH"
        ctrl_id: 20
        pos: [470, 155]
        min: 0.0
        max: 100.0
        default: 0.0
        color: [120, 120, 120, 255]
        indicator_color: [255, 210, 90, 255]

      - tag: comp_deess
        label: "DE-ESS"
        ctrl_id: 22
        pos: [470, 245]
        min: 0.0
        max: 100.0
        default: 0.0
        color: [120, 120, 120, 255]
        indicator_color: [255, 210, 90, 255]

      - tag: comp_output
        label: "OUTPUT"
        ctrl_id: 24
        pos: [470, 335]
        min: 0.0
        max: 100.0
        default: 50.0
        color: [120, 120, 120, 255]
        indicator_color: [255, 210, 90, 255]

      - tag: comp_atk
        label: "ATK"
        ctrl_id: 19
        pos: [520, 110]
        min: 0.0
        max: 100.0
        default: 50.0
        indicator_color: [255, 210, 90, 255]

      - tag: comp_rel
        label: "REL"
        ctrl_id: 21
        pos: [520, 200]
        min: 0.0
        max: 100.0
        default: 50.0
        indicator_color: [255, 210, 90, 255]

      - tag: comp_ratio
        label: "RATIO"
        ctrl_id: 23
        pos: [520, 290]
        min: 0.0
        max: 100.0
        default: 50.0
        indicator_color: [255, 210, 90, 255]

# standalone knobs that don't belong to a group
extra_knobs:
  - tag: pan
    label: "PAN"
    ctrl_id: 25
    pos: [640, 220]
    min: -50.0
    max: 50.0
    default: 0
    color: [100, 120, 160, 255]
    indicator_color: [255, 120, 120, 255]

# independent square toggle buttons above the PAN knob
toggles:
  - tag: solo
    label: "SOLO"
    sw_id: 4
    pos: [610, 175]
    size: 32
    default: false
    on_color: [210, 200, 120, 255]

  - tag: mute
    label: "MUTE"
    sw_id: 5
    pos: [646, 175]
    size: 32
    default: false
    on_color: [220, 80, 80, 255]

  - tag: sel
    label: "SEL"
    pos: [682, 175]
    size: 32
    default: false
    on_color: [210, 200, 120, 255]

  - tag: insert
    label: "INS"
    sw_id: 6
    pos: [682, 300]
    size: 32
    default: false
    on_color: [210, 200, 120, 255]

  - tag: pre
    label: "PRE"
    sw_id: 7
    pos: [682, 336]
    size: 32
    default: false
    on_color: [210, 200, 120, 255]

  - tag: light_theme
    label: "LIGHT"
    default: false
    on_color: [200, 200, 200, 255]

# vertical linear slider ("fader"), placed to the right of the groups
fader:
  tag: fader
  ctrl_id: 26
  label: ""
  pos: [645, 285]
  width: 30
  height: 260
  min: 0.0
  max: 100.0
  default: 80.0
  color: [70, 70, 90, 255]
  indicator_color: [120, 180, 255, 255]

# vertical divider lines - pos is [x, y] top of the bar, length is in pixels
vertical_bars:
  - pos: [155, 45]
    length: 500
    thickness: 2
    color: [90, 90, 90, 255]
  - pos: [295, 45]
    length: 500
    thickness: 2
    color: [90, 90, 90, 255]
  - pos: [435, 45]
    length: 500
    thickness: 2
    color: [90, 90, 90, 255]
  - pos: [575, 45]
    length: 500
    thickness: 2
    color: [90, 90, 90, 255]
