skylar-slideshows/Digilog_Capstone/Firmware/BucketController/Core/Src/control_integration/control_interface.c

#include <stdbool.h>
#include <stdint.h>
#include "CONFIG.h"
#include "fader_control.h"

#include "control_integration/control_interface.h"

#include "button_control.h"
#include "hardware_sets.h"
#include "hardware_state_sets.h"
#include "knob_control.h"
#include "portmacro.h"


/*=============================== LOGIC CONNECTING HARDWARE TO CONTROL VALUES ================================*/

/*
 * Holds all control values for all channels in the bucket
 * defined in control_interface.h
 */
channel_controls channel_control_vals[CHANNELS];
SemaphoreHandle_t channel_control_mutexes[CHANNELS];

/**
 * @brief Holds info on all control interface IO for all 4 channels in the bucket
 */
channel_control_io_t channel_controls_io[CHANNELS];
channel_control_io_state channel_states[CHANNELS];

static void init_control_io (uint8_t channel)
{
    init_button_controls(channel, &(channel_states[channel]), &(channel_controls_io[channel]));
    init_knob_controls(channel, &(channel_states[channel]), &(channel_controls_io[channel]));
    init_fader_controls(channel, &(channel_states[channel]), &(channel_controls_io[channel]));
}

static void init_control_vals (uint8_t channel)
{
    xSemaphoreTake(channel_control_mutexes[channel], portMAX_DELAY);

    channel_controls *vals = &(channel_control_vals[channel]);

    vals->input_type_selection = LINE_INPUT;
    vals->input_gain = 0;
    vals->output_gain = 0;
    vals->output_pan = 0;

    vals->phantom_48v = false;
    vals->phase_flip = false;
    vals->high_pass_filter = false;

    vals->muted = false;

    vals->ins = false;
    vals->pre_fader = false;
    vals->record = false;

    for (uint8_t send_channel = 0; send_channel < SEND_CHANNELS; send_channel++)
    {
        vals->send_controls[send_channel].gain = 0;
        vals->send_controls[send_channel].pan = 0;
    }

    const eq_band_control_t default_eq_band_control = {.freq = 0, .gain = 0, .q = U_SCALAR_CONTROL_MID};
    vals->hf_control = default_eq_band_control;
    vals->hmf_control = default_eq_band_control;
    vals->lmf_control = default_eq_band_control;
    vals->lf_control = default_eq_band_control;

    vals->comp_control.attack_time = U_SCALAR_CONTROL_MID;
    vals->comp_control.release_time = U_SCALAR_CONTROL_MID;
    vals->comp_control.in_gain = 0;
    vals->comp_control.out_gain = 0;
    vals->comp_control.threshold = 0;
    vals->comp_control.de_ess_amt = 0;
    vals->comp_control.ratio = 0;

    xSemaphoreGive(channel_control_mutexes[channel]);
}

void init_control_interface (void)
{
    for (uint8_t channel = 0; channel < CHANNELS; channel++)
    {
        channel_control_mutexes[channel] = xSemaphoreCreateMutex();

        init_control_io(channel);
        init_control_vals(channel);
    }
}

/**
 * Updates control values based on current/previous (cached) input (e.g button/rotary-encoder) states
 * Gpio expanders should have been polled to cache before running this
 */
void update_control_values (uint8_t channel)
{
    update_channel_knob_values(
        &(channel_control_mutexes[channel]),
        &(channel_control_vals[channel]),
        &(channel_states[channel]),
        &(channel_controls_io[channel]) //
    );
    update_channel_button_values(
        &(channel_control_mutexes[channel]),
        &(channel_control_vals[channel]),
        &(channel_states[channel]),
        &(channel_controls_io[channel]) //
    );
    update_channel_fader_values(
        &(channel_control_mutexes[channel]),
        &(channel_control_vals[channel]),
        &(channel_states[channel]),
        &(channel_controls_io[channel]) //
    );

    // TODO: non-button/encoder inputs maybe?
}

/*=============================== LOGIC CONNECTING CONTROL VALUES TO LEDS (TODO) ================================*/

/**
 * Updates LEDs / other visual outputs
 */
void update_control_leds (uint8_t channel)
{
    update_channel_knob_leds(
        &(channel_control_mutexes[channel]),
        &(channel_control_vals[channel]),
        &(channel_states[channel]),
        &(channel_controls_io[channel]) //
    );
    update_channel_button_leds(
        &(channel_control_mutexes[channel]),
        &(channel_control_vals[channel]),
        &(channel_states[channel]),
        &(channel_controls_io[channel]) //
    );
    update_channel_fader_hardware(
        &(channel_states[channel]),
        &(channel_controls_io[channel]) //
    );
    // TODO: non-button/encoder inputs maybe?
}
