skylar-slideshows/Digilog_Capstone/Firmware/BucketController/Core/Inc/control_interface.h

#ifndef CONTROL_INTERFACE_H
#define CONTROL_INTERFACE_H

#include <stdint.h>
#include <stdbool.h>

#include "CONFIG.h"

#define SEND_CHANNELS 4

typedef uint32_t u_scalar_control_t;
typedef int32_t s_scalar_control_t;

#define U_SCALAR_CONTROL_MAX UINT32_MAX
#define U_SCALAR_CONTROL_MID U_SCALAR_CONTROL_MAX >> 1

#define S_SCALAR_CONTROL_MAX INT32_MAX
#define S_SCALAR_CONTROL_MIN INT32_MIN

typedef enum
{
    MIC_INPUT,
    LINE_INPUT,
    HIZ_INPUT,
} channel_input_selection_t;

typedef enum
{
    SENDS_CONTROL,
    EQ_CONTROL,
    COMP_CONTROL,
} channel_control_set_selection_t;


typedef struct
{
    s_scalar_control_t gain; //!< TODO gain range
    u_scalar_control_t q;    //!< TODO q range(s)
    u_scalar_control_t freq; //!< TODO freq range(s)
} eq_band_control_t;

typedef struct
{
    s_scalar_control_t gain; //!< TODO desc / gain range
    s_scalar_control_t pan;  //!< TODO desc / pan range; note only applies to sends 1-3
} send_channel_control_t;

typedef struct
{
    s_scalar_control_t in_gain;  //!< TODO desc / gain range (dB-like)
    u_scalar_control_t out_gain; //!< TODO desc / gain range (dB-like)

    u_scalar_control_t attack_time;  //!< Time before gain is reduced after vol>threshold / attack range (time; 100us-100ms ish)
    u_scalar_control_t release_time; //!< TODO desc / release range (time; 10ms-5sec ish)
    s_scalar_control_t threshold;    //!< Max volume of input / TODO thresh range (dB-like)
    u_scalar_control_t ratio;        //!< TODO desc / ratio range (unitless on log scale; 0 = 1, MAX/2 = 4, MAX=~inf or 40)
    u_scalar_control_t de_ess_amt;   //!< TODO desc / De-Ess Amt range (dB-like; same units as threshold)
} comp_control_t;


/**
 * @brief Full set of control values on a channel
 */
typedef struct
{
    /* OTHER CHANNEL STUFF */

    channel_input_selection_t input_type_selection; //!< Mic/Line/Hi-Z input type

    s_scalar_control_t input_gain;  //!< TODO desc / gain range (dB-like)
    s_scalar_control_t output_gain; //!< TODO desc / gain range (dB-like)
    s_scalar_control_t output_pan;  //!< TODO desc / pan range

    bool phantom_48v;      //!< TODO
    bool phase_flip;       //!< TODO
    bool high_pass_filter; //!< TODO

    bool muted; //!< Whether all output from this channel is muted

    bool ins;       //!< TODO
    bool pre_fader; //!< TODO
    bool record;    //!< TODO

    /* SENDS STUFF */

    send_channel_control_t send_controls[SEND_CHANNELS]; //!< Controls for send channels 1-4

    /* EQ STUFF */

    eq_band_control_t hf_control;  //!< EQ controls for the HF band
    eq_band_control_t hmf_control; //!< EQ controls for the HMF band
    eq_band_control_t lmf_control; //!< EQ controls for the LMF band
    eq_band_control_t lf_control;  //!< EQ controls for the LF band

    /* COMP STUFF */

    comp_control_t comp_control; //!< Compressor controls
} channel_controls;


/**
 * @brief Holds all control values for all channels in the bucket
 */
channel_controls channel_control_vals[CHANNELS];


/**
 * @brief Sets default channel control values and hardware configurations. Call before using control values.
 */
void init_control_interface (void);

/**
 * @brief Updates control values based on current/previous (cached) input (e.g button/rotary-encoder) states
 */
void update_control_values (void);

#endif
