skylar-slideshows/Digilog_Capstone/Firmware/BucketController/Core/Src/hardware_drivers/74hc595.c

/**
  **********************************************************************************
  * SHIFT REGISTER DRIVER - DIGILOG CONSOLE
  **********************************************************************************
  * @file 74hc595.c
  * @brief Skylar's driver for the 74HC595 shift registers, to run comms w/
  *        shift registers that expand GP outputs and drive the LEDs
  *
  * @author Skylar Denno (denno.o@northeastern.edu)
  * @date 2026-08-31
  * @version 1.1
  *
  * @attention
  *  Copyright (C) 2026 Skylar Denno
  *
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
  *  The above copyright notice and this permission notice shall be included in all
  *  copies or substantial portions of the Software.
  *  THE SOFTWARE IS PROVIDED “AS IS”, WITHOUT WARRANTY OF ANY KIND, EXPRESS OR IMPLIED,
  *  INCLUDING BUT NOT LIMITED TO THE WARRANTIES OF MERCHANTABILITY, FITNESS FOR A
  *  PARTICULAR PURPOSE AND NONINFRINGEMENT. IN NO EVENT SHALL THE AUTHORS OR COPYRIGHT
  *  HOLDERS BE LIABLE FOR ANY CLAIM, DAMAGES OR OTHER LIABILITY, WHETHER IN AN ACTION OF
  *  CONTRACT, TORT OR OTHERWISE, ARISING FROM, OUT OF OR IN CONNECTION WITH THE SOFTWARE
  *  OR THE USE OR OTHER DEALINGS IN THE SOFTWARE.
  **********************************************************************************
*/

#include "stm32g4xx.h"
#include "CONFIG.h"
#include "hardware_drivers/74hc595.h"


// BSRR register: reset[15:0]set[15:0]. A 1 in the lower 16 bits will set the
// corresponding pin to high. A 1 in the upper 16 bits will set the corresponding
// pin to low.
#define RCLK_SET  (1U << LED_RCLK_PIN)
#define RCLK_RST  (1U << (LED_RCLK_PIN + 16))

#define SHIFTREG_SER_SET   (1U << SHIFTREG_SER_PIN)
#define SHIFTREG_SER_RST   (1U << (SHIFTREG_SER_PIN + 16))
#define SHIFTREG_SRCLK_SET (1U << SHIFTREG_SRCLK_PIN)
#define SHIFTREG_SRCLK_RST (1U << (SHIFTREG_SRCLK_PIN + 16))
#define SHIFTREG_RCLK_SET  (1U << SHIFTREG_RCLK_PIN)
#define SHIFTREG_RCLK_RST  (1U << (SHIFTREG_RCLK_PIN + 16))

static uint32_t half_cyc; // 177 cycles at 170MHz/480kHz

#define BOYMODER MODER
#define MODE_OUT(port, pin) do { \
    (port)->BOYMODER = ((port)->BOYMODER & ~(3U << ((pin) * 2))) | (1U << ((pin) * 2)); \
    (port)->OSPEEDR |= (3U << ((pin) * 2)); \
} while (0)


/**
 ----------------------------------------------------------------------------------
  @brief INTERNAL wait_half : Count half cycle of serial LED out clock
 ----------------------------------------------------------------------------------
*/
static inline void wait_half(void)
{
    uint32_t t0 = DWT->CYCCNT;
    while ((DWT->CYCCNT - t0) < half_cyc) { }
}


/**
 ----------------------------------------------------------------------------------
  @brief PUBLIC shift_bit : uint32 -> Shifts a single bit out.
 ----------------------------------------------------------------------------------
*/
void shift_bit(uint32_t bit)
{
    SHIFTREG_DATA_PORT->BSRR = (bit ? SHIFTREG_SER_SET : SHIFTREG_SER_RST) | SHIFTREG_SRCLK_RST;
        wait_half();
        SHIFTREG_DATA_PORT->BSRR = SHIFTREG_SRCLK_SET;
        wait_half();
}


/**
 ----------------------------------------------------------------------------------
  @brief PUBLIC shift_byte : Shift out a whole byte to the DAC LDAC shift registers
  (DAC ONLY NO LED). Goes LSB to MSB
 ----------------------------------------------------------------------------------
*/
void shift_byte(uint8_t byte)
{
    for(uint8_t i = 0; i < 8; i++)
    { shift_bit((byte >> i) & 1); }
}


/**
 ----------------------------------------------------------------------------------
  @brief PUBLIC latch_out : Pulse latch low to update register outputs
 ----------------------------------------------------------------------------------
*/
void latch_out(bool led)
{
    if(led)
    {
        LED_DATA_PORT->BSRR = RCLK_SET;
        __NOP(); __NOP(); // very short delay lol
        LED_DATA_PORT->BSRR = RCLK_RST;
    } else {
        SHIFTREG_DATA_PORT->BSRR = SHIFTREG_SRCLK_RST;
        wait_half();
        SHIFTREG_DATA_PORT->BSRR = SHIFTREG_RCLK_SET;
        wait_half();
        SHIFTREG_DATA_PORT->BSRR = SHIFTREG_RCLK_RST;
    }
}


/**
 ----------------------------------------------------------------------------------
  @brief PUBLIC led_shiftreg_init : Set up pins for the shift registers for leds (serial, clock, latch)
 ----------------------------------------------------------------------------------
*/
void led_shiftreg_init(void)
{

    half_cyc = ((uint64_t)(CPU_HZ) / ((uint64_t)2UL * (uint64_t)SHIFT_REG_SERIAL_HZ));

    CoreDebug->DEMCR |= CoreDebug_DEMCR_TRCENA_Msk; // Debug exception & monitor ctrl register setup, trace enable
    DWT->CYCCNT = 0; // cycle counter for PWM speed
    DWT->CTRL |= DWT_CTRL_CYCCNTENA_Msk; // enable cycle counter. PWM period based on number of CPU clock cycles

    RCC->AHB2ENR |= LED_DATA_PORT_EN | LED_OE_PORT_EN; // enables GPIO pins
    RCC->APB2ENR |= LED_OE_TIM_EN; // enables Timer 1

    LED_OE_PORT->BSRR = (1U << LED_OE_PIN); // set OE high (OE active low so hide all LEDs first)
    MODE_OUT(LED_OE_PORT, LED_OE_PIN);

    MODE_OUT(LED_DATA_PORT, LED_RCLK_PIN);
    LED_DATA_PORT->BSRR = RCLK_RST;
    MODE_OUT(LED_DATA_PORT, LED_RCLK_PIN); // latch pin
    
}


/**
 ----------------------------------------------------------------------------------
  @brief PUBLIC shiftreg_init : Set up pins for the shift registers for MCP4728 address programming (serial, clock, latch)
 ----------------------------------------------------------------------------------
*/
void shiftreg_init(void)
{

    half_cyc = ((uint64_t)(CPU_HZ) / ((uint64_t)2UL * (uint64_t)SHIFT_REG_SERIAL_HZ));

    CoreDebug->DEMCR |= CoreDebug_DEMCR_TRCENA_Msk; // Debug exception & monitor ctrl register setup, trace enable
    DWT->CYCCNT = 0; // cycle counter for PWM speed
    DWT->CTRL |= DWT_CTRL_CYCCNTENA_Msk; // enable cycle counter. PWM period based on number of CPU clock cycle

    MODE_OUT(SHIFTREG_DATA_PORT, SHIFTREG_SER_PIN); // initialize the pins needed - serial data
    MODE_OUT(SHIFTREG_DATA_PORT, SHIFTREG_SRCLK_PIN); // serial clock
    MODE_OUT(SHIFTREG_DATA_PORT, SHIFTREG_RCLK_PIN); // latch pin
    SHIFTREG_DATA_PORT->BSRR = SHIFTREG_SER_RST | SHIFTREG_SRCLK_RST;
    SHIFTREG_DATA_PORT->BSRR = SHIFTREG_RCLK_RST;
    
}
