skylar-slideshows/Digilog_Capstone/Firmware/BucketController/Core/Inc/cpp_template.hpp

/**
  **********************************************************************************
  * C++ HEADER BRIDGE TEMPLATE
  **********************************************************************************
  * @file cpp_template.hpp
  * @brief C++ HEADER BRIDGE TEMPLATE
  *
  * @author Skylar Denno (denno.o@northeastern.edu)
  * @date 2026-08-20
  * @version 1.0
  * @copyright No copyright
  **********************************************************************************
*/

#pragma once
#ifdef __cplusplus

extern "C"
{
    #endif
    void app_main(void);
    #ifdef __cplusplus
}

// Don't forget to include in CMakeLists

#endif
