skylar-slideshows/Digilog_Capstone/Firmware/BucketController/Core/Src/cpp_template.cpp

/**
  **********************************************************************************
  * C++ STM32 APP TEMPLATE
  **********************************************************************************
  * @file cpp_template.cpp
  * @brief C++ STM32 APP TEMPLATE
  *
  * @author Skylar Denno (denno.o@northeastern.edu)
  * @date 2026-08-20
  * @version 1.0
  * @copyright No copyright
  **********************************************************************************
*/

#include "cpp_template.hpp"

#ifndef LD2_Pin
#endif

/******************************************************************************/


void app_main(void) { }
